mfkiwl/Zynq-SoM/schematic/DDR3L.kicad_sch

## KiCad design schematic/DDR3L.kicad_sch (2025-04-01)

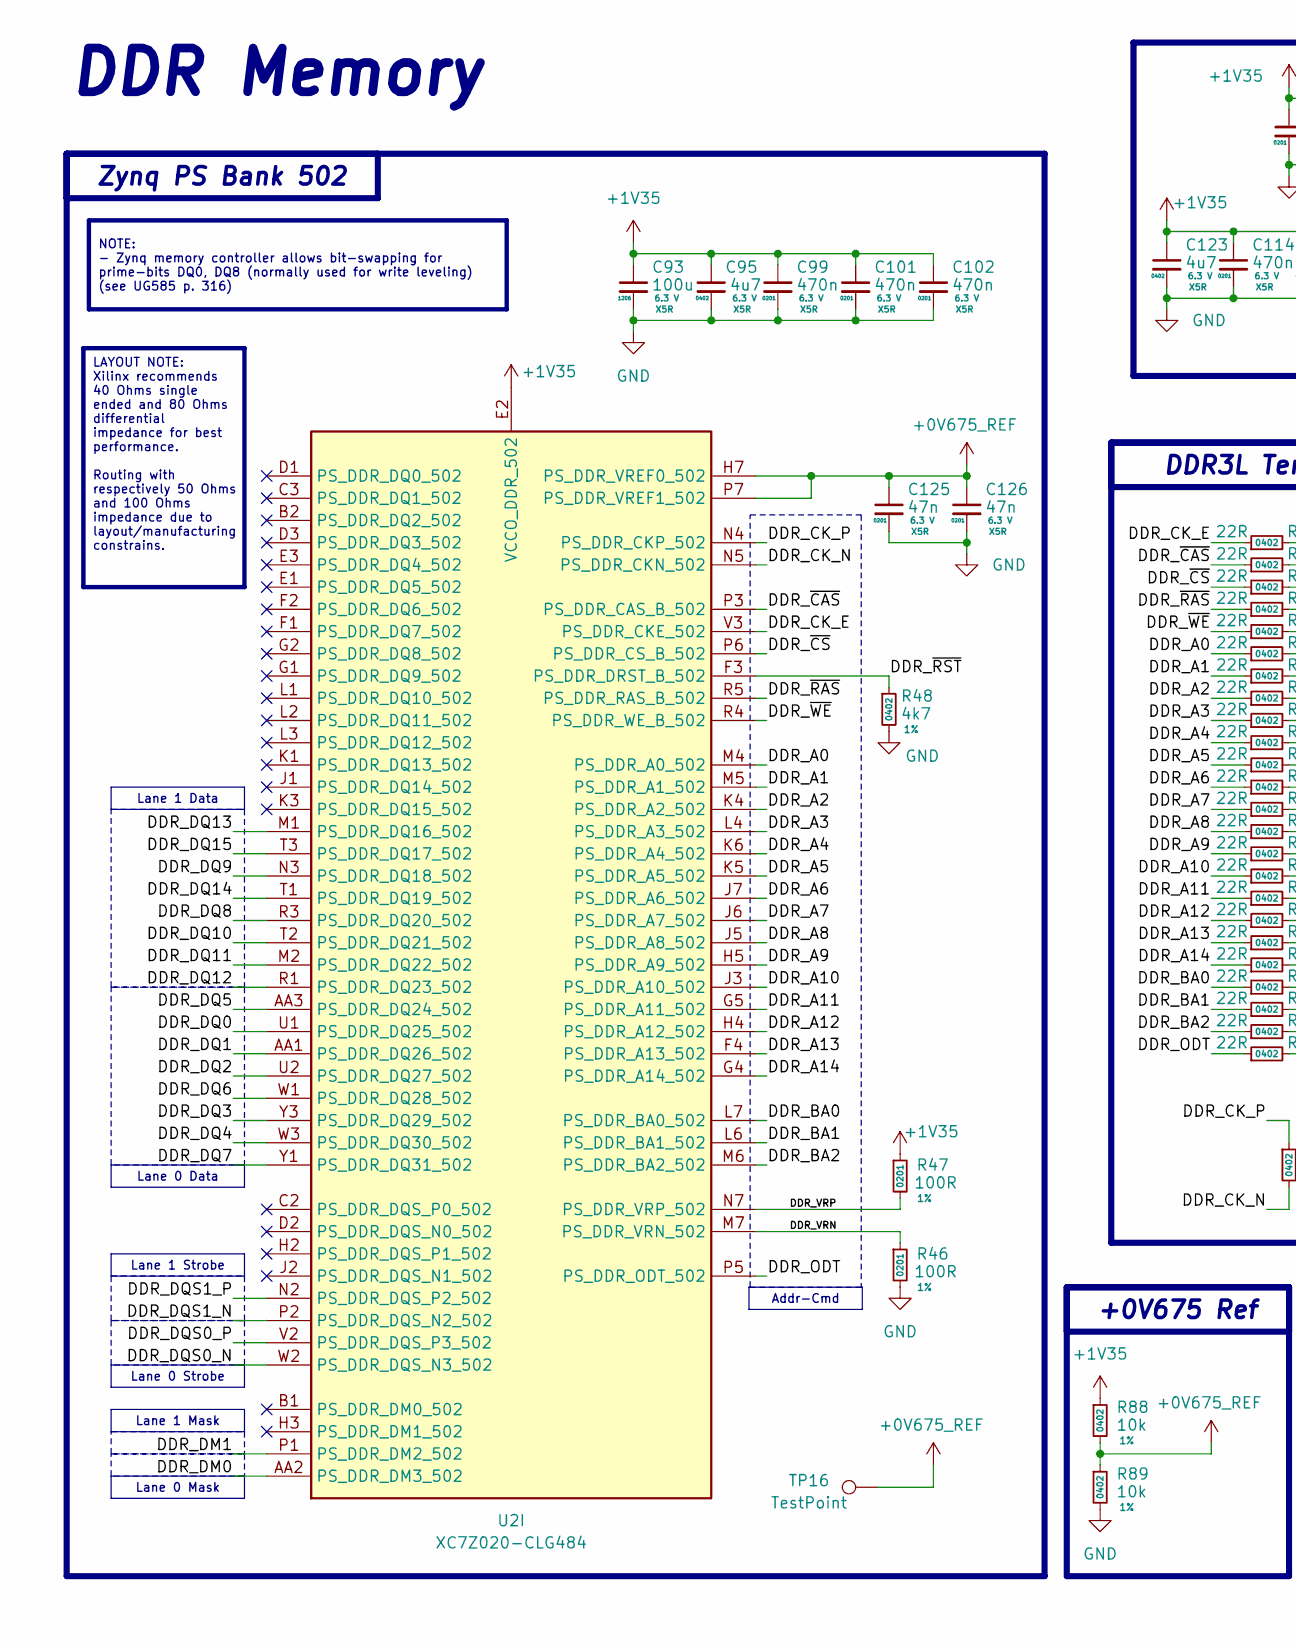
[picture p17: schematic DDR3L.kicad_sch, part in row 1, column 1]

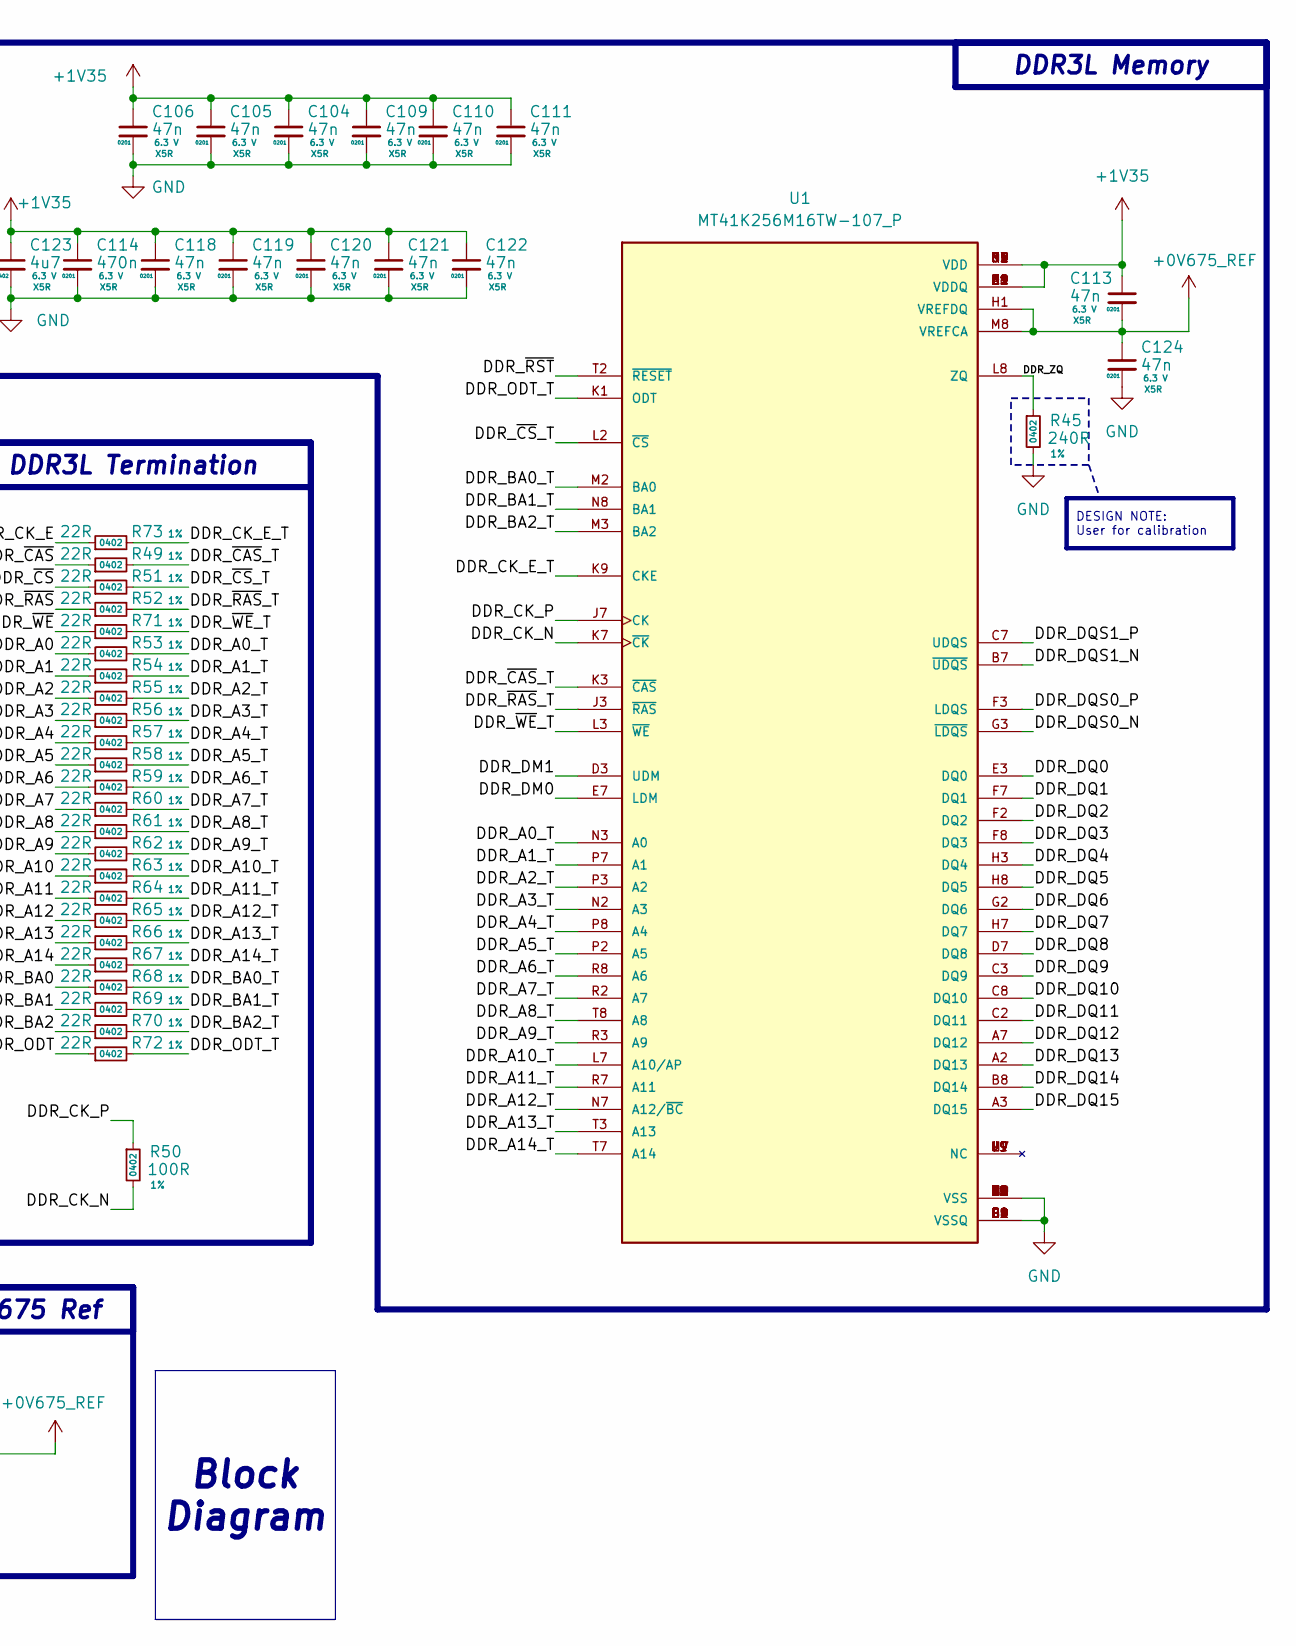
[picture p18: schematic DDR3L.kicad_sch, part in row 1, column 2]

Parts:
C93: 100u; C_1206_3216Metric; Rating 6.3 V; LCSC Part C15008
C95, C123: 4u7; C_0402_1005Metric; Rating 6.3 V; LCSC Part C368809
C99, C101, C102, C114: 470n; C_0201_0603Metric; Rating 6.3 V; LCSC Part C85926
C104, C105, C106, C109, C110, C111, C113, C118, C119, C120, C121, C122, C124, C125, C126: 47n; C_0201_0603Metric; Rating 6.3 V; LCSC Part C85925
R45: 240R; R_0402_1005Metric; Tolerance 1%; LCSC Part C25094
R46, R47: 100R; R_0201_0603Metric; Tolerance 1%; LCSC Part C270336
R48: 4k7; R_0402_1005Metric; Tolerance 1%; LCSC Part C25940
R49, R51, R52, R53, R54, R55, R56, R57, R58, R59, R60, R61, R62, R63, R64, R65, R66, R67, R68, R69, R70, R71, R72, R73: 22R; R_0402_1005Metric; Tolerance 1%; LCSC Part C114765/C25105
R50: 100R; R_0402_1005Metric; Tolerance 1%; LCSC Part C25138
R88, R89: 10k; R_0402_1005Metric; Tolerance 1%; LCSC Part C25744/gia
TP16: TestPoint; TestPoint_Pad_D0.7mm
U1: MT41K256M16TW-107_P; BGA96C80P9X16_1400X800X120; PARTREV P; LCSC Part gia
U2: XC7Z020-CLG484; CLG484_XIL-L_new; LCSC Part gia

Connections:
+0V675_REF: C113.2, C124.1, C125.1, C126.1, R88.2, R89.1, TP16.1, U1.H1 (VREFDQ), U1.M8 (VREFCA), U2.H7 (PS_DDR_VREF0_502), U2.P7 (PS_DDR_VREF1_502)
+1V35: C93.1, C95.1, C99.1, C101.1, C102.1, C104.1, C105.1, C106.1, C109.1, C110.1, C111.1, C113.1, C114.1, C118.1, C119.1, C120.1, C121.1, C122.1, C123.1, R47.1, R88.1, U1.A1 (VDDQ), U1.A8 (VDDQ), U1.B2 (VDD), U1.C1 (VDDQ), U1.C9 (VDDQ), U1.D2 (VDDQ), U1.D9 (VDD), U1.E9 (VDDQ), U1.F1 (VDDQ), U1.G7 (VDD), U1.H2 (VDDQ), U1.H9 (VDDQ), U1.K2 (VDD), U1.K8 (VDD), U1.N1 (VDD), U1.N9 (VDD), U1.R1 (VDD), U1.R9 (VDD), U2.E2 (VCCO_DDR_502), U2.F5 (VCCO_DDR_502), U2.H1 (VCCO_DDR_502), U2.J4 (VCCO_DDR_502), U2.K7 (VCCO_DDR_502), U2.M3 (VCCO_DDR_502), U2.N6 (VCCO_DDR_502), U2.R2 (VCCO_DDR_502), U2.V1 (VCCO_DDR_502)
DDR_A0: R53.1, U2.M4 (PS_DDR_A0_502)
DDR_A0_T: R53.2, U1.N3 (A0)
DDR_A1: R54.1, U2.M5 (PS_DDR_A1_502)
DDR_A1_T: R54.2, U1.P7 (A1)
DDR_A2: R55.1, U2.K4 (PS_DDR_A2_502)
DDR_A2_T: R55.2, U1.P3 (A2)
DDR_A3: R56.1, U2.L4 (PS_DDR_A3_502)
DDR_A3_T: R56.2, U1.N2 (A3)
DDR_A4: R57.1, U2.K6 (PS_DDR_A4_502)
DDR_A4_T: R57.2, U1.P8 (A4)
DDR_A5: R58.1, U2.K5 (PS_DDR_A5_502)
DDR_A5_T: R58.2, U1.P2 (A5)
DDR_A6: R59.1, U2.J7 (PS_DDR_A6_502)
DDR_A6_T: R59.2, U1.R8 (A6)
DDR_A7: R60.1, U2.J6 (PS_DDR_A7_502)
DDR_A7_T: R60.2, U1.R2 (A7)
DDR_A8: R61.1, U2.J5 (PS_DDR_A8_502)
DDR_A8_T: R61.2, U1.T8 (A8)
DDR_A9: R62.1, U2.H5 (PS_DDR_A9_502)
DDR_A9_T: R62.2, U1.R3 (A9)
DDR_A10: R63.1, U2.J3 (PS_DDR_A10_502)
DDR_A10_T: R63.2, U1.L7 (A10/AP)
DDR_A11: R64.1, U2.G5 (PS_DDR_A11_502)
DDR_A11_T: R64.2, U1.R7 (A11)
DDR_A12: R65.1, U2.H4 (PS_DDR_A12_502)
DDR_A12_T: R65.2, U1.N7 (A12/~BC)
DDR_A13: R66.1, U2.F4 (PS_DDR_A13_502)
DDR_A13_T: R66.2, U1.T3 (A13)
DDR_A14: R67.1, U2.G4 (PS_DDR_A14_502)
DDR_A14_T: R67.2, U1.T7 (A14)
DDR_BA0: R68.1, U2.L7 (PS_DDR_BA0_502)
DDR_BA0_T: R68.2, U1.M2 (BA0)
DDR_BA1: R69.1, U2.L6 (PS_DDR_BA1_502)
DDR_BA1_T: R69.2, U1.N8 (BA1)
DDR_BA2: R70.1, U2.M6 (PS_DDR_BA2_502)
DDR_BA2_T: R70.2, U1.M3 (BA2)
DDR_CK_E: R73.1, U2.V3 (PS_DDR_CKE_502)
DDR_CK_E_T: R73.2, U1.K9 (CKE)
DDR_CK_N: R50.2, U1.K7 (~CK), U2.N5 (PS_DDR_CKN_502)
DDR_CK_P: R50.1, U1.J7 (CK), U2.N4 (PS_DDR_CKP_502)
DDR_DM0: U1.E7 (LDM), U2.AA2 (PS_DDR_DM3_502)
DDR_DM1: U1.D3 (UDM), U2.P1 (PS_DDR_DM2_502)
DDR_DQ0: U1.E3 (DQ0), U2.U1 (PS_DDR_DQ25_502)
DDR_DQ1: U1.F7 (DQ1), U2.AA1 (PS_DDR_DQ26_502)
DDR_DQ2: U1.F2 (DQ2), U2.U2 (PS_DDR_DQ27_502)
DDR_DQ3: U1.F8 (DQ3), U2.Y3 (PS_DDR_DQ29_502)
DDR_DQ4: U1.H3 (DQ4), U2.W3 (PS_DDR_DQ30_502)
DDR_DQ5: U1.H8 (DQ5), U2.AA3 (PS_DDR_DQ24_502)
DDR_DQ6: U1.G2 (DQ6), U2.W1 (PS_DDR_DQ28_502)
DDR_DQ7: U1.H7 (DQ7), U2.Y1 (PS_DDR_DQ31_502)
DDR_DQ8: U1.D7 (DQ8), U2.R3 (PS_DDR_DQ20_502)
DDR_DQ9: U1.C3 (DQ9), U2.N3 (PS_DDR_DQ18_502)
DDR_DQ10: U1.C8 (DQ10), U2.T2 (PS_DDR_DQ21_502)
DDR_DQ11: U1.C2 (DQ11), U2.M2 (PS_DDR_DQ22_502)
DDR_DQ12: U1.A7 (DQ12), U2.R1 (PS_DDR_DQ23_502)
DDR_DQ13: U1.A2 (DQ13), U2.M1 (PS_DDR_DQ16_502)
DDR_DQ14: U1.B8 (DQ14), U2.T1 (PS_DDR_DQ19_502)
DDR_DQ15: U1.A3 (DQ15), U2.T3 (PS_DDR_DQ17_502)
DDR_DQS0_N: U1.G3 (~LDQS), U2.W2 (PS_DDR_DQS_N3_502)
DDR_DQS0_P: U1.F3 (LDQS), U2.V2 (PS_DDR_DQS_P3_502)
DDR_DQS1_N: U1.B7 (~UDQS), U2.P2 (PS_DDR_DQS_N2_502)
DDR_DQS1_P: U1.C7 (UDQS), U2.N2 (PS_DDR_DQS_P2_502)
DDR_ODT: R72.1, U2.P5 (PS_DDR_ODT_502)
DDR_ODT_T: R72.2, U1.K1 (ODT)
DDR_VRN: R46.1, U2.M7 (PS_DDR_VRN_502)
DDR_VRP: R47.2, U2.N7 (PS_DDR_VRP_502)
DDR_ZQ: R45.1, U1.L8 (ZQ)
DDR_~CAS: R49.1, U2.P3 (PS_DDR_CAS_B_502)
DDR_~CAS_T: R49.2, U1.K3 (~CAS)
DDR_~CS: R51.1, U2.P6 (PS_DDR_CS_B_502)
DDR_~CS_T: R51.2, U1.L2 (~CS)
DDR_~RAS: R52.1, U2.R5 (PS_DDR_RAS_B_502)
DDR_~RAS_T: R52.2, U1.J3 (~RAS)
DDR_~RST: R48.1, U1.T2 (~RESET), U2.F3 (PS_DDR_DRST_B_502)
DDR_~WE: R71.1, U2.R4 (PS_DDR_WE_B_502)
DDR_~WE_T: R71.2, U1.L3 (~WE)
GND: C93.2, C95.2, C99.2, C101.2, C102.2, C104.2, C105.2, C106.2, C109.2, C110.2, C111.2, C114.2, C118.2, C119.2, C120.2, C121.2, C122.2, C123.2, C124.2, C125.2, C126.2, R45.2, R46.2, R48.2, R89.2, U1.A9 (VSS), U1.B1 (VSSQ), U1.B3 (VSS), U1.B9 (VSSQ), U1.D1 (VSSQ), U1.D8 (VSSQ), U1.E1 (VSS), U1.E2 (VSSQ), U1.E8 (VSSQ), U1.F9 (VSSQ), U1.G1 (VSSQ), U1.G8 (VSS), U1.G9 (VSSQ), U1.J2 (VSS), U1.J8 (VSS), U1.M1 (VSS), U1.M9 (VSS), U1.P1 (VSS), U1.P9 (VSS), U1.T1 (VSS), U1.T9 (VSS)
unnamed: U1.J1 (NC), U1.J9 (NC), U1.L1 (NC), U1.L9 (NC), U1.M7 (NC)

Notes on the sheet:
DDR Memory
Zynq PS Bank 502
Lane 1 Strobe
Lane 1 Data
Lane 0 Mask
DESIGN NOTE: User for calibration
Addr-Cmd
NOTE: - Zynq memory controller allows bit-swapping for prime-bits DQ0, DQ8 (normally used for write leveling) (see UG585 p. 316)
Block Diagram
Lane 0 Data
LAYOUT NOTE: Xilinx recommends 40 Ohms single ended and 80 Ohms differential impedance for best performance. Routing with respectively 50 Ohms and 100 Ohms impedance due to layout/manufacturing constrains.
+0V675 Ref
DDR3L Memory
Lane 1 Mask
Lane 0 Strobe
DDR3L Termination
