mfkiwl/Zynq-SoM/schematic/Ethernet PHY.kicad_sch

## KiCad design schematic/Ethernet PHY.kicad_sch (2025-04-01)

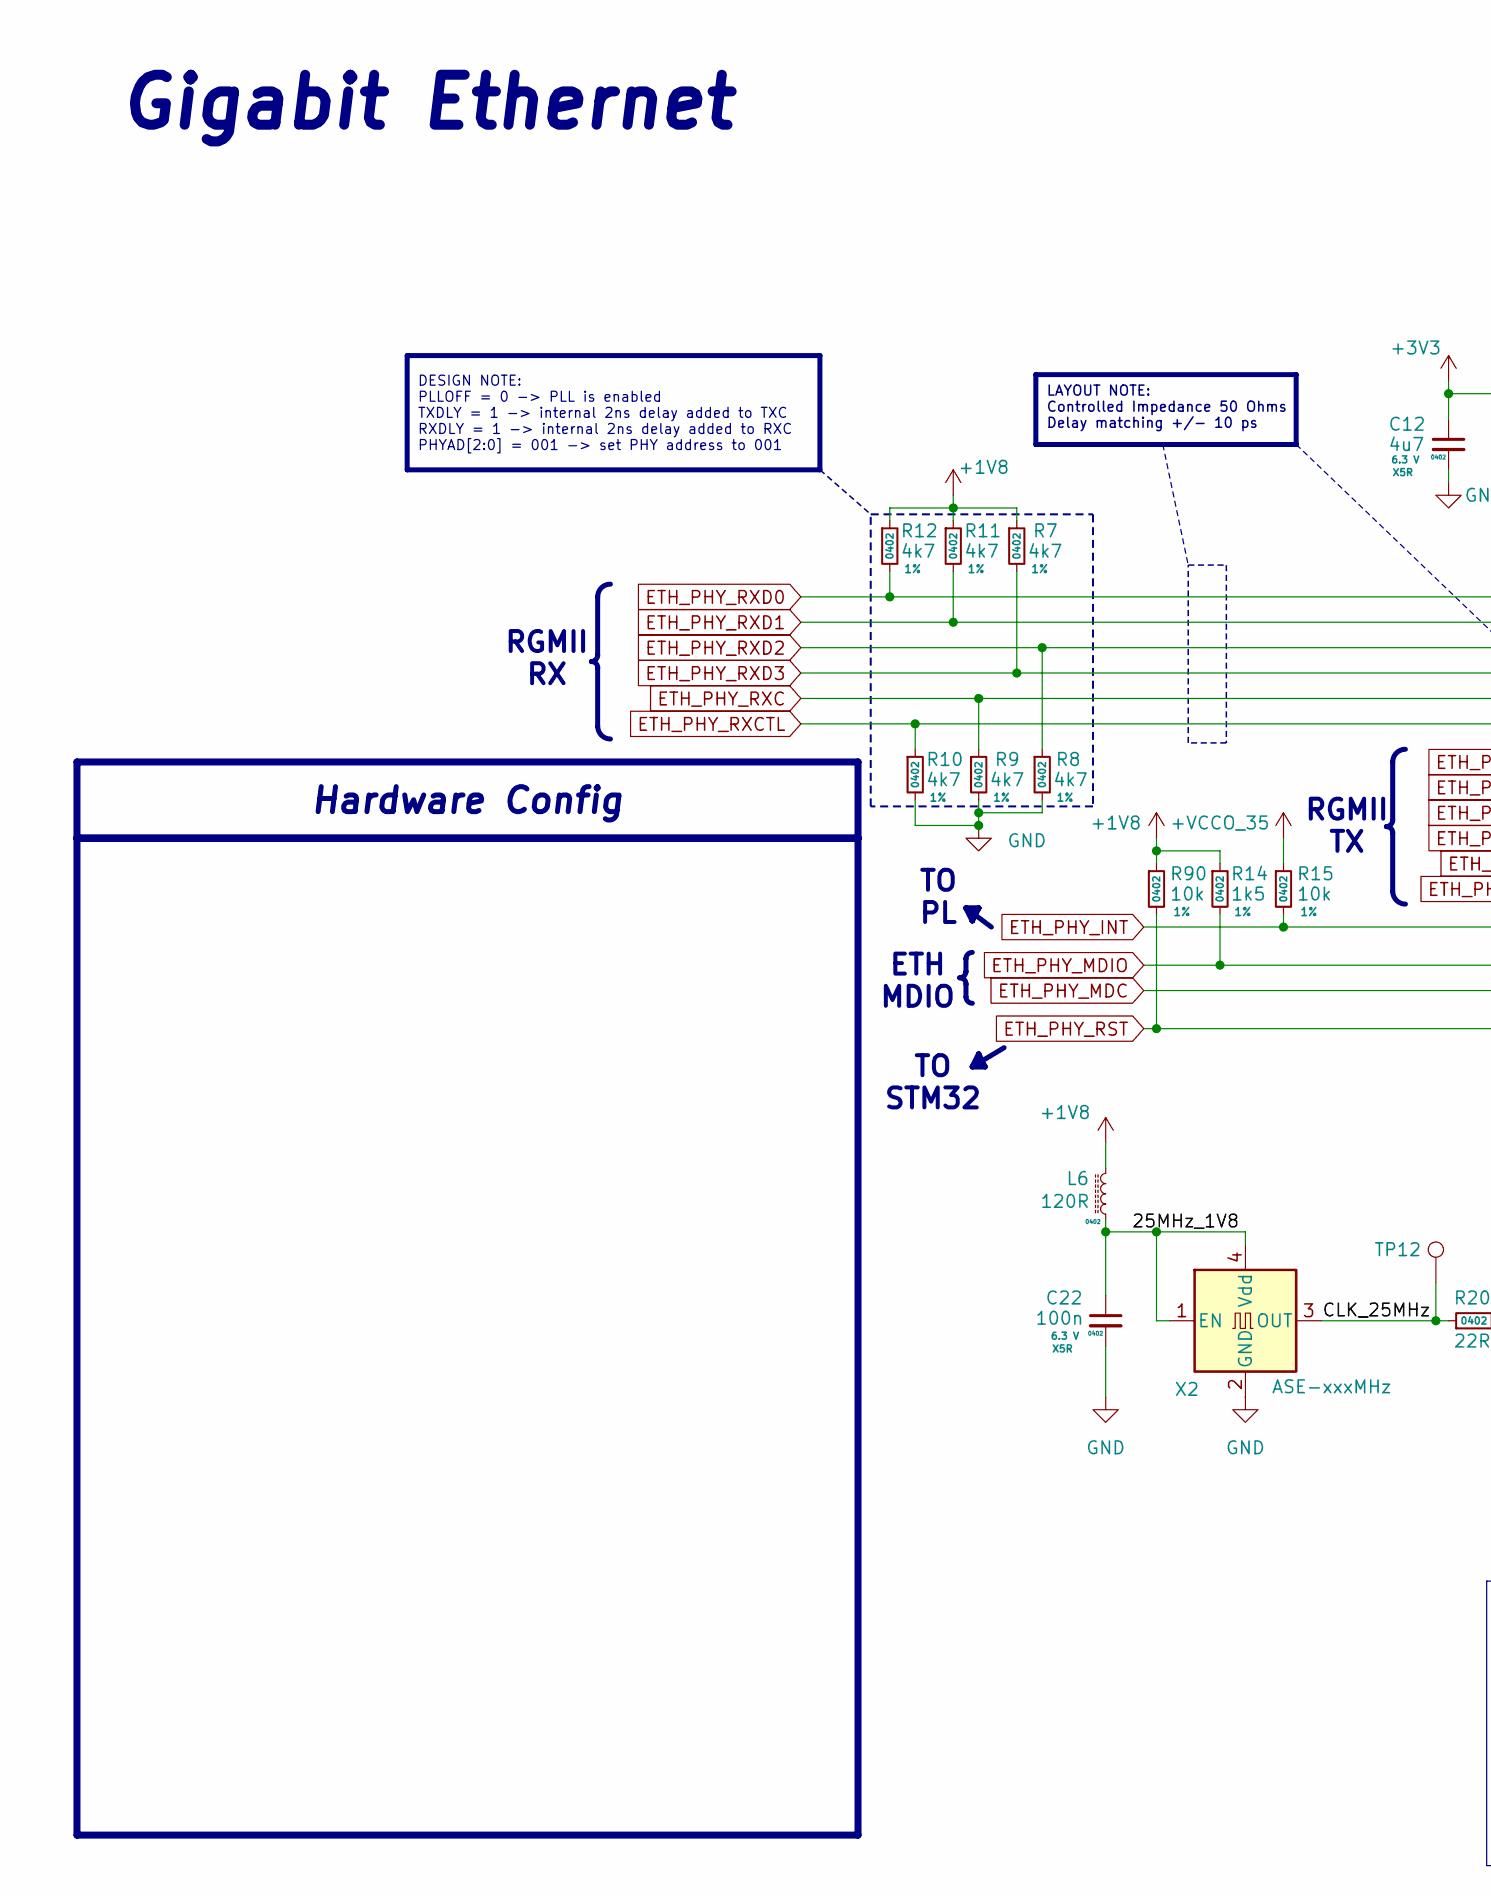
[picture p19: schematic Ethernet PHY.kicad_sch, part in row 1, column 1]

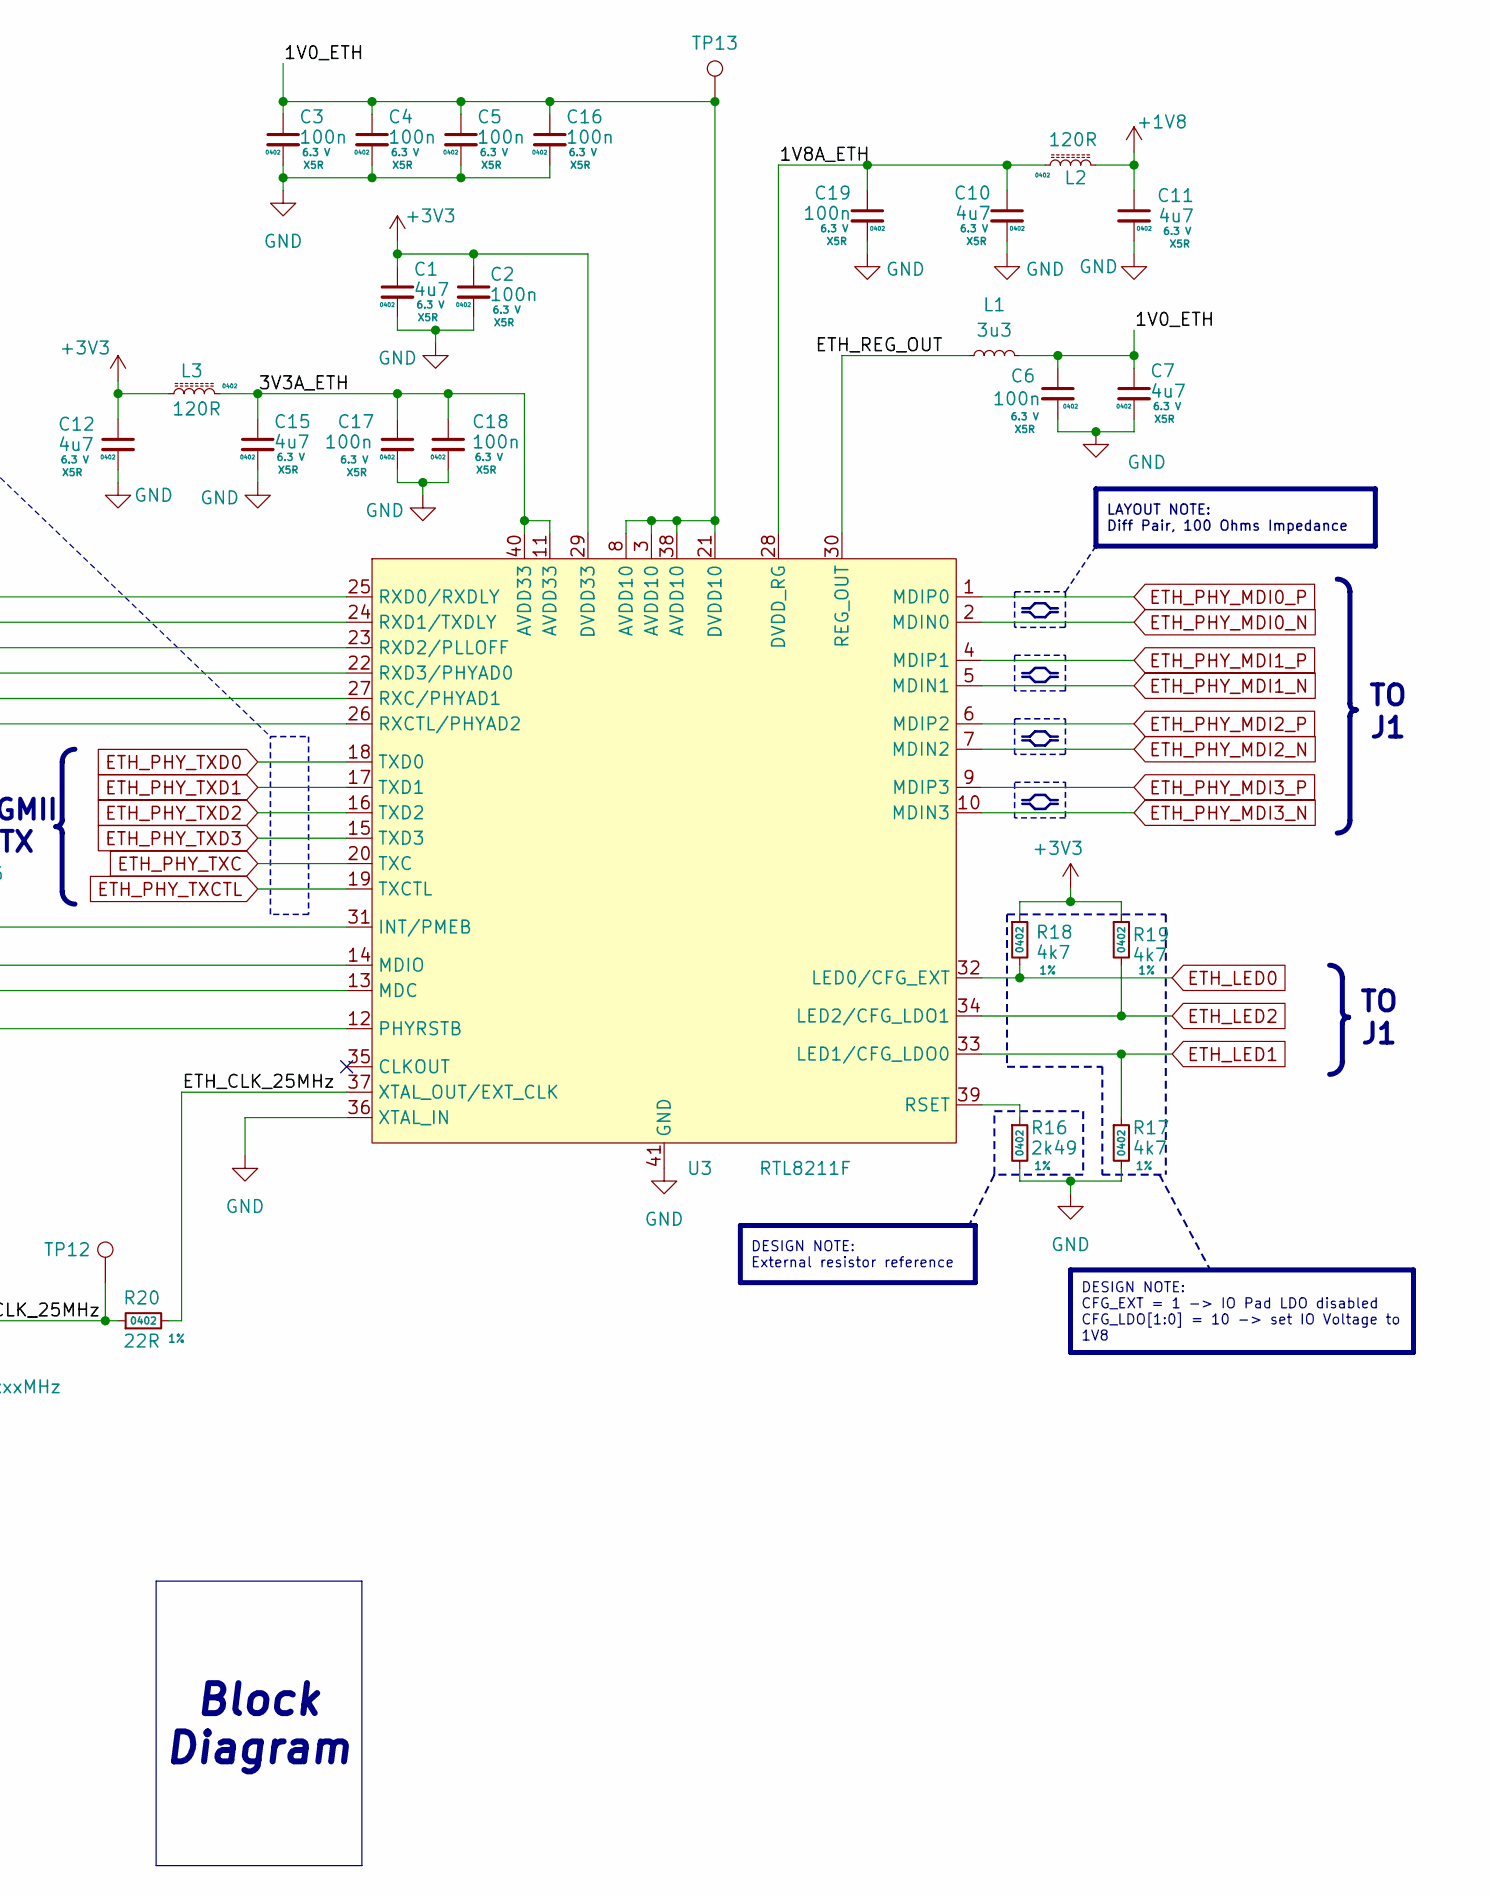
[picture p20: schematic Ethernet PHY.kicad_sch, part in row 1, column 2]

Parts:
C1, C7, C10, C11, C12, C15: 4u7; C_0402_1005Metric; Rating 6.3 V; LCSC Part C368809
C2, C3, C4, C5, C6, C16, C17, C18, C19, C22: 100n; C_0402_1005Metric; Rating 6.3 V; LCSC Part gia
L1: 3u3; L_0806_2.0x1.6mm; LCSC Part C98336
L2, L3, L6: 120R; L_0402_1005Metric; LCSC Part C275478
R7, R8, R9, R10, R11, R12, R17, R18, R19: 4k7; R_0402_1005Metric; Tolerance 1%; LCSC Part C25940
R14: 1k5; R_0402_1005Metric; Tolerance 1%; LCSC Part C25867
R15, R90: 10k; R_0402_1005Metric; Tolerance 1%; LCSC Part C25744/gia
R16: 2k49; R_0402_1005Metric; Tolerance 1%; LCSC Part C25884
R20: 22R; R_0402_1005Metric; Tolerance 1%; LCSC Part C114765/C25105
TP12, TP13: TestPoint; TestPoint_Pad_D0.7mm
U3: RTL8211F; RTL8211F-CG_RTK-L; LCSC Part C187932
X2: ASE-xxxMHz; Oscillator_SMD_Kyocera_4PIN_2.0x1.6mm; Digikey KC2016Z25.0000C1KX00

Connections:
1V0_ETH: C3.1, C4.1, C5.1, C6.1, C7.1, C16.1, L1.2, TP13.1, U3.3 (AVDD10), U3.8 (AVDD10), U3.21 (DVDD10), U3.38 (AVDD10)
1V8A_ETH: C10.1, C19.1, L2.1, U3.28 (DVDD_RG)
3V3A_ETH: C15.1, C17.1, C18.1, L3.2, U3.11 (AVDD33), U3.40 (AVDD33)
25MHz_1V8: C22.1, L6.1, X2.1 (EN), X2.4 (Vdd)
+1V8: C11.1, L2.2, L6.2, R7.1, R11.1, R12.1, R14.1, R90.1
+3V3: C1.1, C2.1, C12.1, L3.1, R18.1, R19.1, U3.29 (DVDD33)
+VCCO_35: R15.1
CLK_25MHz: R20.1, TP12.1, X2.3 (OUT)
ETH_CLK_25MHz: R20.2, U3.37 (XTAL_OUT/EXT_CLK)
ETH_LED0: R18.2, U3.32 (LED0/CFG_EXT)
ETH_LED1: R17.1, U3.33 (LED1/CFG_LDO0)
ETH_LED2: R19.2, U3.34 (LED2/CFG_LDO1)
ETH_PHY_INT: R15.2, U3.31 (INT/PMEB)
ETH_PHY_MDC: U3.13 (MDC)
ETH_PHY_MDI0_N: U3.2 (MDIN0)
ETH_PHY_MDI0_P: U3.1 (MDIP0)
ETH_PHY_MDI1_N: U3.5 (MDIN1)
ETH_PHY_MDI1_P: U3.4 (MDIP1)
ETH_PHY_MDI2_N: U3.7 (MDIN2)
ETH_PHY_MDI2_P: U3.6 (MDIP2)
ETH_PHY_MDI3_N: U3.10 (MDIN3)
ETH_PHY_MDI3_P: U3.9 (MDIP3)
ETH_PHY_MDIO: R14.2, U3.14 (MDIO)
ETH_PHY_RST: R90.2, U3.12 (PHYRSTB)
ETH_PHY_RXC: R9.1, U3.27 (RXC/PHYAD1)
ETH_PHY_RXCTL: R10.1, U3.26 (RXCTL/PHYAD2)
ETH_PHY_RXD0: R12.2, U3.25 (RXD0/RXDLY)
ETH_PHY_RXD1: R11.2, U3.24 (RXD1/TXDLY)
ETH_PHY_RXD2: R8.1, U3.23 (RXD2/PLLOFF)
ETH_PHY_RXD3: R7.2, U3.22 (RXD3/PHYAD0)
ETH_PHY_TXC: U3.20 (TXC)
ETH_PHY_TXCTL: U3.19 (TXCTL)
ETH_PHY_TXD0: U3.18 (TXD0)
ETH_PHY_TXD1: U3.17 (TXD1)
ETH_PHY_TXD2: U3.16 (TXD2)
ETH_PHY_TXD3: U3.15 (TXD3)
ETH_REG_OUT: L1.1, U3.30 (REG_OUT)
GND: C1.2, C2.2, C3.2, C4.2, C5.2, C6.2, C7.2, C10.2, C11.2, C12.2, C15.2, C16.2, C17.2, C18.2, C19.2, C22.2, R8.2, R9.2, R10.2, R16.2, R17.2, U3.36 (XTAL_IN), U3.41 (GND), X2.2 (GND)
unnamed: R16.1, U3.39 (RSET)

Notes on the sheet:
ETH MDIO
TO J1
RGMII TX
TO STM32
RGMII RX
TO PL
Gigabit Ethernet
DESIGN NOTE: CFG_EXT = 1 -> IO Pad LDO disabled CFG_LDO[1:0] = 10 -> set IO Voltage to 1V8
Hardware Config
LAYOUT NOTE: Diff Pair, 100 Ohms Impedance
Block Diagram
DESIGN NOTE: PLLOFF = 0 -> PLL is enabled TXDLY = 1 -> internal 2ns delay added to TXC RXDLY = 1 -> internal 2ns delay added to RXC PHYAD[2:0] = 001 -> set PHY address to 001
LAYOUT NOTE: Controlled Impedance 50 Ohms Delay matching +/- 10 ps
DESIGN NOTE: External resistor reference
