mfkiwl/Zynq-SoM/schematic/Power.kicad_sch

## KiCad design schematic/Power.kicad_sch (2025-04-01)

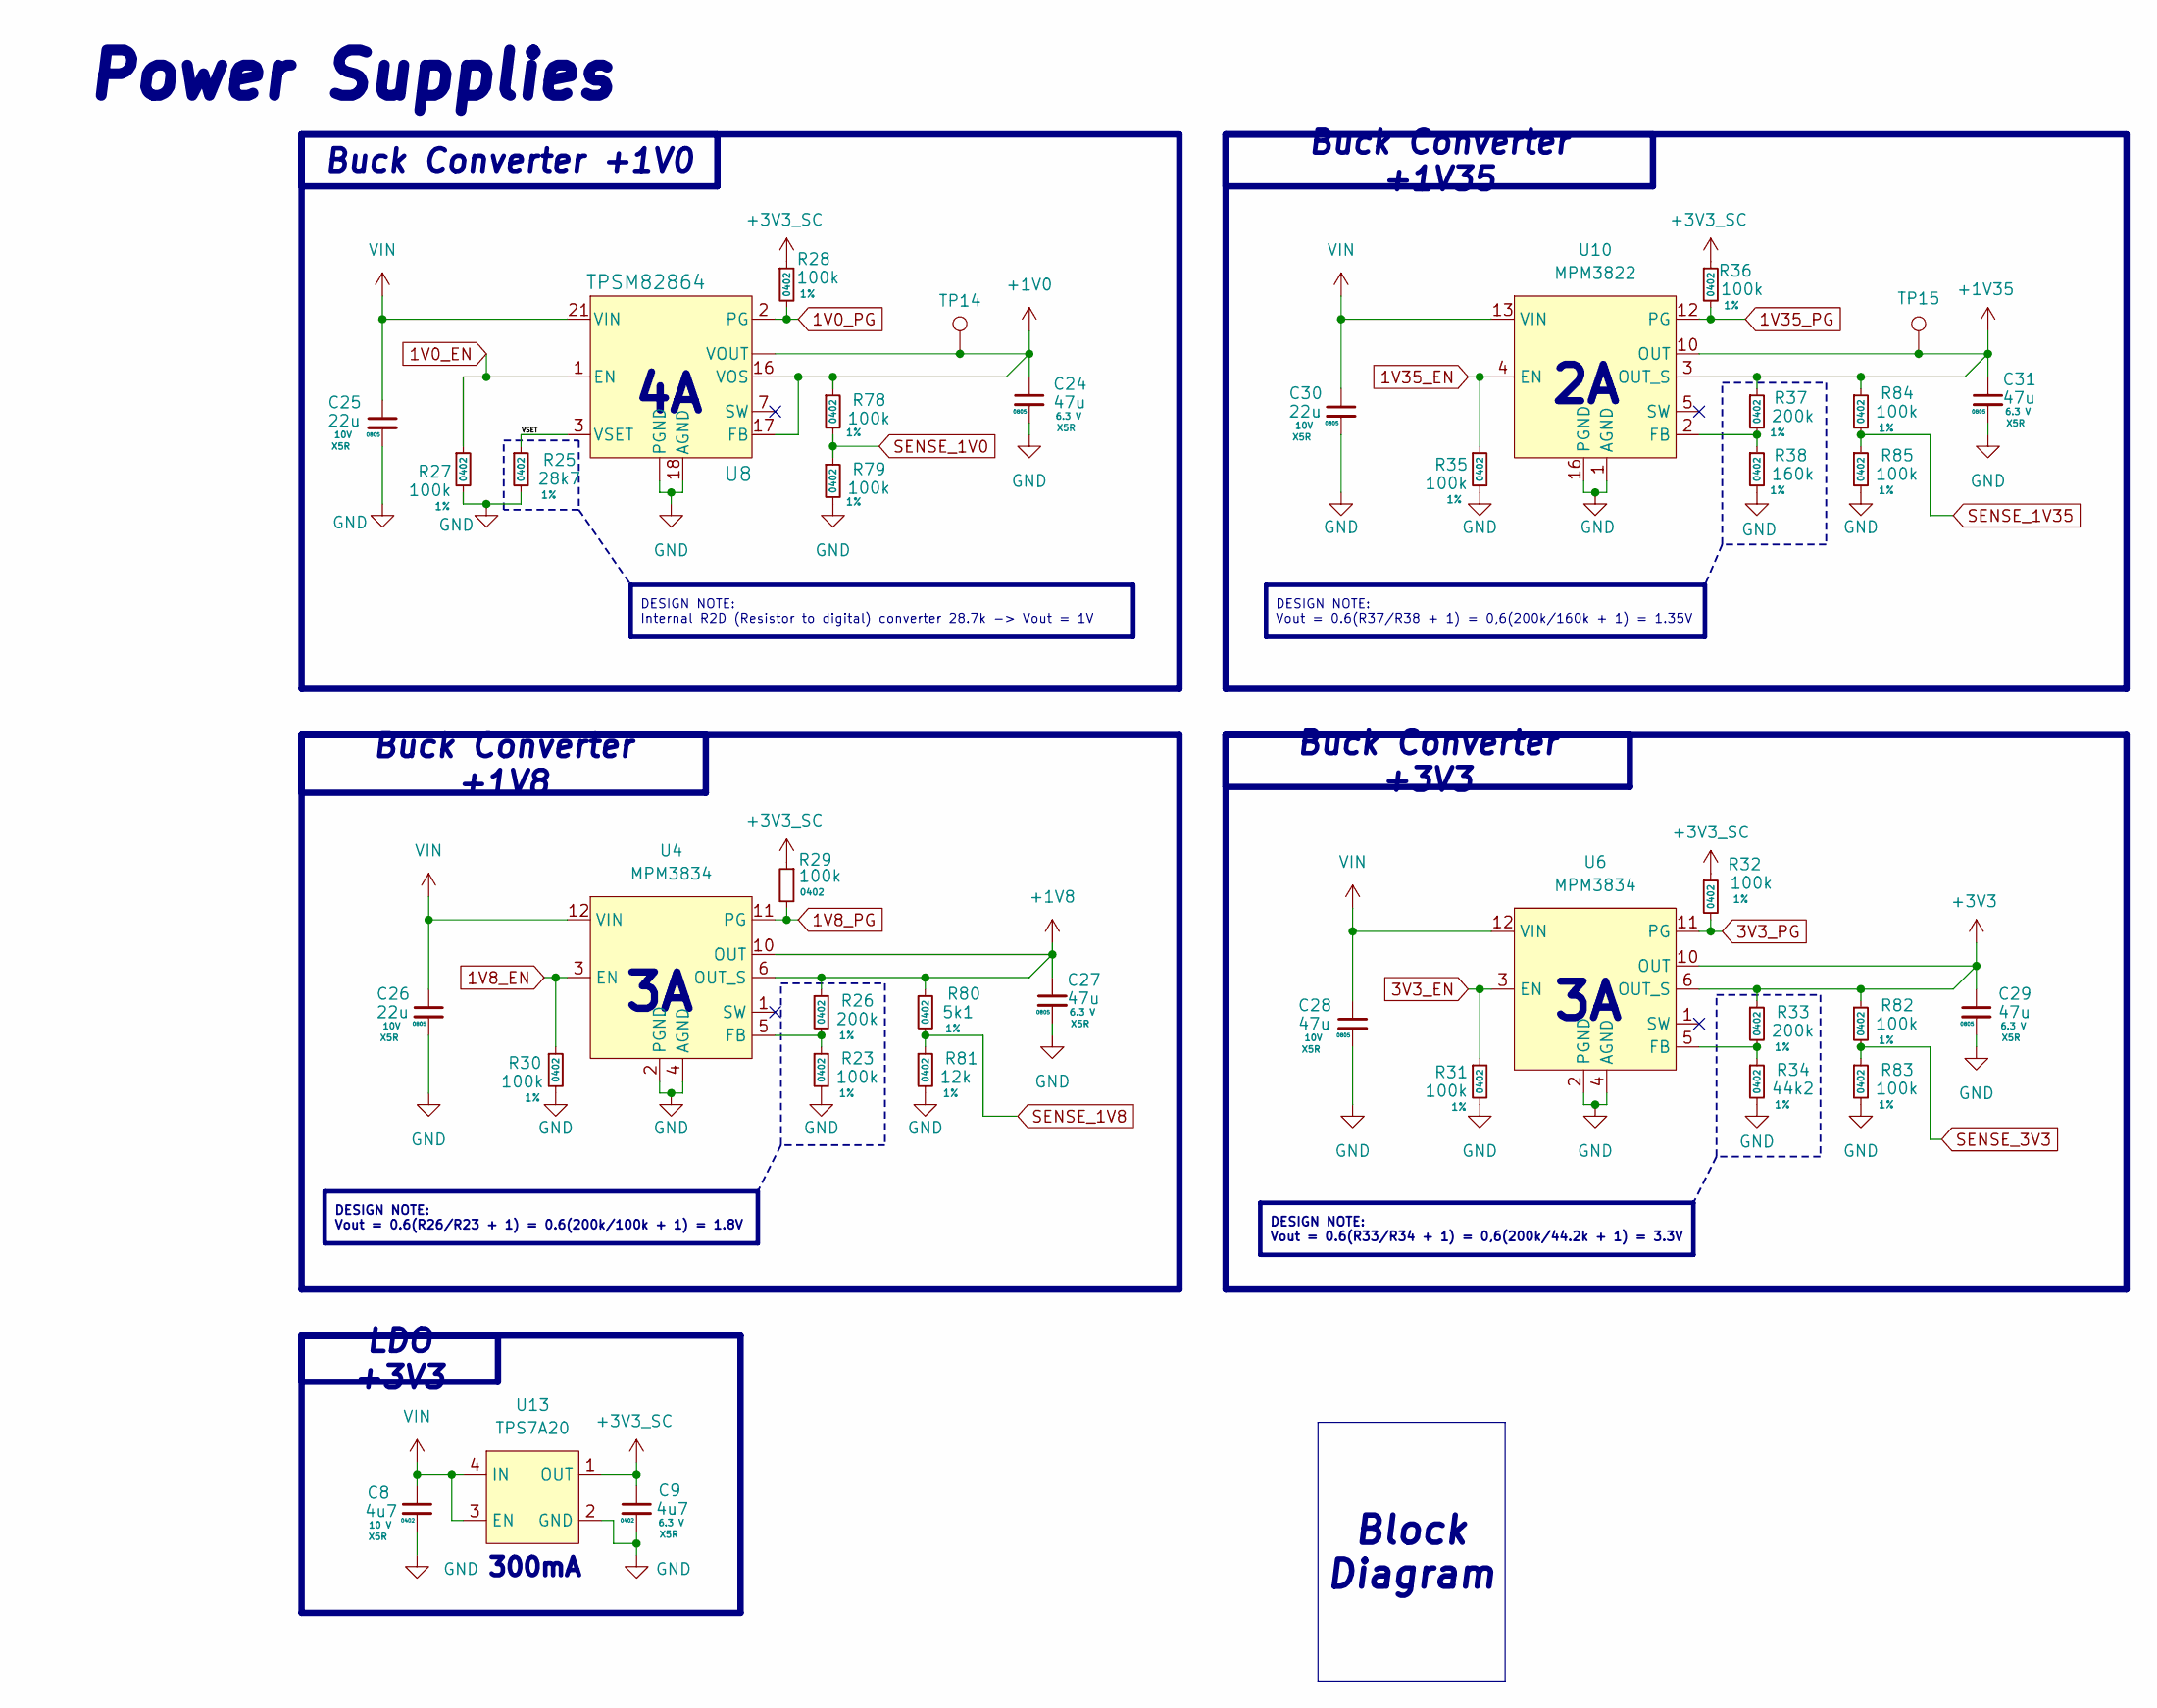
[picture p21: schematic Power.kicad_sch]

Parts:
C8: 4u7; C_0402_1005Metric; Rating 10 V; LCSC Part C368809
C9: 4u7; C_0402_1005Metric; Rating 6.3 V; LCSC Part C368809
C24, C27, C29, C31: 47u; C_0805_2012Metric; Rating 6.3 V; LCSC Part C16780
C25, C26, C30: 22u; C_0805_2012Metric; Rating 10V; LCSC Part C98190
C28: 47u; C_0805_2012Metric; Rating 10V; LCSC Part C16780
R23, R27, R28, R30, R31, R32, R35, R36, R78, R79, R82, R83, R84, R85: 100k; R_0402_1005Metric; Tolerance 1%; LCSC Part C60491
R25: 28k7; R_0402_1005Metric; Tolerance 1%; LCSC Part C26972
R26, R33, R37: 200k; R_0402_1005Metric; Tolerance 1%; LCSC Part C137903
R29: 100k; R_0402_1005Metric; LCSC Part C60491
R34: 44k2; R_0402_1005Metric; Tolerance 1%; LCSC Part C25895
R38: 160k; R_0402_1005Metric; Tolerance 1%; LCSC Part C25757
R80: 5k1; R_0402_1005Metric; Tolerance 1%; LCSC Part gia
R81: 12k; R_0402_1005Metric; Tolerance 1%; LCSC Part gia
TP14, TP15: TestPoint; TestPoint_Pad_D0.7mm
U4, U6: MPM3834; Digikey MPM3834CGPA-Z
U8: TPSM82864; B0QFN_RDJ; LCSC Part C5219321
U10: MPM3822; QFN_2p5x3p5x1p6_MNP; Digikey 1589-2037-1-ND
U13: TPS7A20; TLV707; LCSC Part gia

Connections:
1V0_EN: R27.1, U8.1 (EN)
1V0_PG: R28.2, U8.2 (PG)
1V8_EN: R30.1, U4.3 (EN)
1V8_PG: R29.2, U4.11 (PG)
1V35_EN: R35.1, U10.4 (EN)
1V35_PG: R36.2, U10.12 (PG)
3V3_EN: R31.1, U6.3 (EN)
3V3_PG: R32.2, U6.11 (PG)
+1V0: C24.1, R78.1, TP14.1, U8. (PGND), U8.12 (VOUT), U8.13 (VOUT), U8.14 (VOUT), U8.15 (VOUT), U8.16 (VOS), U8.17 (FB)
+1V8: C27.1, R26.1, R80.1, U4.6 (OUT_S), U4.9 (OUT), U4.10 (OUT)
+1V35: C31.1, R37.1, R84.1, TP15.1, U10.3 (OUT_S), U10.10 (OUT)
+3V3: C29.1, R33.1, R82.1, U6.6 (OUT_S), U6.9 (OUT), U6.10 (OUT)
+3V3_SC: C9.1, R28.1, R29.1, R32.1, R36.1, U13.1 (OUT)
GND: C8.2, C9.2, C24.2, C25.2, C26.2, C27.2, C28.2, C29.2, C30.2, C31.2, R23.2, R25.2, R27.2, R30.2, R31.2, R34.2, R35.2, R38.2, R79.2, R81.2, R83.2, R85.2, U4.2 (PGND), U4.4 (AGND), U4.7 (PGND), U4.8 (PGND), U6.2 (PGND), U6.4 (AGND), U6.7 (PGND), U6.8 (PGND), U8. (PGND), U8.4 (PGND), U8.5 (PGND), U8.6 (PGND), U8.8 (PGND), U8.9 (PGND), U8.10 (PGND), U8.11 (PGND), U8.18 (AGND), U8.19 (PGND), U8.20 (PGND), U8.23 (PGND), U10.1 (AGND), U10.16 (PGND), U13.2 (GND), U13.5 (PAD)
unnamed: R23.1, R26.2, U4.5 (FB)
unnamed: R33.2, R34.1, U6.5 (FB)
unnamed: R37.2, R38.1, U10.2 (FB)
unnamed: U10.5 (SW), U10.15 (SW)
unnamed: U10.17 (DNC), U10.18 (DNC)
SENSE_1V0: R78.2, R79.1
SENSE_1V8: R80.2, R81.1
SENSE_1V35: R84.2, R85.1
SENSE_3V3: R82.2, R83.1
VIN: C8.1, C25.1, C26.1, C28.1, C30.1, U4.12 (VIN), U4.13 (VIN), U4.14 (VIN), U6.12 (VIN), U6.13 (VIN), U6.14 (VIN), U8.21 (VIN), U8.22 (VIN), U10.13 (VIN), U10.14 (VIN), U13.3 (EN), U13.4 (IN)
VSET: R25.1, U8.3 (VSET)

Notes on the sheet:
Power Supplies
300mA
Buck Converter +3V3
DESIGN NOTE: Internal R2D (Resistor to digital) converter 28.7k -> Vout = 1V
Block Diagram
DESIGN NOTE: Vout = 0.6(R33/R34 + 1) = 0,6(200k/44.2k + 1) = 3.3V
LDO +3V3
Buck Converter +1V35
DESIGN NOTE: Vout = 0.6(R37/R38 + 1) = 0,6(200k/160k + 1) = 1.35V
DESIGN NOTE: Vout = 0.6(R26/R23 + 1) = 0.6(200k/100k + 1) = 1.8V
Buck Converter +1V8
Buck Converter +1V0
