mfkiwl/Zynq-SoM/schematic/Sensors.kicad_sch

## KiCad design schematic/Sensors.kicad_sch (2025-04-01)

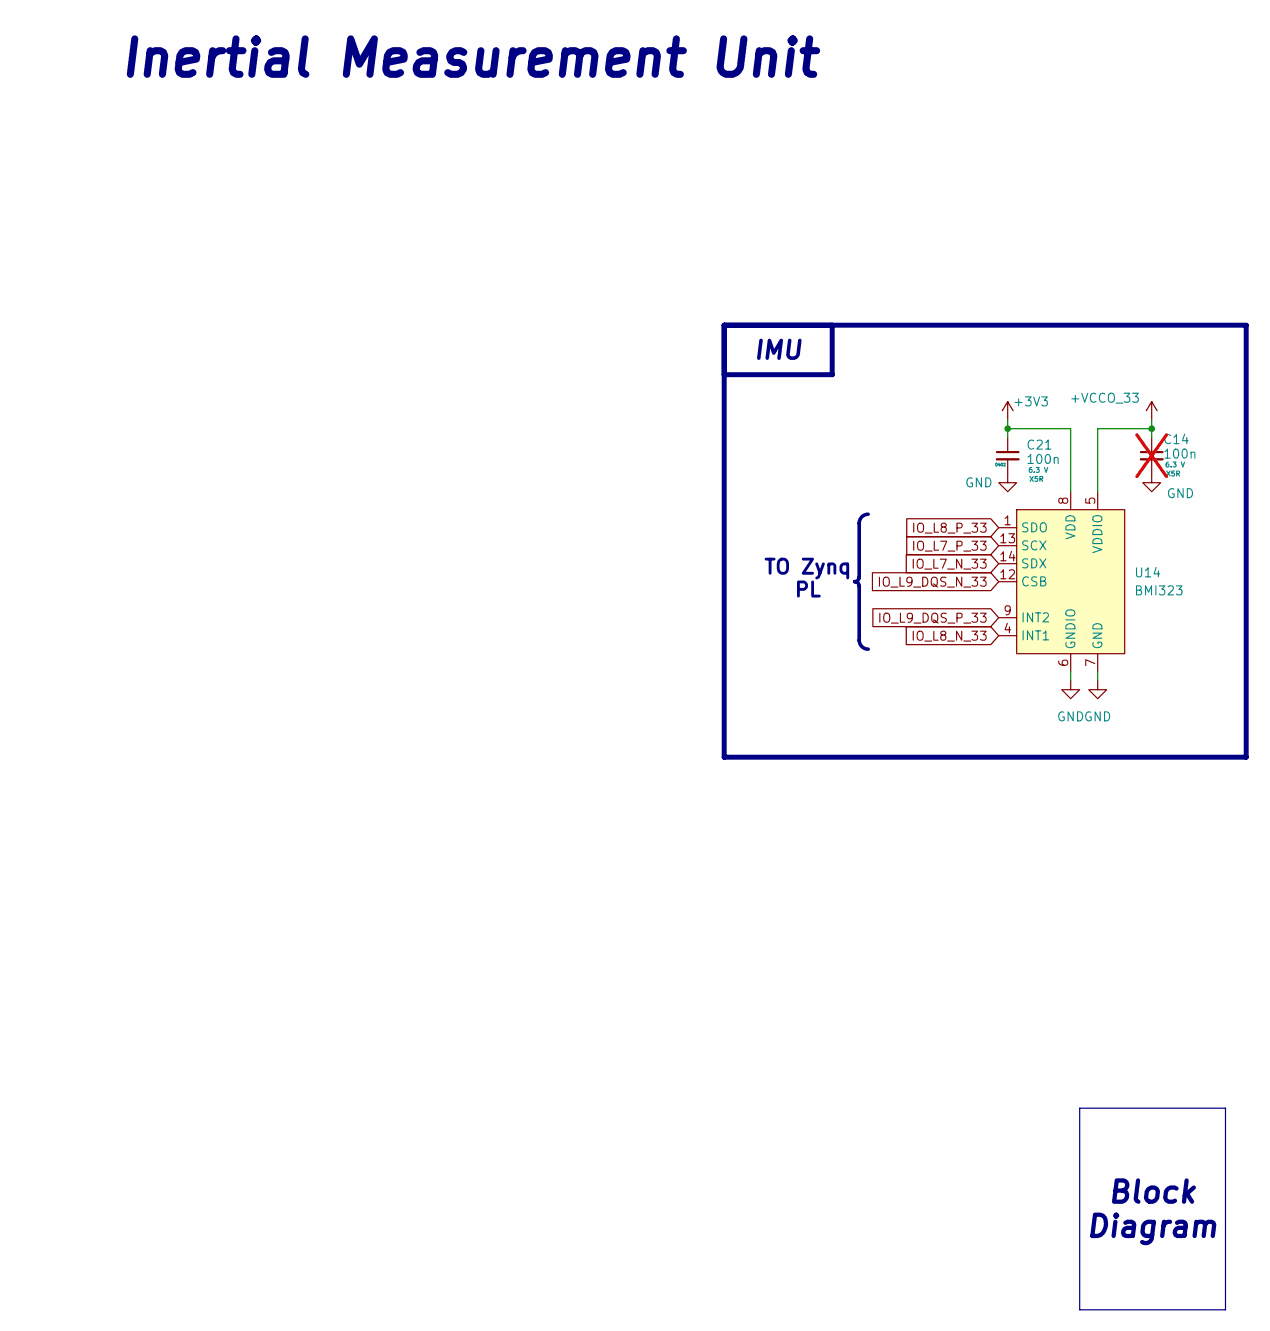
[picture p22: schematic Sensors.kicad_sch]

Parts:
C14: 100n; C_0402_1005Metric; Rating 6.3 V; not fitted
C21: 100n; C_0402_1005Metric; Rating 6.3 V; LCSC Part gia
U14: BMI323; BMI323_BOS; LCSC Part C5368700

Connections:
+3V3: C21.1, U14.8 (VDD)
+VCCO_33: C14.1, U14.5 (VDDIO)
GND: C14.2, C21.2, U14.6 (GNDIO), U14.7 (GND)
IO_L7_N_33: U14.14 (SDX)
IO_L7_P_33: U14.13 (SCX)
IO_L8_N_33: U14.4 (INT1)
IO_L8_P_33: U14.1 (SDO)
IO_L9_DQS_N_33: U14.12 (CSB)
IO_L9_DQS_P_33: U14.9 (INT2)
unnamed: U14.2 (NC), U14.3 (NC), U14.10 (NC), U14.11 (NC)

Notes on the sheet:
Inertial Measurement Unit
TO Zynq PL
Block Diagram
IMU
