mfkiwl/Zynq-SoM/schematic/connectors.kicad_sch

## KiCad design schematic/connectors.kicad_sch (2025-04-01)

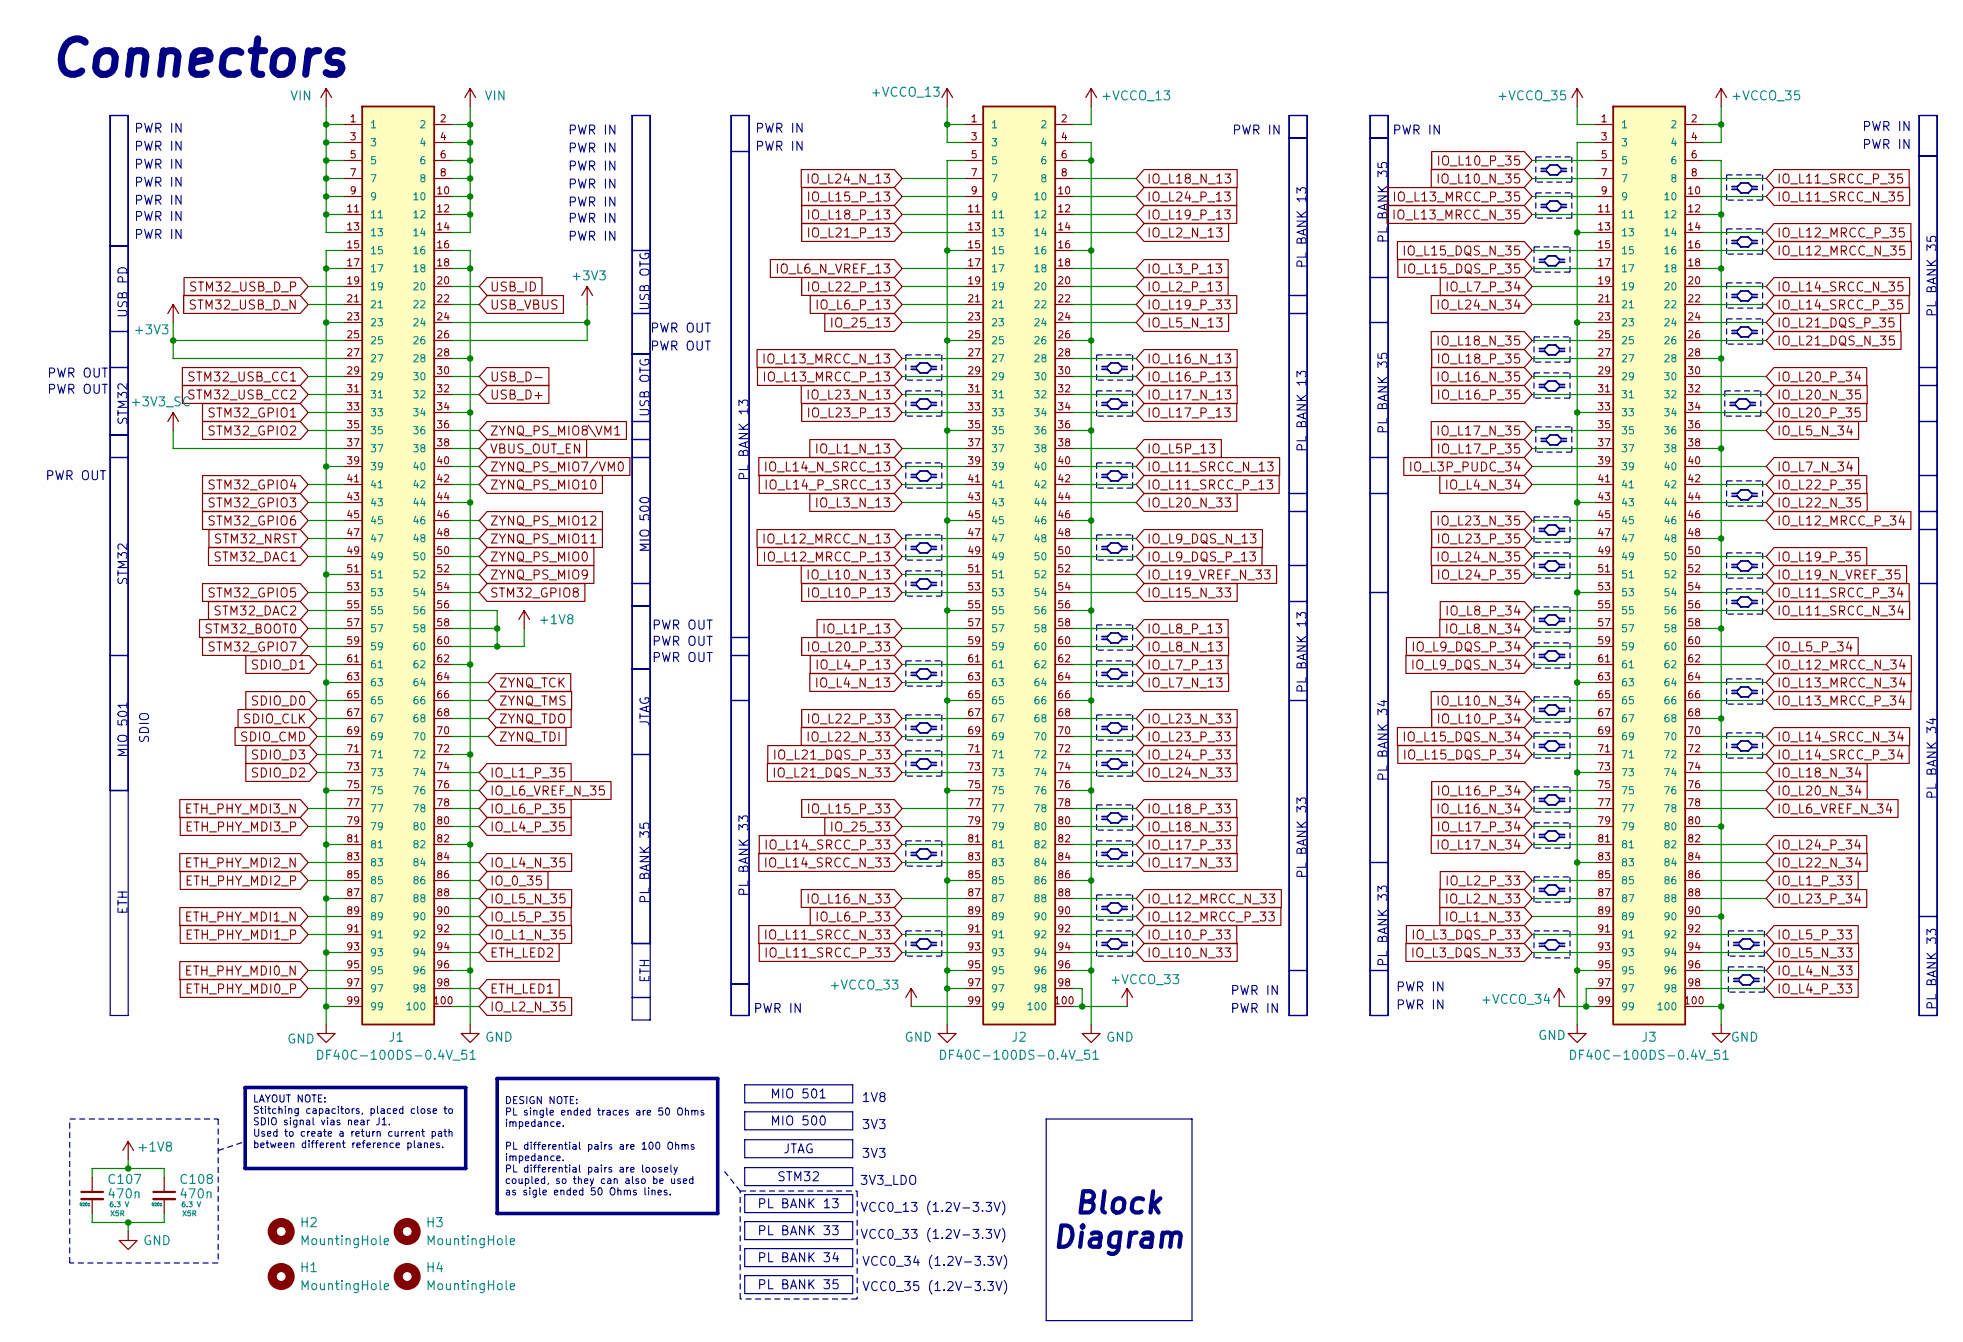
[picture p23: schematic connectors.kicad_sch]

Parts:
C107, C108: 470n; C_0201_0603Metric; Rating 6.3 V; LCSC Part C85926
H1, H2, H3, H4: MountingHole; MountingHole_2.7mm_M2.5_ISO14580_MOD
J1, J2, J3: DF40C-100DS-0.4V_51; HRS_DF40C-100DP-0.4V_51_; PARTREV 02/2020; Digikey DF40HC(3.0)-100DS-0.4V(51)

Connections:
+1V8: C107.1, C108.1, J1.56, J1.58, J1.60
+3V3: J1.24, J1.25, J1.26, J1.27
+3V3_SC: J1.37
+VCCO_13: J2.1, J2.2, J2.3
+VCCO_33: J2.98, J2.99, J2.100
+VCCO_34: J3.97, J3.99
+VCCO_35: J3.1, J3.2, J3.4
ETH_LED1: J1.98
ETH_LED2: J1.94
ETH_PHY_MDI0_N: J1.95
ETH_PHY_MDI0_P: J1.97
ETH_PHY_MDI1_N: J1.89
ETH_PHY_MDI1_P: J1.91
ETH_PHY_MDI2_N: J1.83
ETH_PHY_MDI2_P: J1.85
ETH_PHY_MDI3_N: J1.77
ETH_PHY_MDI3_P: J1.79
GND: C107.2, C108.2, J1.15, J1.16, J1.17, J1.18, J1.23, J1.28, J1.34, J1.39, J1.44, J1.51, J1.62, J1.63, J1.72, J1.75, J1.81, J1.82, J1.87, J1.93, J1.96, J1.99, J2.4, J2.5, J2.6, J2.15, J2.16, J2.25, J2.26, J2.35, J2.36, J2.45, J2.46, J2.55, J2.56, J2.65, J2.66, J2.75, J2.76, J2.85, J2.86, J2.95, J2.96, J2.97, J3.3, J3.6, J3.12, J3.13, J3.18, J3.23, J3.28, J3.33, J3.38, J3.43, J3.48, J3.53, J3.58, J3.63, J3.68, J3.73, J3.80, J3.83, J3.90, J3.95, J3.100
IO_0_35: J1.86
IO_25_13: J2.23
IO_25_33: J2.79
IO_L1P_13: J2.57
IO_L1_N_13: J2.37
IO_L1_N_33: J3.89
IO_L1_N_35: J1.92
IO_L1_P_33: J3.86
IO_L1_P_35: J1.74
IO_L2_N_13: J2.14
IO_L2_N_33: J3.87
IO_L2_N_35: J1.100
IO_L2_P_13: J2.20
IO_L2_P_33: J3.85
IO_L3P_PUDC_34: J3.39
IO_L3_DQS_N_33: J3.93
IO_L3_DQS_P_33: J3.91
IO_L3_N_13: J2.43
IO_L3_P_13: J2.18
IO_L4_N_13: J2.63
IO_L4_N_33: J3.96
IO_L4_N_34: J3.41
IO_L4_N_35: J1.84
IO_L4_P_13: J2.61
IO_L4_P_33: J3.98
IO_L4_P_35: J1.80
IO_L5P_13: J2.38
IO_L5_N_13: J2.24
IO_L5_N_33: J3.94
IO_L5_N_34: J3.36
IO_L5_N_35: J1.88
IO_L5_P_33: J3.92
IO_L5_P_34: J3.60
IO_L5_P_35: J1.90
IO_L6_N_VREF_13: J2.17
IO_L6_P_13: J2.21
IO_L6_P_33: J2.89
IO_L6_P_35: J1.78
IO_L6_VREF_N_34: J3.78
IO_L6_VREF_N_35: J1.76
IO_L7_N_13: J2.64
IO_L7_N_34: J3.40
IO_L7_P_13: J2.62
IO_L7_P_34: J3.19
IO_L8_N_13: J2.60
IO_L8_N_34: J3.57
IO_L8_P_13: J2.58
IO_L8_P_34: J3.55
IO_L9_DQS_N_13: J2.48
IO_L9_DQS_N_34: J3.61
IO_L9_DQS_P_13: J2.50
IO_L9_DQS_P_34: J3.59
IO_L10_N_13: J2.51
IO_L10_N_33: J2.94
IO_L10_N_34: J3.65
IO_L10_N_35: J3.7
IO_L10_P_13: J2.53
IO_L10_P_33: J2.92
IO_L10_P_34: J3.67
IO_L10_P_35: J3.5
IO_L11_SRCC_N_13: J2.40
IO_L11_SRCC_N_33: J2.91
IO_L11_SRCC_N_34: J3.56
IO_L11_SRCC_N_35: J3.10
IO_L11_SRCC_P_13: J2.42
IO_L11_SRCC_P_33: J2.93
IO_L11_SRCC_P_34: J3.54
IO_L11_SRCC_P_35: J3.8
IO_L12_MRCC_N_13: J2.47
IO_L12_MRCC_N_33: J2.88
IO_L12_MRCC_N_34: J3.62
IO_L12_MRCC_N_35: J3.16
IO_L12_MRCC_P_13: J2.49
IO_L12_MRCC_P_33: J2.90
IO_L12_MRCC_P_34: J3.46
IO_L12_MRCC_P_35: J3.14
IO_L13_MRCC_N_13: J2.27
IO_L13_MRCC_N_34: J3.64
IO_L13_MRCC_N_35: J3.11
IO_L13_MRCC_P_13: J2.29
IO_L13_MRCC_P_34: J3.66
IO_L13_MRCC_P_35: J3.9
IO_L14_N_SRCC_13: J2.39
IO_L14_P_SRCC_13: J2.41
IO_L14_SRCC_N_33: J2.83
IO_L14_SRCC_N_34: J3.70
IO_L14_SRCC_N_35: J3.20
IO_L14_SRCC_P_33: J2.81
IO_L14_SRCC_P_34: J3.72
IO_L14_SRCC_P_35: J3.22
IO_L15_DQS_N_34: J3.69
IO_L15_DQS_N_35: J3.15
IO_L15_DQS_P_34: J3.71
IO_L15_DQS_P_35: J3.17
IO_L15_N_33: J2.54
IO_L15_P_13: J2.9
IO_L15_P_33: J2.77
IO_L16_N_13: J2.28
IO_L16_N_33: J2.87
IO_L16_N_34: J3.77
IO_L16_N_35: J3.29
IO_L16_P_13: J2.30
IO_L16_P_34: J3.75
IO_L16_P_35: J3.31
IO_L17_N_13: J2.32
IO_L17_N_33: J2.84
IO_L17_N_34: J3.81
IO_L17_N_35: J3.35
IO_L17_P_13: J2.34
IO_L17_P_33: J2.82
IO_L17_P_34: J3.79
IO_L17_P_35: J3.37
IO_L18_N_13: J2.8
IO_L18_N_33: J2.80
IO_L18_N_34: J3.74
IO_L18_N_35: J3.25
IO_L18_P_13: J2.11
IO_L18_P_33: J2.78
IO_L18_P_35: J3.27
IO_L19_N_VREF_35: J3.52
IO_L19_P_13: J2.12
IO_L19_P_33: J2.22
IO_L19_P_35: J3.50
IO_L19_VREF_N_33: J2.52
IO_L20_N_33: J2.44
IO_L20_N_34: J3.76
IO_L20_N_35: J3.32
IO_L20_P_33: J2.59
IO_L20_P_34: J3.30
IO_L20_P_35: J3.34
IO_L21_DQS_N_33: J2.73
IO_L21_DQS_N_35: J3.26
IO_L21_DQS_P_33: J2.71
IO_L21_DQS_P_35: J3.24
IO_L21_P_13: J2.13
IO_L22_N_33: J2.69
IO_L22_N_34: J3.84
IO_L22_N_35: J3.44
IO_L22_P_13: J2.19
IO_L22_P_33: J2.67
IO_L22_P_35: J3.42
IO_L23_N_13: J2.31
IO_L23_N_33: J2.68
IO_L23_N_35: J3.45
IO_L23_P_13: J2.33
IO_L23_P_33: J2.70
IO_L23_P_34: J3.88
IO_L23_P_35: J3.47
IO_L24_N_13: J2.7
IO_L24_N_33: J2.74
IO_L24_N_34: J3.21
IO_L24_N_35: J3.49
IO_L24_P_13: J2.10
IO_L24_P_33: J2.72
IO_L24_P_34: J3.82
IO_L24_P_35: J3.51
SDIO_CLK: J1.67
SDIO_CMD: J1.69
SDIO_D0: J1.65
SDIO_D1: J1.61
SDIO_D2: J1.73
SDIO_D3: J1.71
STM32_BOOT0: J1.57
STM32_DAC1: J1.49
STM32_DAC2: J1.55
STM32_GPIO1: J1.33
STM32_GPIO2: J1.35
STM32_GPIO3: J1.43
STM32_GPIO4: J1.41
STM32_GPIO5: J1.53
STM32_GPIO6: J1.45
STM32_GPIO7: J1.59
STM32_GPIO8: J1.54
STM32_NRST: J1.47
STM32_USB_CC1: J1.29
STM32_USB_CC2: J1.31
STM32_USB_D_N: J1.21
STM32_USB_D_P: J1.19
USB_D+: J1.32
USB_D-: J1.30
USB_ID: J1.20
USB_VBUS: J1.22
VBUS_OUT_EN: J1.38
VIN: J1.1, J1.2, J1.3, J1.4, J1.5, J1.6, J1.7, J1.8, J1.9, J1.10, J1.11, J1.12, J1.13, J1.14
ZYNQ_PS_MIO0: J1.50
ZYNQ_PS_MIO7/VM0: J1.40
ZYNQ_PS_MIO8\VM1: J1.36
ZYNQ_PS_MIO9: J1.52
ZYNQ_PS_MIO10: J1.42
ZYNQ_PS_MIO11: J1.48
ZYNQ_PS_MIO12: J1.46
ZYNQ_TCK: J1.64
ZYNQ_TDI: J1.70
ZYNQ_TDO: J1.68
ZYNQ_TMS: J1.66

Notes on the sheet:
PWR IN
PL BANK 34
PL BANK 35
VCC0_35 (1.2V-3.3V)
USB OTG
PL BANK 33
PWR OUT
MIO 500
STM32
VCC0_13 (1.2V-3.3V)
3V3
VCC0_33 (1.2V-3.3V)
1V8
MIO 501
PL BANK 13
ETH
Connectors
JTAG
USB PD
VCC0_34 (1.2V-3.3V)
3V3_LDO
SDIO
LAYOUT NOTE: Stitching capacitors, placed close to SDIO signal vias near J1. Used to create a return current path between different reference planes.
Block Diagram
DESIGN NOTE: PL single ended traces are 50 Ohms impedance. PL differential pairs are 100 Ohms impedance. PL differential pairs are loosely coupled, so they can also be used as sigle ended 50 Ohms lines.
