mfkiwl/Zynq-SoM/schematic/emmc.kicad_sch

## KiCad design schematic/emmc.kicad_sch (2025-04-01)

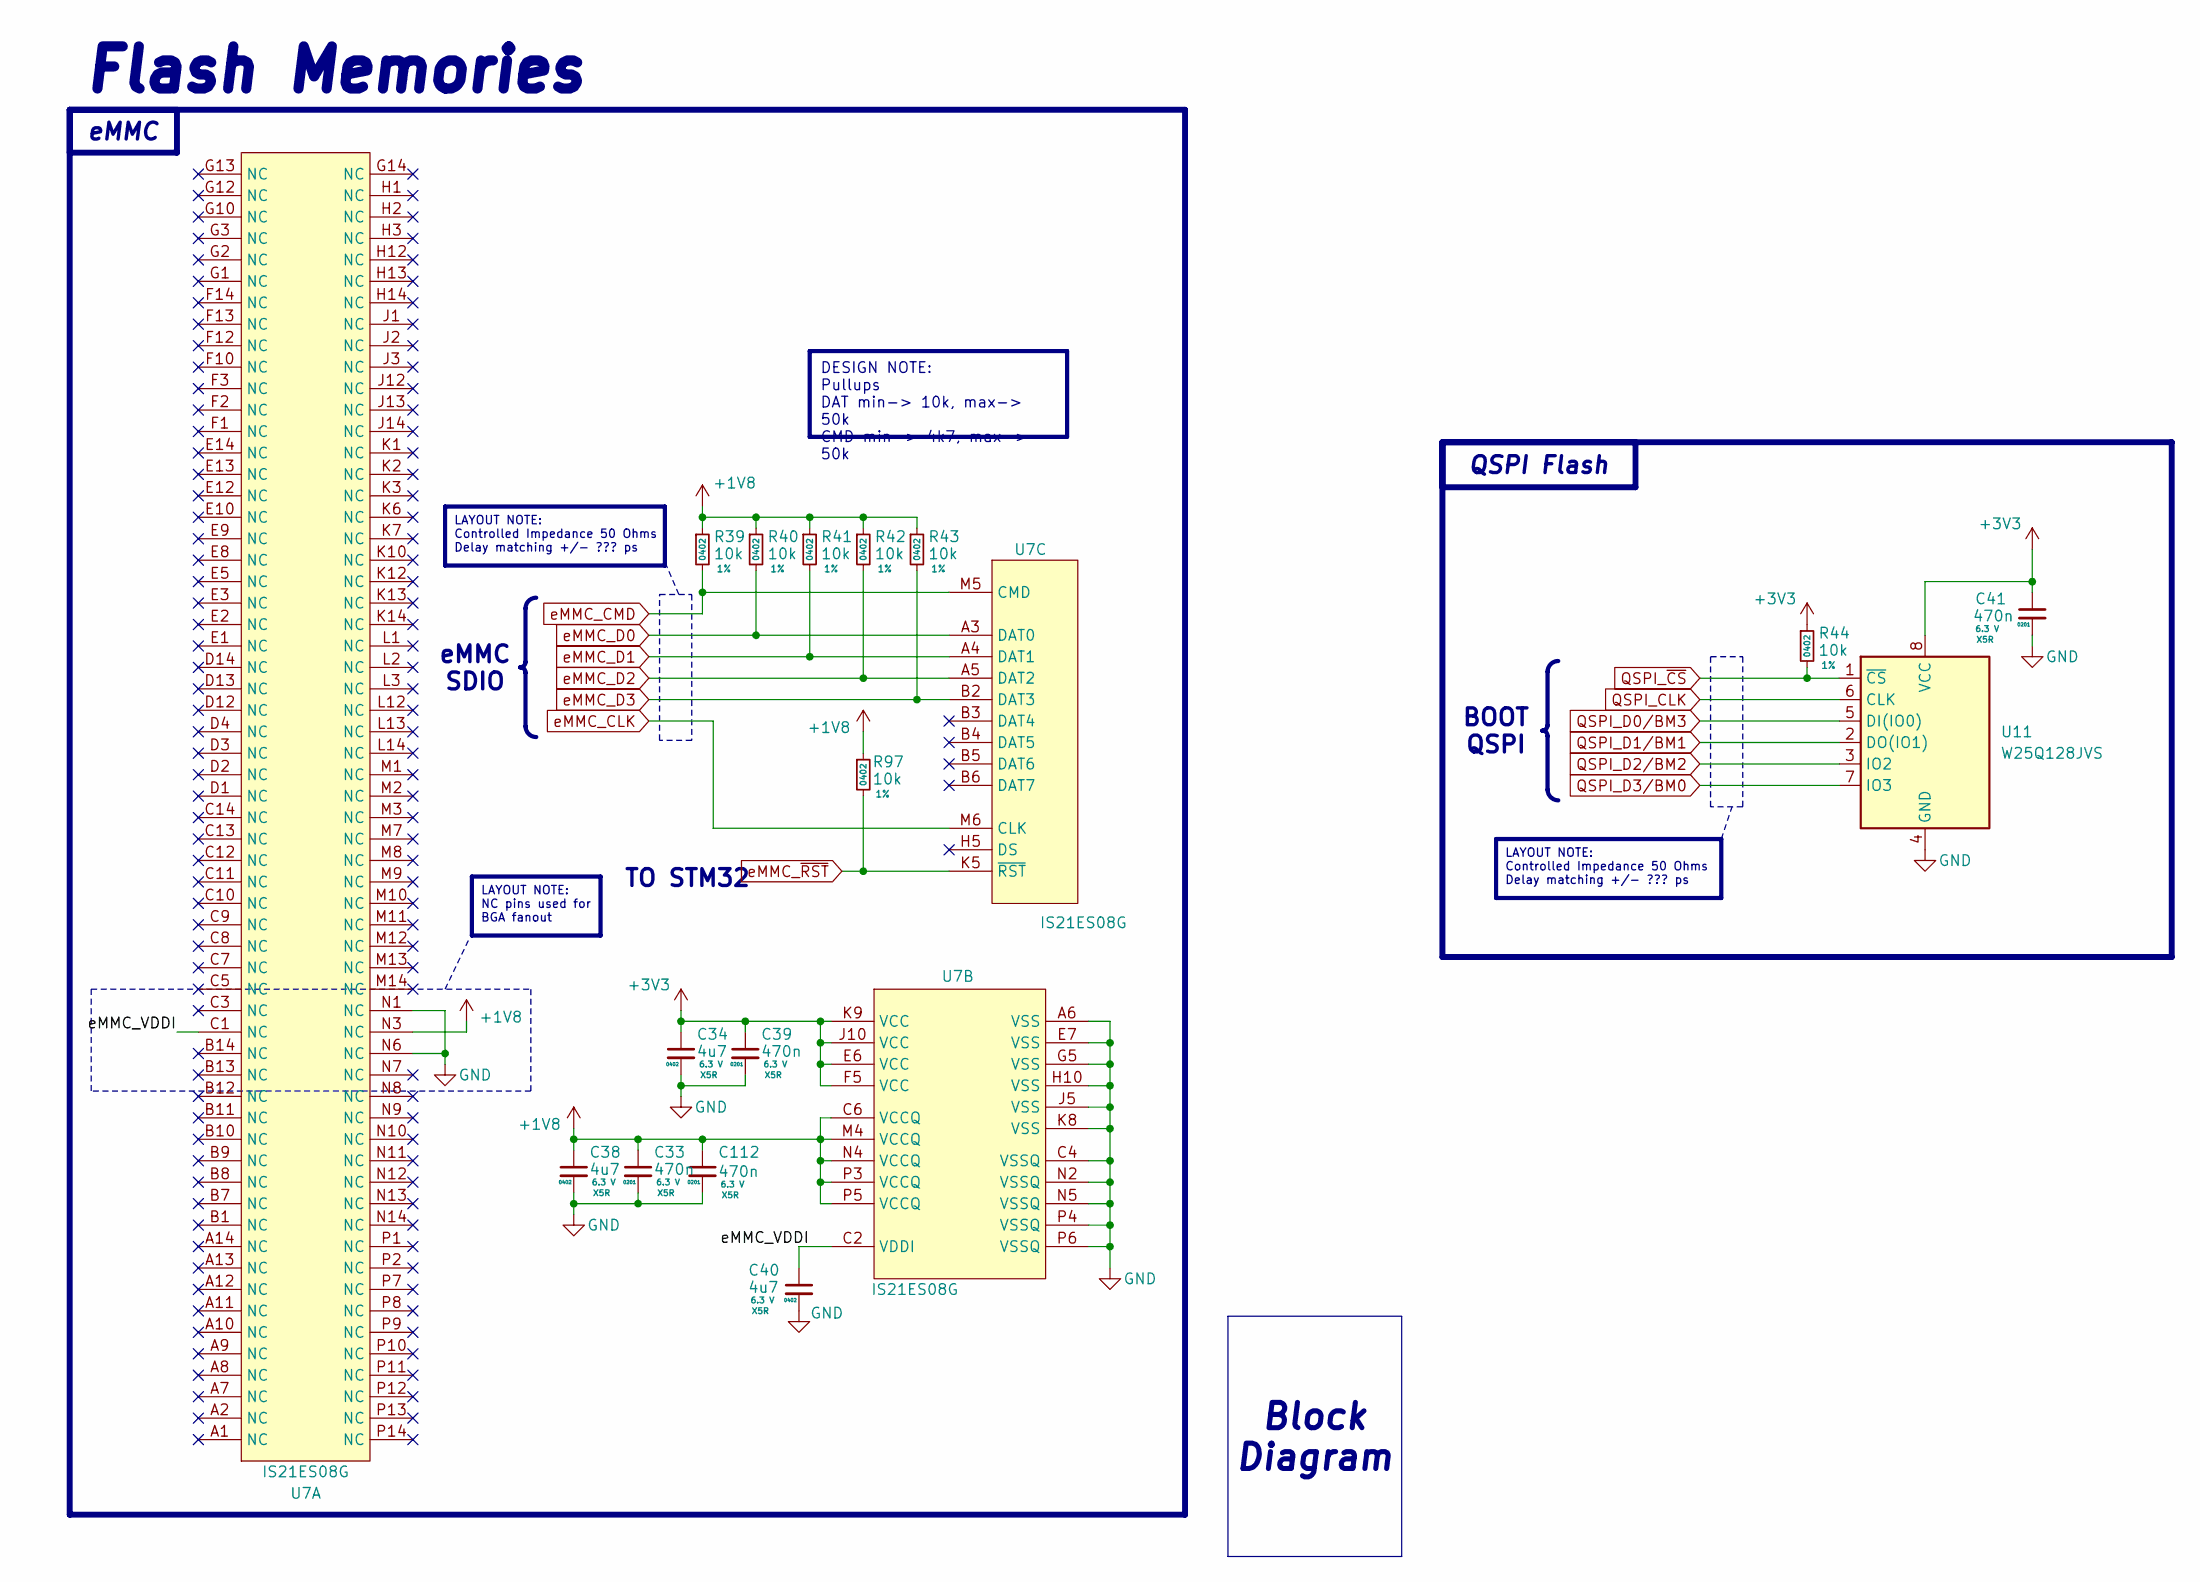
[picture p24: schematic emmc.kicad_sch]

Parts:
C33, C39, C41, C112: 470n; C_0201_0603Metric; Rating 6.3 V; LCSC Part C85926
C34, C38, C40: 4u7; C_0402_1005Metric; Rating 6.3 V; LCSC Part C368809
R39, R40, R41, R42, R43, R44, R97: 10k; R_0402_1005Metric; Tolerance 1%; LCSC Part C25744/gia
U7: IS21ES08G; BGA153N50P14X14_1150X1300X100; LCSC Part C499918
U11: W25Q128JVS; WSON-8-1EP_8x6mm_P1.27mm_EP3.4x4.3mm; LCSC Part C401662

Connections:
+1V8: C33.1, C38.1, C112.1, R39.1, R40.1, R41.1, R42.1, R43.1, R97.1, U7.C6 (VCCQ), U7.M4 (VCCQ), U7.N3 (NC), U7.N4 (VCCQ), U7.P3 (VCCQ), U7.P5 (VCCQ)
+3V3: C34.1, C39.1, C41.1, R44.1, U7.E6 (VCC), U7.F5 (VCC), U7.J10 (VCC), U7.K9 (VCC), U11.8 (VCC)
GND: C33.2, C34.2, C38.2, C39.2, C40.2, C41.2, C112.2, U7.A6 (VSS), U7.C4 (VSSQ), U7.E7 (VSS), U7.G5 (VSS), U7.H10 (VSS), U7.J5 (VSS), U7.K8 (VSS), U7.N1 (NC), U7.N2 (VSSQ), U7.N5 (VSSQ), U7.N6 (NC), U7.P4 (VSSQ), U7.P6 (VSSQ), U11.4 (GND), U11.9 (PAD)
QSPI_CLK: U11.6 (CLK)
QSPI_D0/BM3: U11.5 (DI(IO0))
QSPI_D1/BM1: U11.2 (DO(IO1))
QSPI_D2/BM2: U11.3 (IO2)
QSPI_D3/BM0: U11.7 (IO3)
QSPI_~CS: R44.2, U11.1 (~CS)
eMMC_CLK: U7.M6 (CLK)
eMMC_CMD: R39.2, U7.M5 (CMD)
eMMC_D0: R40.2, U7.A3 (DAT0)
eMMC_D1: R41.2, U7.A4 (DAT1)
eMMC_D2: R42.2, U7.A5 (DAT2)
eMMC_D3: R43.2, U7.B2 (DAT3)
eMMC_VDDI: C40.1, U7.C1 (NC), U7.C2 (VDDI)
eMMC_~RST: R97.2, U7.K5 (~RST)

Notes on the sheet:
TO STM32
Flash Memories
BOOT QSPI
eMMC SDIO
DESIGN NOTE: Pullups DAT min-> 10k, max-> 50k CMD min-> 4k7, max-> 50k
LAYOUT NOTE: NC pins used for BGA fanout
Block Diagram
QSPI Flash
LAYOUT NOTE: Controlled Impedance 50 Ohms Delay matching +/- ??? ps
eMMC
