mfkiwl/Zynq-SoM/schematic/system_controller.kicad_sch

## KiCad design schematic/system_controller.kicad_sch (2025-04-01)

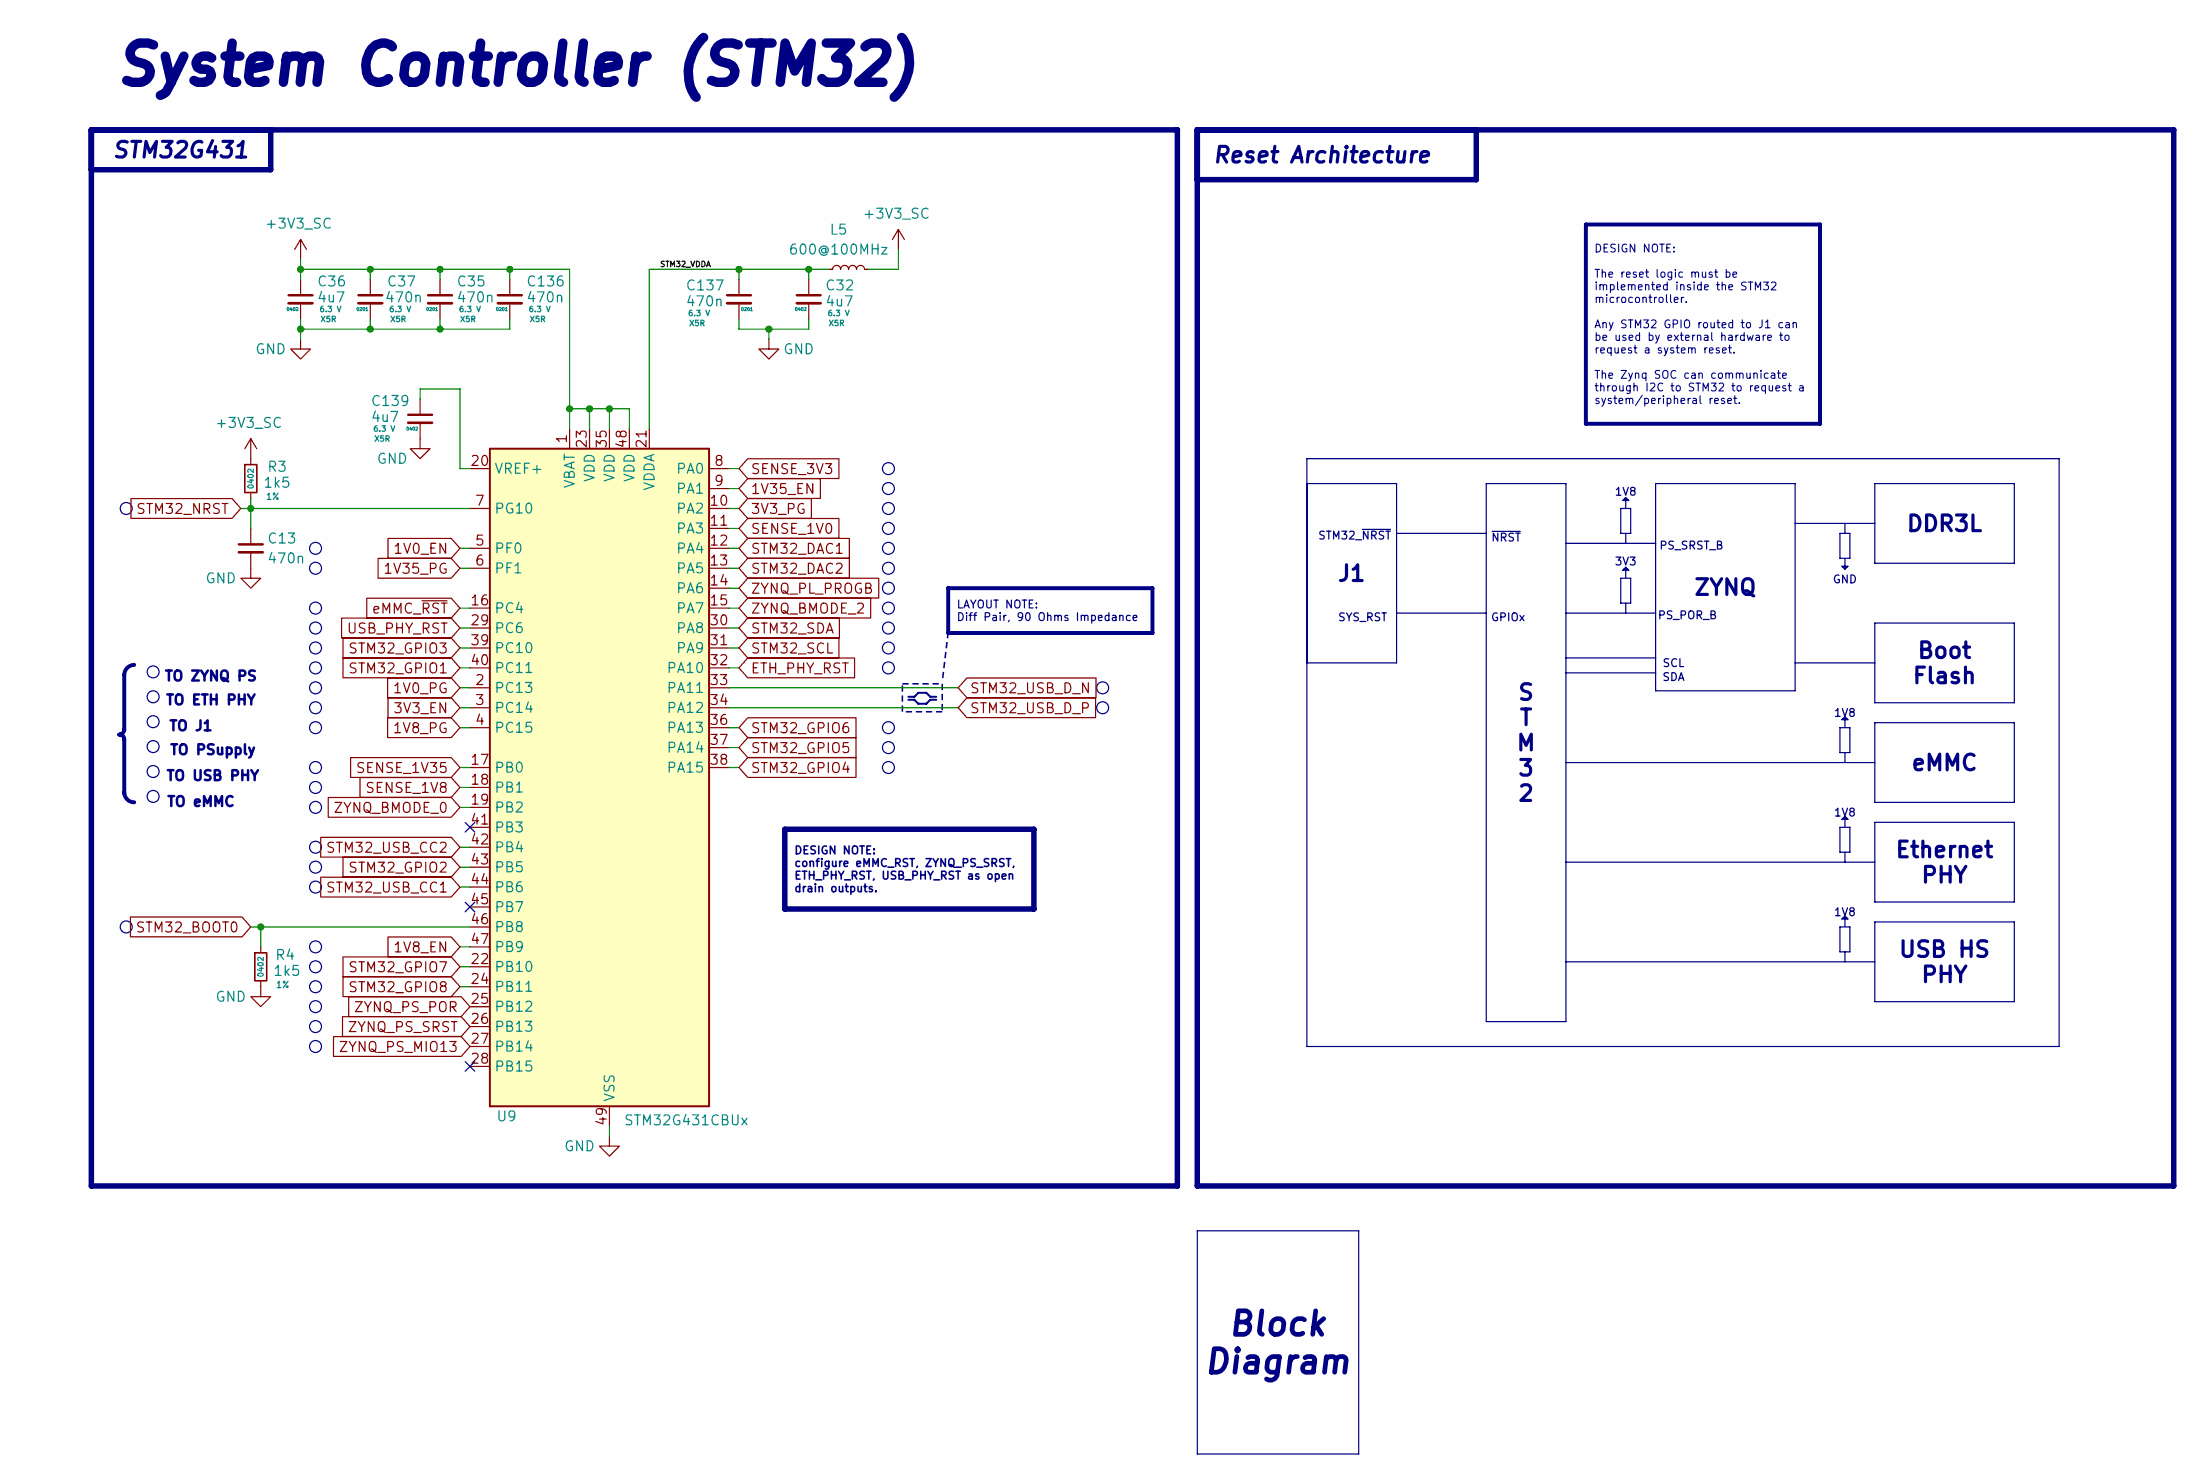
[picture p25: schematic system_controller.kicad_sch]

Parts:
C13: 470n; C_0201_0603Metric; LCSC Part C85926
C32, C36, C139: 4u7; C_0402_1005Metric; Rating 6.3 V; LCSC Part C368809
C35, C37, C136, C137: 470n; C_0201_0603Metric; Rating 6.3 V; LCSC Part C85926
L5: 600@100MHz; L_0402_1005Metric; LCSC Part C337875/gia
R3, R4: 1k5; R_0402_1005Metric; Tolerance 1%; LCSC Part C25867
U9: STM32G431CBUx; STM32G431CBU6; LCSC Part gia

Connections:
1V0_EN: U9.5 (PF0)
1V0_PG: U9.2 (PC13)
1V8_EN: U9.47 (PB9)
1V8_PG: U9.4 (PC15)
1V35_EN: U9.9 (PA1)
1V35_PG: U9.6 (PF1)
3V3_EN: U9.3 (PC14)
3V3_PG: U9.10 (PA2)
+3V3_SC: C35.1, C36.1, C37.1, C136.1, L5.1, R3.1, U9.1 (VBAT), U9.23 (VDD), U9.35 (VDD), U9.48 (VDD)
ETH_PHY_RST: U9.32 (PA10)
GND: C13.2, C32.2, C35.2, C36.2, C37.2, C136.2, C137.2, C139.2, R4.2, U9.49 (VSS)
unnamed: C139.1, U9.20 (VREF+)
SENSE_1V0: U9.11 (PA3)
SENSE_1V8: U9.18 (PB1)
SENSE_1V35: U9.17 (PB0)
SENSE_3V3: U9.8 (PA0)
STM32_BOOT0: R4.1, U9.46 (PB8)
STM32_DAC1: U9.12 (PA4)
STM32_DAC2: U9.13 (PA5)
STM32_GPIO1: U9.40 (PC11)
STM32_GPIO2: U9.43 (PB5)
STM32_GPIO3: U9.39 (PC10)
STM32_GPIO4: U9.38 (PA15)
STM32_GPIO5: U9.37 (PA14)
STM32_GPIO6: U9.36 (PA13)
STM32_GPIO7: U9.22 (PB10)
STM32_GPIO8: U9.24 (PB11)
STM32_NRST: C13.1, R3.2, U9.7 (PG10)
STM32_SCL: U9.31 (PA9)
STM32_SDA: U9.30 (PA8)
STM32_USB_CC1: U9.44 (PB6)
STM32_USB_CC2: U9.42 (PB4)
STM32_USB_D_N: U9.33 (PA11)
STM32_USB_D_P: U9.34 (PA12)
STM32_VDDA: C32.1, C137.1, L5.2, U9.21 (VDDA)
USB_PHY_RST: U9.29 (PC6)
ZYNQ_BMODE_0: U9.19 (PB2)
ZYNQ_BMODE_2: U9.15 (PA7)
ZYNQ_PL_PROGB: U9.14 (PA6)
ZYNQ_PS_MIO13: U9.27 (PB14)
ZYNQ_PS_POR: U9.25 (PB12)
ZYNQ_PS_SRST: U9.26 (PB13)
eMMC_~RST: U9.16 (PC4)

Notes on the sheet:
TO J1
TO USB PHY
TO ZYNQ PS
S T M 3 2
1V8
SDA
System Controller (STM32)
TO ETH PHY
3V3
GPIOx
SCL
PS_SRST_B
TO eMMC
SYS_RST
STM32_~{NRST}
PS_POR_B
GND
TO PSupply
~{NRST}
Boot Flash
LAYOUT NOTE: Diff Pair, 90 Ohms Impedance
Ethernet PHY
DDR3L
Block Diagram
USB HS PHY
eMMC
DESIGN NOTE: configure eMMC_RST, ZYNQ_PS_SRST, ETH_PHY_RST, USB_PHY_RST as open drain outputs.
ZYNQ
DESIGN NOTE: The reset logic must be implemented inside the STM32 microcontroller. Any STM32 GPIO routed to J1 can be used by external hardware to request a system reset. The Zynq SOC can communicate through I2C to STM32 to request a system/peripheral reset.
Reset Architecture
STM32G431
