mfkiwl/Zynq-SoM/schematic/usb_hs_phy.kicad_sch

## KiCad design schematic/usb_hs_phy.kicad_sch (2025-04-01)

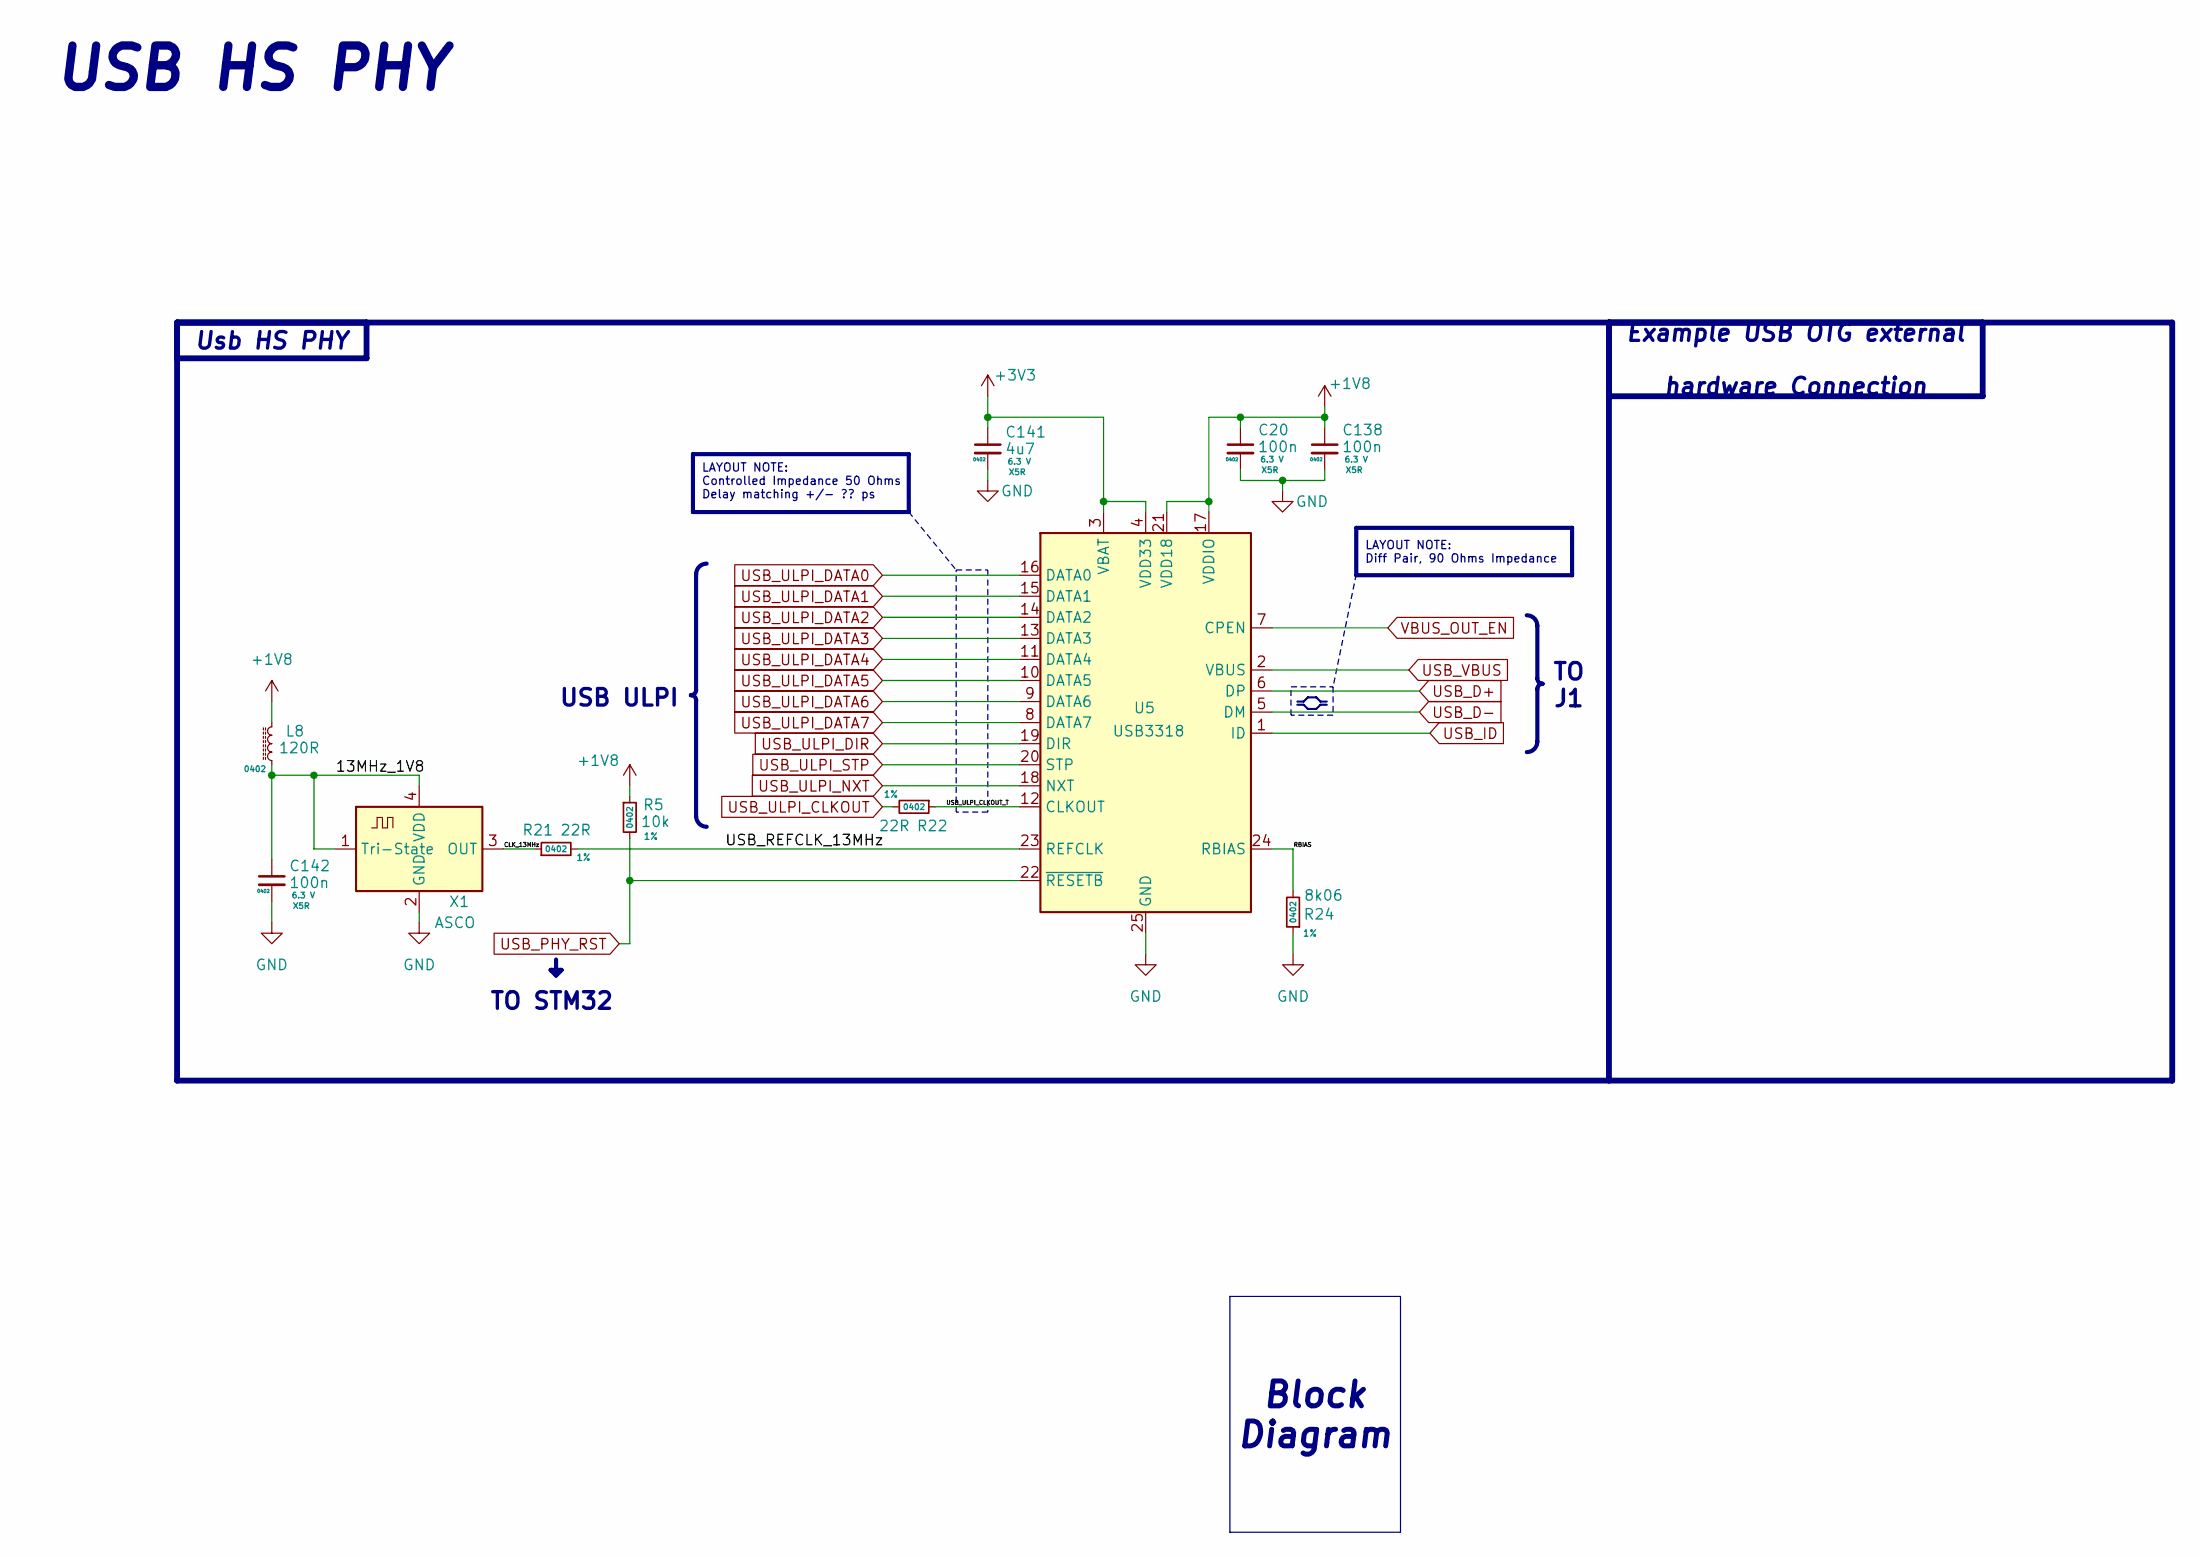
[picture p26: schematic usb_hs_phy.kicad_sch]

Parts:
C20, C138, C142: 100n; C_0402_1005Metric; Rating 6.3 V; LCSC Part gia
C141: 4u7; C_0402_1005Metric; Rating 6.3 V; LCSC Part C368809
L8: 120R; L_0402_1005Metric; LCSC Part C275478
R5: 10k; R_0402_1005Metric; Tolerance 1%; LCSC Part C25744/gia
R21, R22: 22R; R_0402_1005Metric; Tolerance 1%; LCSC Part C114765/C25105
R24: 8k06; R_0402_1005Metric; Tolerance 1%; LCSC Part C25923
U5: USB3318; QFN-24-1EP_4x4mm_P0.5mm_EP2.6x2.6mm; Digikey USB3318C-CP-TR
X1: ASCO; Oscillator_SMD_Kyocera_4PIN_2.0x1.6mm; Digikey KC2016Z13.0000C1KX00

Connections:
13MHz_1V8: C142.1, L8.1, X1.1 (Tri-State), X1.4 (VDD)
+1V8: C20.1, C138.1, L8.2, R5.1, U5.17 (VDDIO), U5.21 (VDD18)
+3V3: C141.1, U5.3 (VBAT), U5.4 (VDD33)
CLK_13MHz: R21.1, X1.3 (OUT)
GND: C20.2, C138.2, C141.2, C142.2, R24.1, U5.25 (GND), X1.2 (GND)
RBIAS: R24.2, U5.24 (RBIAS)
USB_D+: U5.6 (DP)
USB_D-: U5.5 (DM)
USB_ID: U5.1 (ID)
USB_PHY_RST: R5.2, U5.22 (~RESETB)
USB_REFCLK_13MHz: R21.2, U5.23 (REFCLK)
USB_ULPI_CLKOUT: R22.2
USB_ULPI_CLKOUT_T: R22.1, U5.12 (CLKOUT)
USB_ULPI_DATA0: U5.16 (DATA0)
USB_ULPI_DATA1: U5.15 (DATA1)
USB_ULPI_DATA2: U5.14 (DATA2)
USB_ULPI_DATA3: U5.13 (DATA3)
USB_ULPI_DATA4: U5.11 (DATA4)
USB_ULPI_DATA5: U5.10 (DATA5)
USB_ULPI_DATA6: U5.9 (DATA6)
USB_ULPI_DATA7: U5.8 (DATA7)
USB_ULPI_DIR: U5.19 (DIR)
USB_ULPI_NXT: U5.18 (NXT)
USB_ULPI_STP: U5.20 (STP)
USB_VBUS: U5.2 (VBUS)
VBUS_OUT_EN: U5.7 (CPEN)

Notes on the sheet:
TO STM32
USB HS PHY
TO J1
USB ULPI
Usb HS PHY
LAYOUT NOTE: Diff Pair, 90 Ohms Impedance
Example USB OTG external hardware Connection
LAYOUT NOTE: Controlled Impedance 50 Ohms Delay matching +/- ?? ps
Block Diagram
