mfkiwl/Zynq-SoM/schematic/zynq_PL_b13.kicad_sch

## KiCad design schematic/zynq_PL_b13.kicad_sch (2025-04-01)

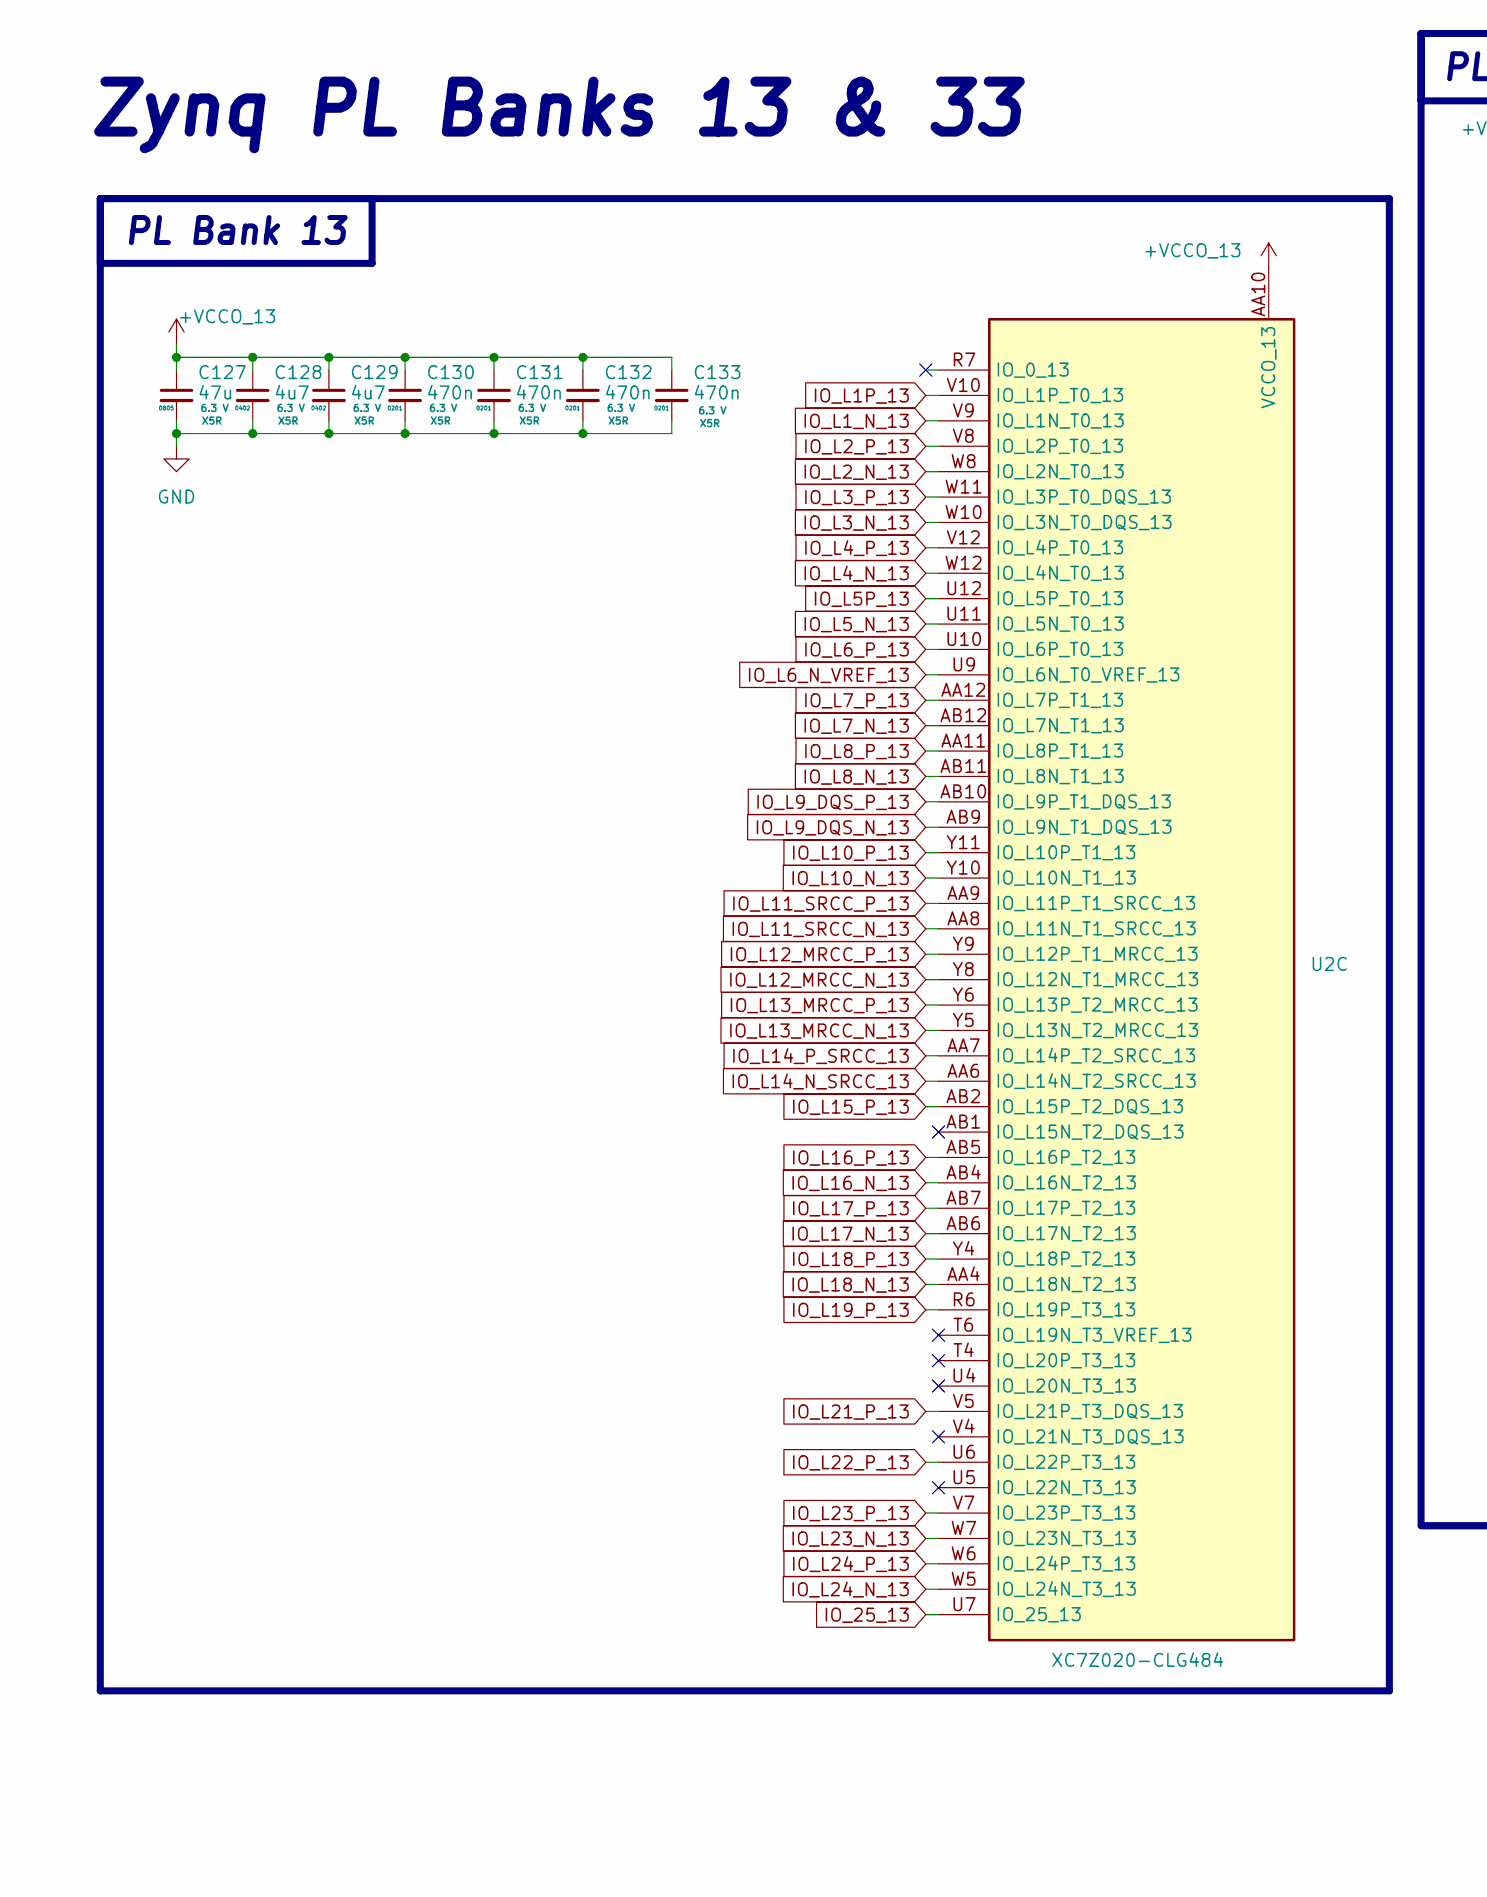
[picture p27: schematic zynq_PL_b13.kicad_sch, part in row 1, column 1]

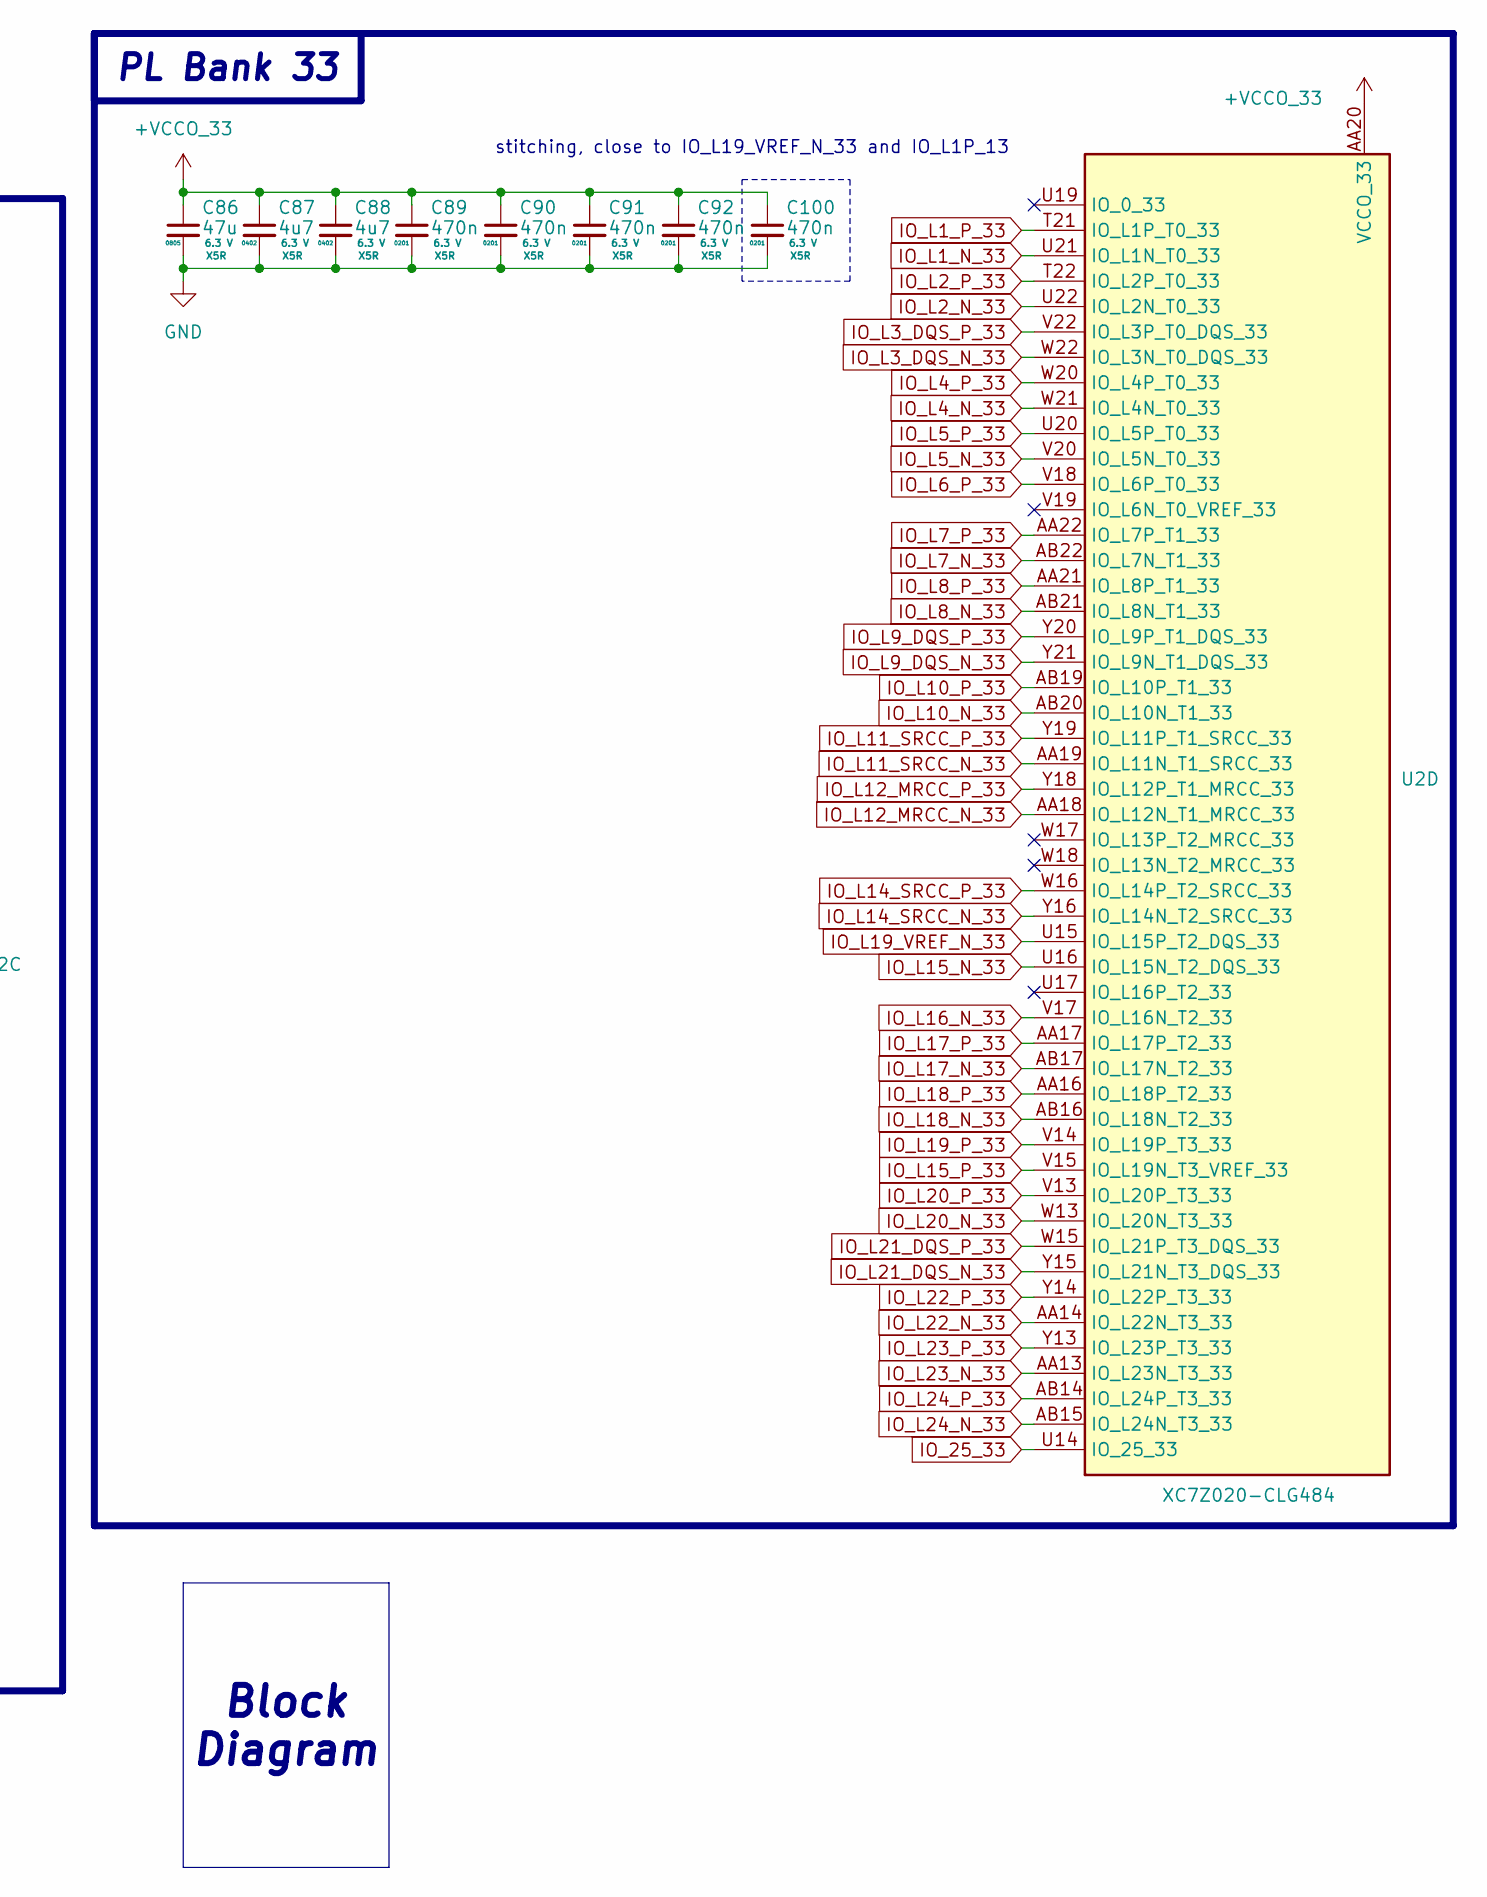
[picture p28: schematic zynq_PL_b13.kicad_sch, part in row 1, column 2]

Parts:
C86, C127: 47u; C_0805_2012Metric; Rating 6.3 V; LCSC Part C16780
C87, C88, C128, C129: 4u7; C_0402_1005Metric; Rating 6.3 V; LCSC Part C368809
C89, C90, C91, C92, C100, C130, C131, C132, C133: 470n; C_0201_0603Metric; Rating 6.3 V; LCSC Part C85926
U2: XC7Z020-CLG484; CLG484_XIL-L_new; LCSC Part gia

Connections:
+VCCO_13: C127.1, C128.1, C129.1, C130.1, C131.1, C132.1, C133.1, U2.AA10 (VCCO_13), U2.AB3 (VCCO_13), U2.T5 (VCCO_13), U2.U8 (VCCO_13), U2.V11 (VCCO_13), U2.W4 (VCCO_13), U2.Y7 (VCCO_13)
+VCCO_33: C86.1, C87.1, C88.1, C89.1, C90.1, C91.1, C92.1, C100.1, U2.AA20 (VCCO_33), U2.AB13 (VCCO_33), U2.U18 (VCCO_33), U2.V21 (VCCO_33), U2.W14 (VCCO_33), U2.Y17 (VCCO_33)
GND: C86.2, C87.2, C88.2, C89.2, C90.2, C91.2, C92.2, C100.2, C127.2, C128.2, C129.2, C130.2, C131.2, C132.2, C133.2
IO_25_13: U2.U7 (IO_25_13)
IO_25_33: U2.U14 (IO_25_33)
IO_L1P_13: U2.V10 (IO_L1P_T0_13)
IO_L1_N_13: U2.V9 (IO_L1N_T0_13)
IO_L1_N_33: U2.U21 (IO_L1N_T0_33)
IO_L1_P_33: U2.T21 (IO_L1P_T0_33)
IO_L2_N_13: U2.W8 (IO_L2N_T0_13)
IO_L2_N_33: U2.U22 (IO_L2N_T0_33)
IO_L2_P_13: U2.V8 (IO_L2P_T0_13)
IO_L2_P_33: U2.T22 (IO_L2P_T0_33)
IO_L3_DQS_N_33: U2.W22 (IO_L3N_T0_DQS_33)
IO_L3_DQS_P_33: U2.V22 (IO_L3P_T0_DQS_33)
IO_L3_N_13: U2.W10 (IO_L3N_T0_DQS_13)
IO_L3_P_13: U2.W11 (IO_L3P_T0_DQS_13)
IO_L4_N_13: U2.W12 (IO_L4N_T0_13)
IO_L4_N_33: U2.W21 (IO_L4N_T0_33)
IO_L4_P_13: U2.V12 (IO_L4P_T0_13)
IO_L4_P_33: U2.W20 (IO_L4P_T0_33)
IO_L5P_13: U2.U12 (IO_L5P_T0_13)
IO_L5_N_13: U2.U11 (IO_L5N_T0_13)
IO_L5_N_33: U2.V20 (IO_L5N_T0_33)
IO_L5_P_33: U2.U20 (IO_L5P_T0_33)
IO_L6_N_VREF_13: U2.U9 (IO_L6N_T0_VREF_13)
IO_L6_P_13: U2.U10 (IO_L6P_T0_13)
IO_L6_P_33: U2.V18 (IO_L6P_T0_33)
IO_L7_N_13: U2.AB12 (IO_L7N_T1_13)
IO_L7_N_33: U2.AB22 (IO_L7N_T1_33)
IO_L7_P_13: U2.AA12 (IO_L7P_T1_13)
IO_L7_P_33: U2.AA22 (IO_L7P_T1_33)
IO_L8_N_13: U2.AB11 (IO_L8N_T1_13)
IO_L8_N_33: U2.AB21 (IO_L8N_T1_33)
IO_L8_P_13: U2.AA11 (IO_L8P_T1_13)
IO_L8_P_33: U2.AA21 (IO_L8P_T1_33)
IO_L9_DQS_N_13: U2.AB9 (IO_L9N_T1_DQS_13)
IO_L9_DQS_N_33: U2.Y21 (IO_L9N_T1_DQS_33)
IO_L9_DQS_P_13: U2.AB10 (IO_L9P_T1_DQS_13)
IO_L9_DQS_P_33: U2.Y20 (IO_L9P_T1_DQS_33)
IO_L10_N_13: U2.Y10 (IO_L10N_T1_13)
IO_L10_N_33: U2.AB20 (IO_L10N_T1_33)
IO_L10_P_13: U2.Y11 (IO_L10P_T1_13)
IO_L10_P_33: U2.AB19 (IO_L10P_T1_33)
IO_L11_SRCC_N_13: U2.AA8 (IO_L11N_T1_SRCC_13)
IO_L11_SRCC_N_33: U2.AA19 (IO_L11N_T1_SRCC_33)
IO_L11_SRCC_P_13: U2.AA9 (IO_L11P_T1_SRCC_13)
IO_L11_SRCC_P_33: U2.Y19 (IO_L11P_T1_SRCC_33)
IO_L12_MRCC_N_13: U2.Y8 (IO_L12N_T1_MRCC_13)
IO_L12_MRCC_N_33: U2.AA18 (IO_L12N_T1_MRCC_33)
IO_L12_MRCC_P_13: U2.Y9 (IO_L12P_T1_MRCC_13)
IO_L12_MRCC_P_33: U2.Y18 (IO_L12P_T1_MRCC_33)
IO_L13_MRCC_N_13: U2.Y5 (IO_L13N_T2_MRCC_13)
IO_L13_MRCC_P_13: U2.Y6 (IO_L13P_T2_MRCC_13)
IO_L14_N_SRCC_13: U2.AA6 (IO_L14N_T2_SRCC_13)
IO_L14_P_SRCC_13: U2.AA7 (IO_L14P_T2_SRCC_13)
IO_L14_SRCC_N_33: U2.Y16 (IO_L14N_T2_SRCC_33)
IO_L14_SRCC_P_33: U2.W16 (IO_L14P_T2_SRCC_33)
IO_L15_N_33: U2.U16 (IO_L15N_T2_DQS_33)
IO_L15_P_13: U2.AB2 (IO_L15P_T2_DQS_13)
IO_L15_P_33: U2.V15 (IO_L19N_T3_VREF_33)
IO_L16_N_13: U2.AB4 (IO_L16N_T2_13)
IO_L16_N_33: U2.V17 (IO_L16N_T2_33)
IO_L16_P_13: U2.AB5 (IO_L16P_T2_13)
IO_L17_N_13: U2.AB6 (IO_L17N_T2_13)
IO_L17_N_33: U2.AB17 (IO_L17N_T2_33)
IO_L17_P_13: U2.AB7 (IO_L17P_T2_13)
IO_L17_P_33: U2.AA17 (IO_L17P_T2_33)
IO_L18_N_13: U2.AA4 (IO_L18N_T2_13)
IO_L18_N_33: U2.AB16 (IO_L18N_T2_33)
IO_L18_P_13: U2.Y4 (IO_L18P_T2_13)
IO_L18_P_33: U2.AA16 (IO_L18P_T2_33)
IO_L19_P_13: U2.R6 (IO_L19P_T3_13)
IO_L19_P_33: U2.V14 (IO_L19P_T3_33)
IO_L19_VREF_N_33: U2.U15 (IO_L15P_T2_DQS_33)
IO_L20_N_33: U2.W13 (IO_L20N_T3_33)
IO_L20_P_33: U2.V13 (IO_L20P_T3_33)
IO_L21_DQS_N_33: U2.Y15 (IO_L21N_T3_DQS_33)
IO_L21_DQS_P_33: U2.W15 (IO_L21P_T3_DQS_33)
IO_L21_P_13: U2.V5 (IO_L21P_T3_DQS_13)
IO_L22_N_33: U2.AA14 (IO_L22N_T3_33)
IO_L22_P_13: U2.U6 (IO_L22P_T3_13)
IO_L22_P_33: U2.Y14 (IO_L22P_T3_33)
IO_L23_N_13: U2.W7 (IO_L23N_T3_13)
IO_L23_N_33: U2.AA13 (IO_L23N_T3_33)
IO_L23_P_13: U2.V7 (IO_L23P_T3_13)
IO_L23_P_33: U2.Y13 (IO_L23P_T3_33)
IO_L24_N_13: U2.W5 (IO_L24N_T3_13)
IO_L24_N_33: U2.AB15 (IO_L24N_T3_33)
IO_L24_P_13: U2.W6 (IO_L24P_T3_13)
IO_L24_P_33: U2.AB14 (IO_L24P_T3_33)

Notes on the sheet:
Zynq PL Banks 13 & 33
stitching, close to IO_L19_VREF_N_33 and IO_L1P_13
PL Bank 33
Block Diagram
PL Bank 13
