mfkiwl/Zynq-SoM/schematic/zynq_PS_b500_b501.kicad_sch

## KiCad design schematic/zynq_PS_b500_b501.kicad_sch (2025-04-01)

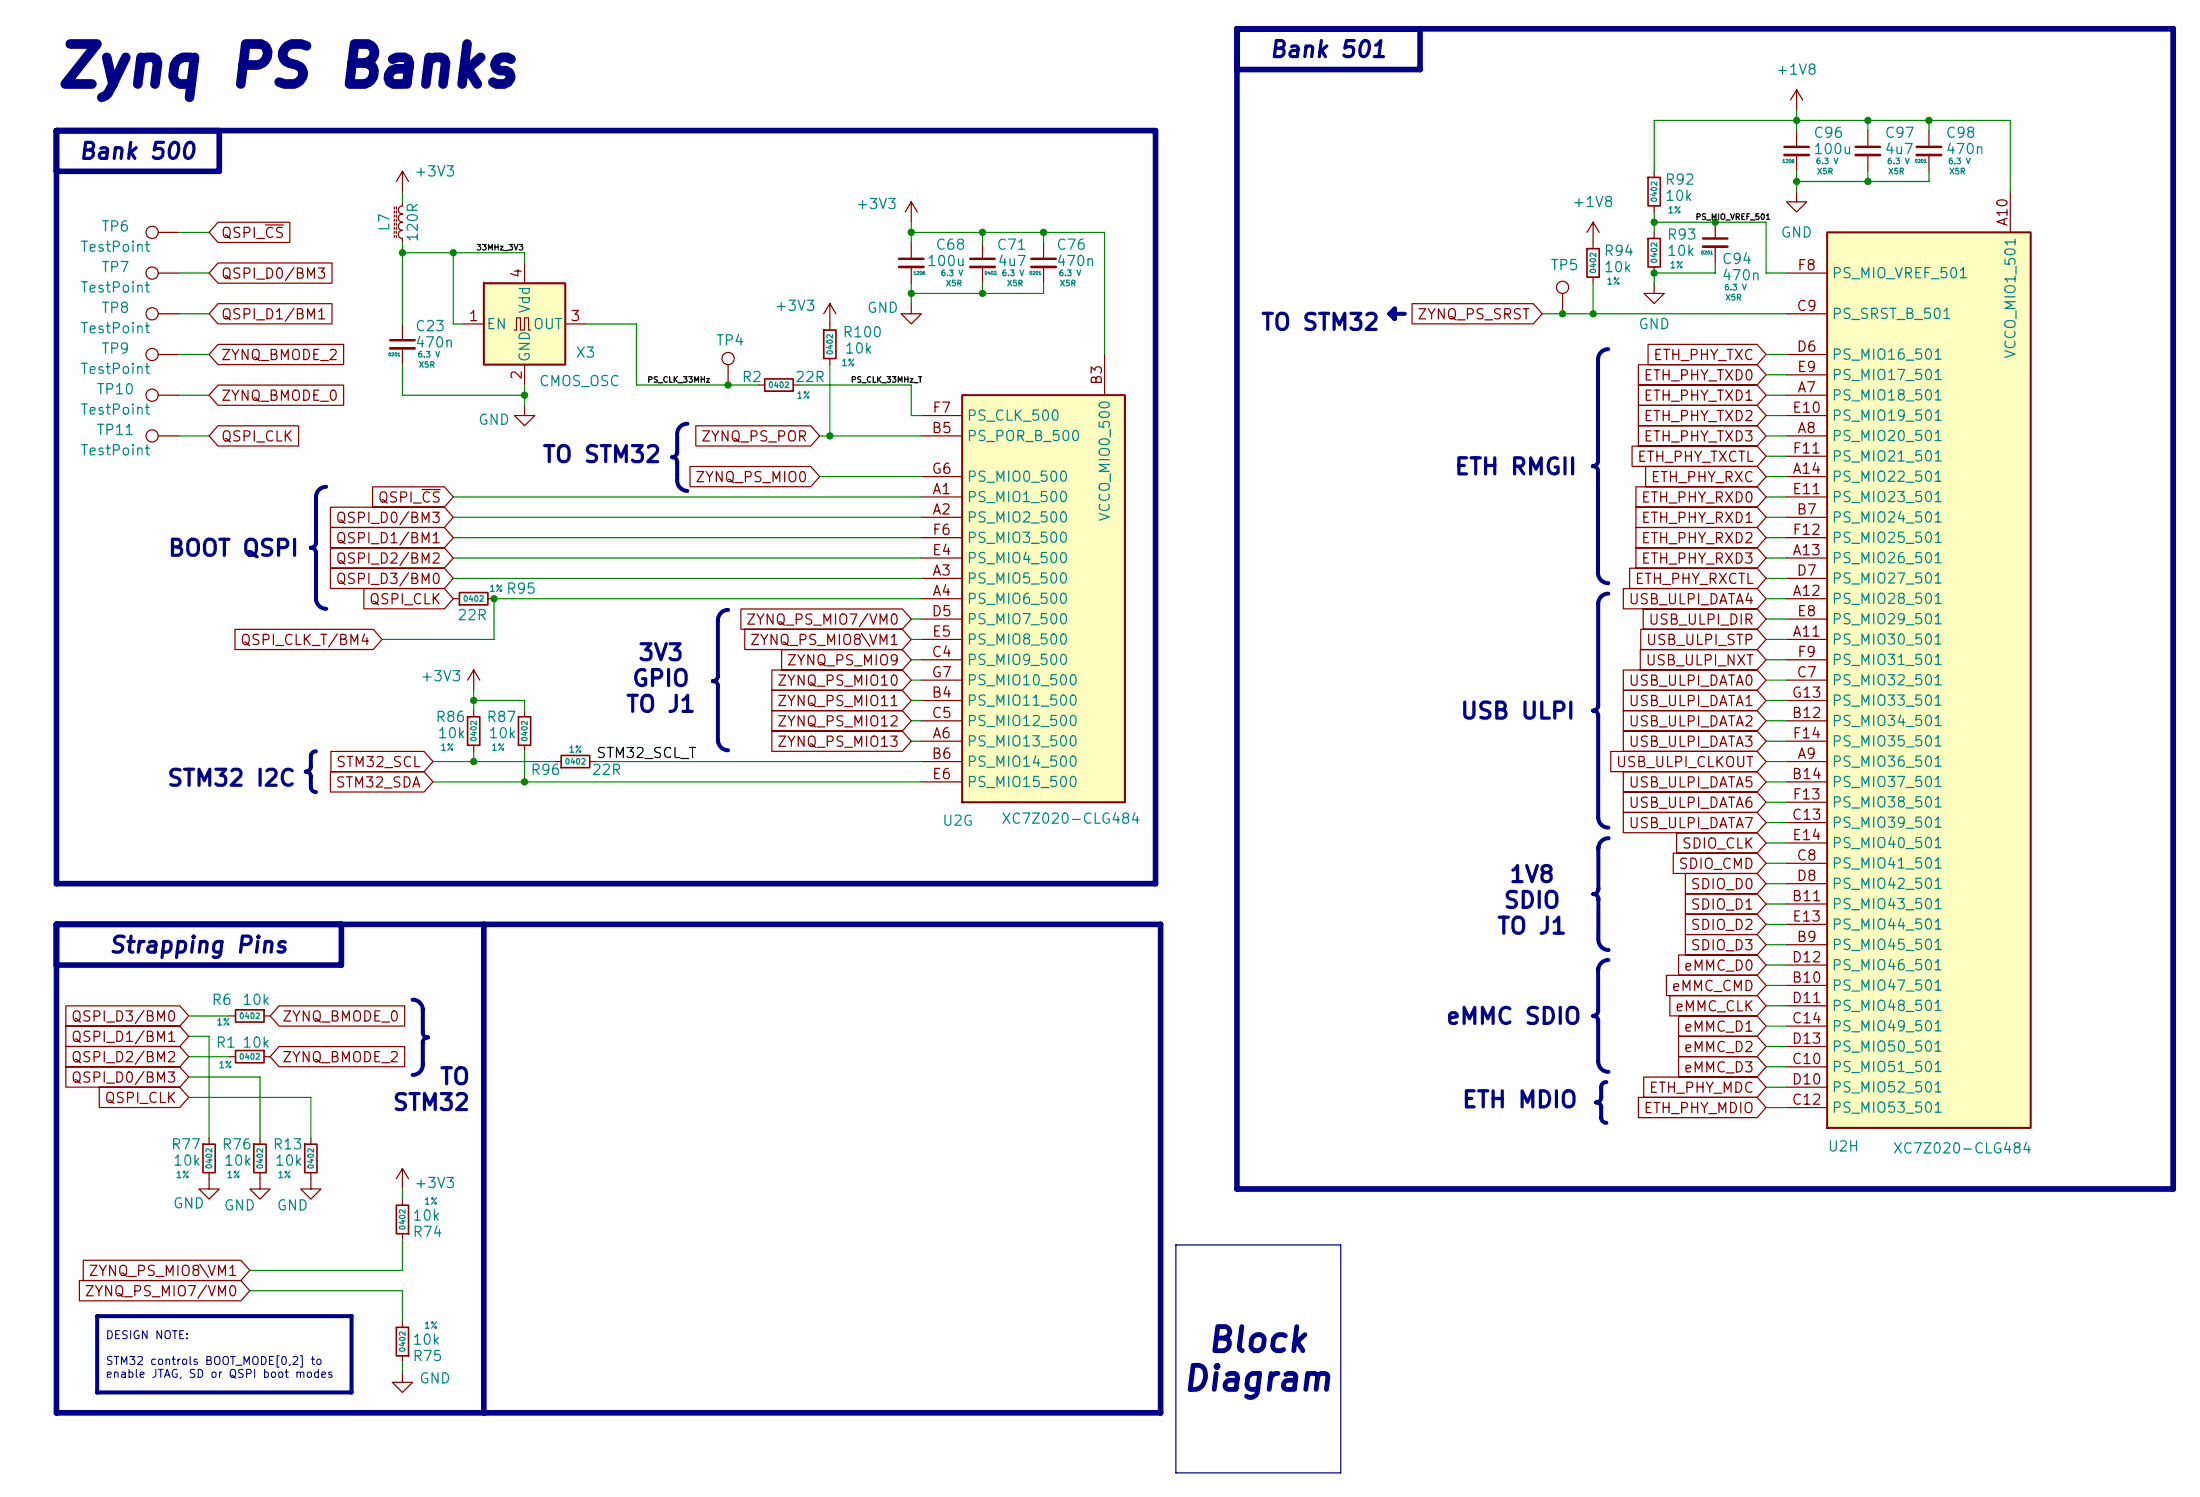
[picture p29: schematic zynq_PS_b500_b501.kicad_sch]

Parts:
C23, C76, C94, C98: 470n; C_0201_0603Metric; Rating 6.3 V; LCSC Part C85926
C68, C96: 100u; C_1206_3216Metric; Rating 6.3 V; LCSC Part C15008
C71, C97: 4u7; C_0402_1005Metric; Rating 6.3 V; LCSC Part C368809
L7: 120R; L_0402_1005Metric; LCSC Part C275478
R1, R6, R13, R74, R75, R76, R77, R86, R87, R92, R93, R94, R100: 10k; R_0402_1005Metric; Tolerance 1%; LCSC Part C25744/gia
R2, R95, R96: 22R; R_0402_1005Metric; Tolerance 1%; LCSC Part C114765/C25105
TP4, TP5, TP6, TP7, TP8, TP9, TP10, TP11: TestPoint; TestPoint_Pad_D0.7mm
U2: XC7Z020-CLG484; CLG484_XIL-L_new; LCSC Part gia
X3: CMOS_OSC; Oscillator_SMD_Kyocera_4PIN_2.0x1.6mm; Digikey KC2016Z33.0000C1KX00

Connections:
33MHz_3V3: C23.1, L7.1, X3.1 (EN), X3.4 (Vdd)
+1V8: C96.1, C97.1, C98.1, R92.1, R94.1, U2.A10 (VCCO_MIO1_501), U2.B13 (VCCO_MIO1_501), U2.D9 (VCCO_MIO1_501), U2.E12 (VCCO_MIO1_501)
+3V3: C68.1, C71.1, C76.1, L7.2, R74.2, R86.1, R87.1, R100.1, U2.B3 (VCCO_MIO0_500), U2.C6 (VCCO_MIO0_500)
ETH_PHY_MDC: U2.D10 (PS_MIO52_501)
ETH_PHY_MDIO: U2.C12 (PS_MIO53_501)
ETH_PHY_RXC: U2.A14 (PS_MIO22_501)
ETH_PHY_RXCTL: U2.D7 (PS_MIO27_501)
ETH_PHY_RXD0: U2.E11 (PS_MIO23_501)
ETH_PHY_RXD1: U2.B7 (PS_MIO24_501)
ETH_PHY_RXD2: U2.F12 (PS_MIO25_501)
ETH_PHY_RXD3: U2.A13 (PS_MIO26_501)
ETH_PHY_TXC: U2.D6 (PS_MIO16_501)
ETH_PHY_TXCTL: U2.F11 (PS_MIO21_501)
ETH_PHY_TXD0: U2.E9 (PS_MIO17_501)
ETH_PHY_TXD1: U2.A7 (PS_MIO18_501)
ETH_PHY_TXD2: U2.E10 (PS_MIO19_501)
ETH_PHY_TXD3: U2.A8 (PS_MIO20_501)
GND: C23.2, C68.2, C71.2, C76.2, C94.2, C96.2, C97.2, C98.2, R13.2, R75.1, R76.2, R77.2, R93.2, X3.2 (GND)
PS_CLK_33MHz: R2.1, TP4.1, X3.3 (OUT)
PS_CLK_33MHz_T: R2.2, U2.F7 (PS_CLK_500)
PS_MIO_VREF_501: C94.1, R92.2, R93.1, U2.F8 (PS_MIO_VREF_501)
QSPI_CLK: R13.1, R95.1, TP11.1
QSPI_CLK_T/BM4: R95.2, U2.A4 (PS_MIO6_500)
QSPI_D0/BM3: R76.1, TP7.1, U2.A2 (PS_MIO2_500)
QSPI_D1/BM1: R77.1, TP8.1, U2.F6 (PS_MIO3_500)
QSPI_D2/BM2: R1.2, U2.E4 (PS_MIO4_500)
QSPI_D3/BM0: R6.2, U2.A3 (PS_MIO5_500)
QSPI_~CS: TP6.1, U2.A1 (PS_MIO1_500)
SDIO_CLK: U2.E14 (PS_MIO40_501)
SDIO_CMD: U2.C8 (PS_MIO41_501)
SDIO_D0: U2.D8 (PS_MIO42_501)
SDIO_D1: U2.B11 (PS_MIO43_501)
SDIO_D2: U2.E13 (PS_MIO44_501)
SDIO_D3: U2.B9 (PS_MIO45_501)
STM32_SCL: R86.2, R96.1
STM32_SCL_T: R96.2, U2.B6 (PS_MIO14_500)
STM32_SDA: R87.2, U2.E6 (PS_MIO15_500)
USB_ULPI_CLKOUT: U2.A9 (PS_MIO36_501)
USB_ULPI_DATA0: U2.C7 (PS_MIO32_501)
USB_ULPI_DATA1: U2.G13 (PS_MIO33_501)
USB_ULPI_DATA2: U2.B12 (PS_MIO34_501)
USB_ULPI_DATA3: U2.F14 (PS_MIO35_501)
USB_ULPI_DATA4: U2.A12 (PS_MIO28_501)
USB_ULPI_DATA5: U2.B14 (PS_MIO37_501)
USB_ULPI_DATA6: U2.F13 (PS_MIO38_501)
USB_ULPI_DATA7: U2.C13 (PS_MIO39_501)
USB_ULPI_DIR: U2.E8 (PS_MIO29_501)
USB_ULPI_NXT: U2.F9 (PS_MIO31_501)
USB_ULPI_STP: U2.A11 (PS_MIO30_501)
ZYNQ_BMODE_0: R6.1, TP10.1
ZYNQ_BMODE_2: R1.1, TP9.1
ZYNQ_PS_MIO0: U2.G6 (PS_MIO0_500)
ZYNQ_PS_MIO7/VM0: R75.2, U2.D5 (PS_MIO7_500)
ZYNQ_PS_MIO8\VM1: R74.1, U2.E5 (PS_MIO8_500)
ZYNQ_PS_MIO9: U2.C4 (PS_MIO9_500)
ZYNQ_PS_MIO10: U2.G7 (PS_MIO10_500)
ZYNQ_PS_MIO11: U2.B4 (PS_MIO11_500)
ZYNQ_PS_MIO12: U2.C5 (PS_MIO12_500)
ZYNQ_PS_MIO13: U2.A6 (PS_MIO13_500)
ZYNQ_PS_POR: R100.2, U2.B5 (PS_POR_B_500)
ZYNQ_PS_SRST: R94.2, TP5.1, U2.C9 (PS_SRST_B_501)
eMMC_CLK: U2.D11 (PS_MIO48_501)
eMMC_CMD: U2.B10 (PS_MIO47_501)
eMMC_D0: U2.D12 (PS_MIO46_501)
eMMC_D1: U2.C14 (PS_MIO49_501)
eMMC_D2: U2.D13 (PS_MIO50_501)
eMMC_D3: U2.C10 (PS_MIO51_501)

Notes on the sheet:
BOOT QSPI
ETH RMGII
eMMC SDIO
3V3 GPIO TO J1
Zynq PS Banks
TO STM32
1V8 SDIO TO J1
STM32 I2C
TO STM32
ETH MDIO
USB ULPI
DESIGN NOTE: STM32 controls BOOT_MODE[0,2] to enable JTAG, SD or QSPI boot modes
Bank 500
Strapping Pins
Bank 501
Block Diagram
