mfkiwl/Zynq-SoM/schematic/zynq_b33_b34_b35.kicad_sch

## KiCad design schematic/zynq_b33_b34_b35.kicad_sch (2025-04-01)

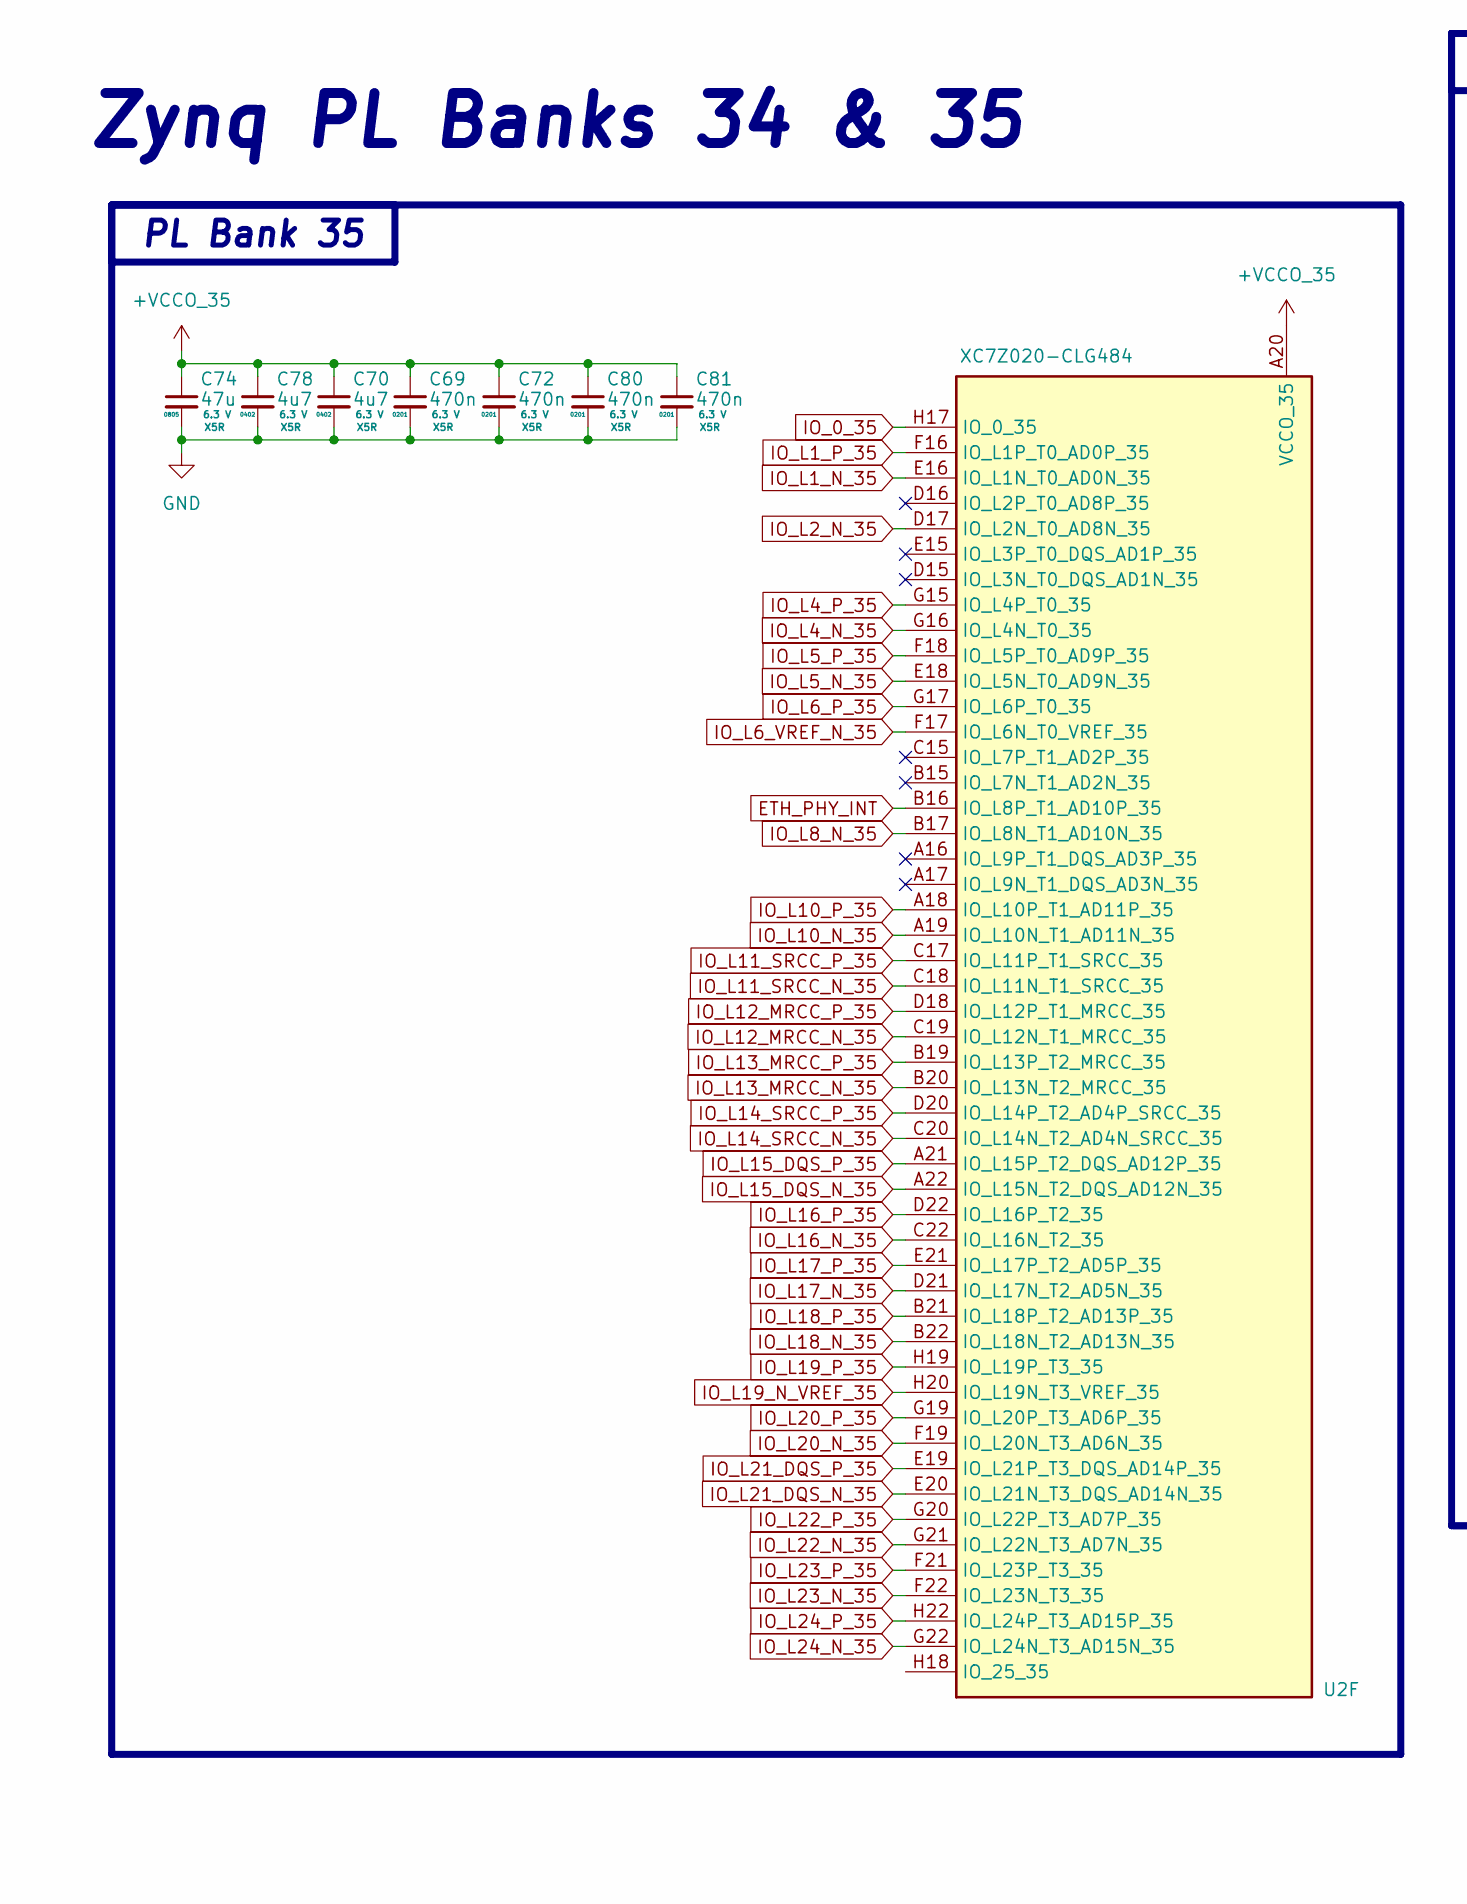
[picture p30: schematic zynq_b33_b34_b35.kicad_sch, part in row 1, column 1]

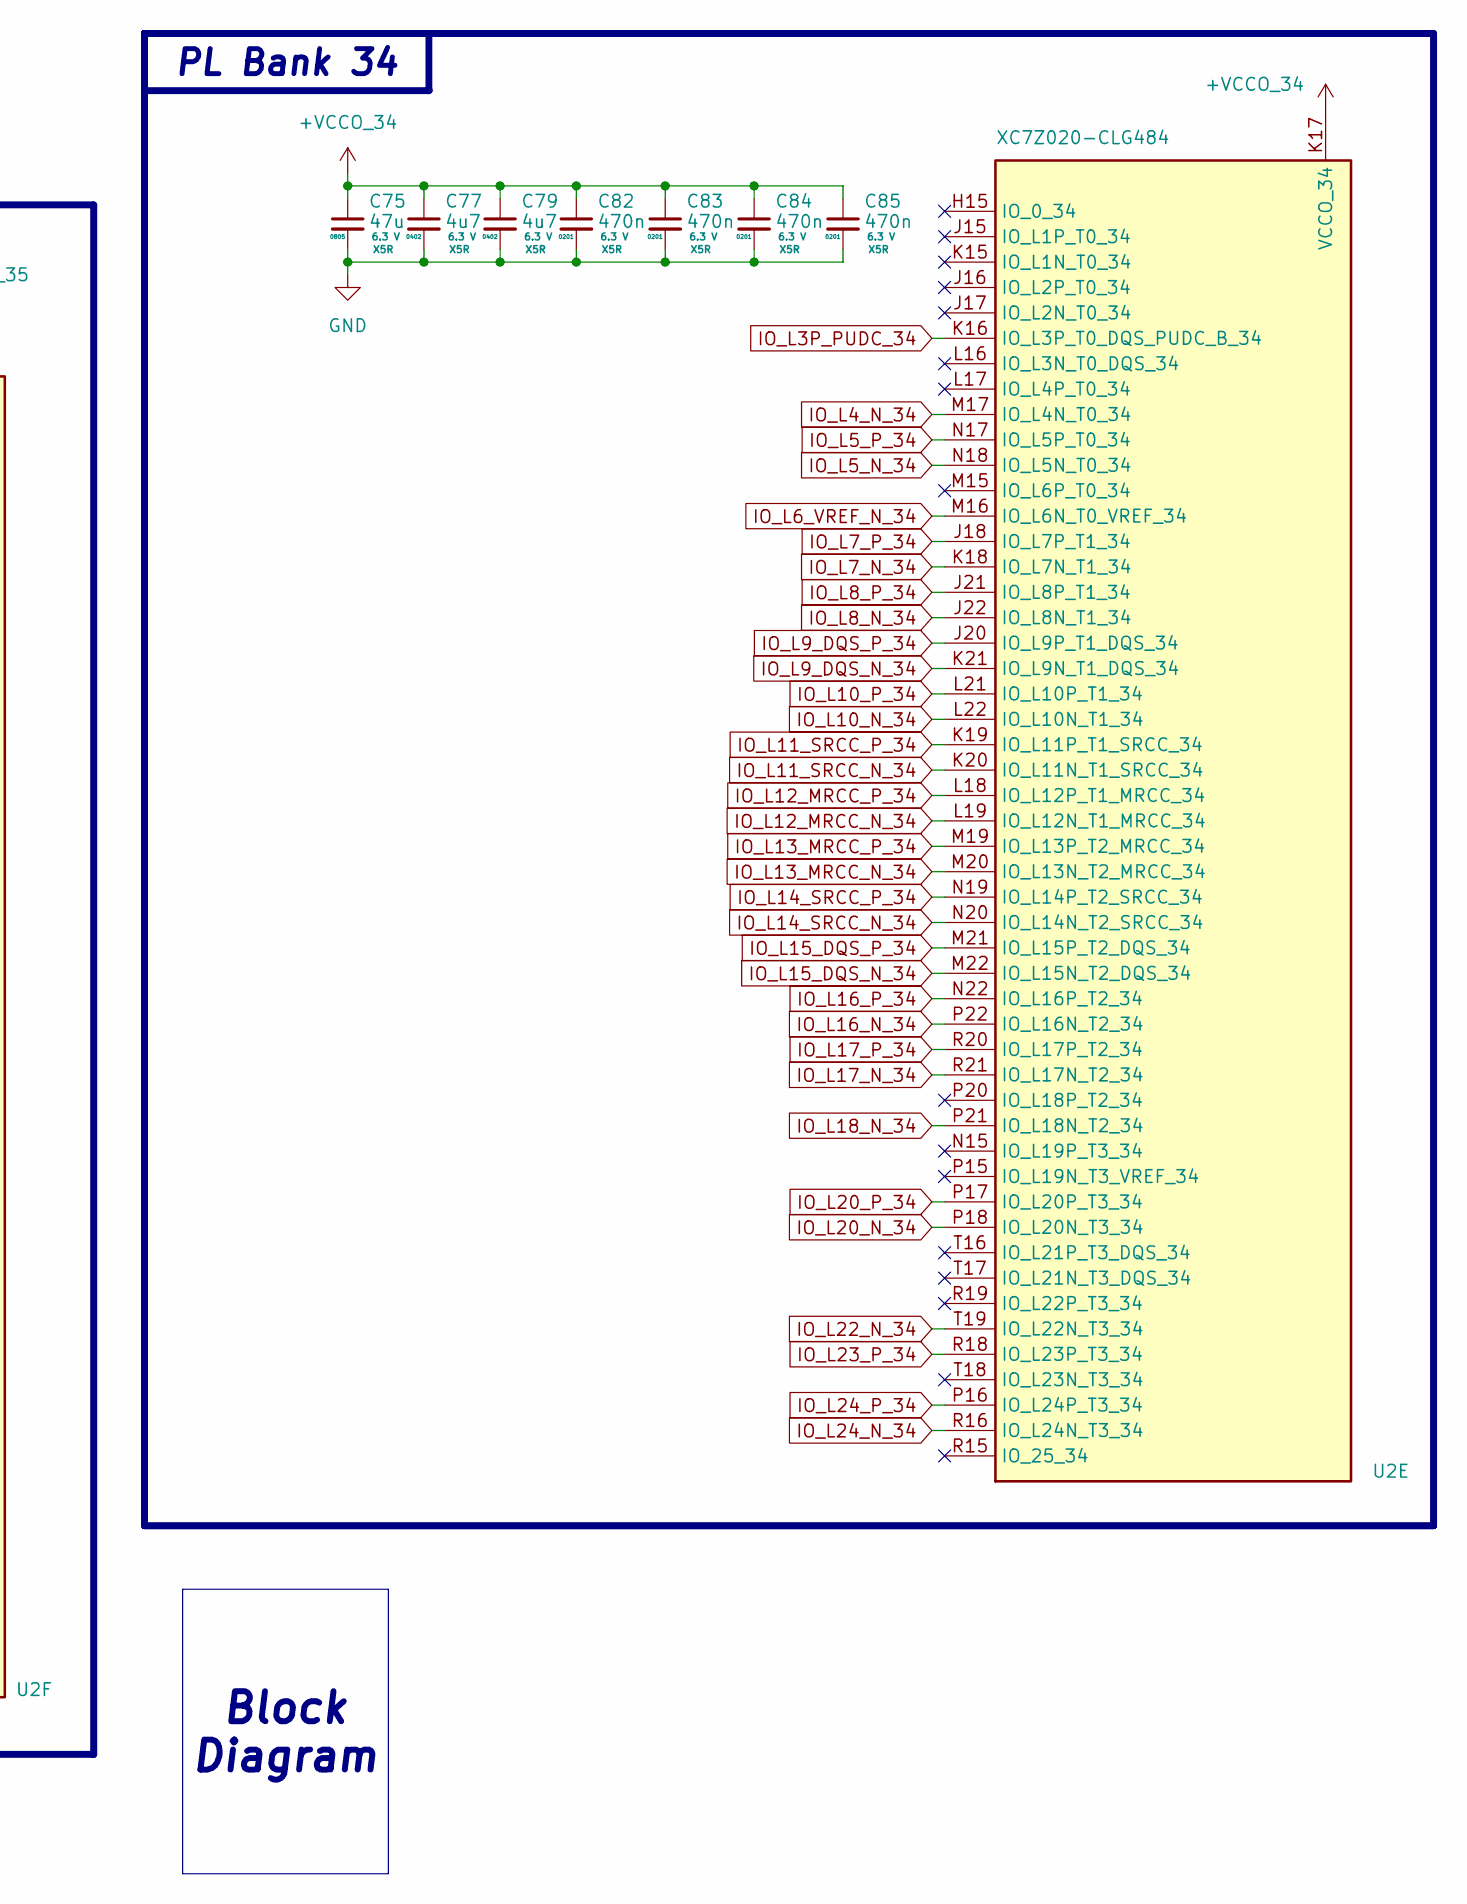
[picture p31: schematic zynq_b33_b34_b35.kicad_sch, part in row 1, column 2]

Parts:
C69, C72, C80, C81, C82, C83, C84, C85: 470n; C_0201_0603Metric; Rating 6.3 V; LCSC Part C85926
C70, C77, C78, C79: 4u7; C_0402_1005Metric; Rating 6.3 V; LCSC Part C368809
C74, C75: 47u; C_0805_2012Metric; Rating 6.3 V; LCSC Part C16780
U2: XC7Z020-CLG484; CLG484_XIL-L_new; LCSC Part gia

Connections:
+VCCO_34: C75.1, C77.1, C79.1, C82.1, C83.1, C84.1, C85.1, U2.K17 (VCCO_34), U2.L20 (VCCO_34), U2.N16 (VCCO_34), U2.P19 (VCCO_34), U2.R22 (VCCO_34), U2.T15 (VCCO_34)
+VCCO_35: C69.1, C70.1, C72.1, C74.1, C78.1, C80.1, C81.1, U2.A20 (VCCO_35), U2.C16 (VCCO_35), U2.D19 (VCCO_35), U2.E22 (VCCO_35), U2.F15 (VCCO_35), U2.G18 (VCCO_35), U2.H21 (VCCO_35)
ETH_PHY_INT: U2.B16 (IO_L8P_T1_AD10P_35)
GND: C69.2, C70.2, C72.2, C74.2, C75.2, C77.2, C78.2, C79.2, C80.2, C81.2, C82.2, C83.2, C84.2, C85.2
IO_0_35: U2.H17 (IO_0_35)
IO_L1_N_35: U2.E16 (IO_L1N_T0_AD0N_35)
IO_L1_P_35: U2.F16 (IO_L1P_T0_AD0P_35)
IO_L2_N_35: U2.D17 (IO_L2N_T0_AD8N_35)
IO_L3P_PUDC_34: U2.K16 (IO_L3P_T0_DQS_PUDC_B_34)
IO_L4_N_34: U2.M17 (IO_L4N_T0_34)
IO_L4_N_35: U2.G16 (IO_L4N_T0_35)
IO_L4_P_35: U2.G15 (IO_L4P_T0_35)
IO_L5_N_34: U2.N18 (IO_L5N_T0_34)
IO_L5_N_35: U2.E18 (IO_L5N_T0_AD9N_35)
IO_L5_P_34: U2.N17 (IO_L5P_T0_34)
IO_L5_P_35: U2.F18 (IO_L5P_T0_AD9P_35)
IO_L6_P_35: U2.G17 (IO_L6P_T0_35)
IO_L6_VREF_N_34: U2.M16 (IO_L6N_T0_VREF_34)
IO_L6_VREF_N_35: U2.F17 (IO_L6N_T0_VREF_35)
IO_L7_N_34: U2.K18 (IO_L7N_T1_34)
IO_L7_P_34: U2.J18 (IO_L7P_T1_34)
IO_L8_N_34: U2.J22 (IO_L8N_T1_34)
IO_L8_N_35: U2.B17 (IO_L8N_T1_AD10N_35)
IO_L8_P_34: U2.J21 (IO_L8P_T1_34)
IO_L9_DQS_N_34: U2.K21 (IO_L9N_T1_DQS_34)
IO_L9_DQS_P_34: U2.J20 (IO_L9P_T1_DQS_34)
IO_L10_N_34: U2.L22 (IO_L10N_T1_34)
IO_L10_N_35: U2.A19 (IO_L10N_T1_AD11N_35)
IO_L10_P_34: U2.L21 (IO_L10P_T1_34)
IO_L10_P_35: U2.A18 (IO_L10P_T1_AD11P_35)
IO_L11_SRCC_N_34: U2.K20 (IO_L11N_T1_SRCC_34)
IO_L11_SRCC_N_35: U2.C18 (IO_L11N_T1_SRCC_35)
IO_L11_SRCC_P_34: U2.K19 (IO_L11P_T1_SRCC_34)
IO_L11_SRCC_P_35: U2.C17 (IO_L11P_T1_SRCC_35)
IO_L12_MRCC_N_34: U2.L19 (IO_L12N_T1_MRCC_34)
IO_L12_MRCC_N_35: U2.C19 (IO_L12N_T1_MRCC_35)
IO_L12_MRCC_P_34: U2.L18 (IO_L12P_T1_MRCC_34)
IO_L12_MRCC_P_35: U2.D18 (IO_L12P_T1_MRCC_35)
IO_L13_MRCC_N_34: U2.M20 (IO_L13N_T2_MRCC_34)
IO_L13_MRCC_N_35: U2.B20 (IO_L13N_T2_MRCC_35)
IO_L13_MRCC_P_34: U2.M19 (IO_L13P_T2_MRCC_34)
IO_L13_MRCC_P_35: U2.B19 (IO_L13P_T2_MRCC_35)
IO_L14_SRCC_N_34: U2.N20 (IO_L14N_T2_SRCC_34)
IO_L14_SRCC_N_35: U2.C20 (IO_L14N_T2_AD4N_SRCC_35)
IO_L14_SRCC_P_34: U2.N19 (IO_L14P_T2_SRCC_34)
IO_L14_SRCC_P_35: U2.D20 (IO_L14P_T2_AD4P_SRCC_35)
IO_L15_DQS_N_34: U2.M22 (IO_L15N_T2_DQS_34)
IO_L15_DQS_N_35: U2.A22 (IO_L15N_T2_DQS_AD12N_35)
IO_L15_DQS_P_34: U2.M21 (IO_L15P_T2_DQS_34)
IO_L15_DQS_P_35: U2.A21 (IO_L15P_T2_DQS_AD12P_35)
IO_L16_N_34: U2.P22 (IO_L16N_T2_34)
IO_L16_N_35: U2.C22 (IO_L16N_T2_35)
IO_L16_P_34: U2.N22 (IO_L16P_T2_34)
IO_L16_P_35: U2.D22 (IO_L16P_T2_35)
IO_L17_N_34: U2.R21 (IO_L17N_T2_34)
IO_L17_N_35: U2.D21 (IO_L17N_T2_AD5N_35)
IO_L17_P_34: U2.R20 (IO_L17P_T2_34)
IO_L17_P_35: U2.E21 (IO_L17P_T2_AD5P_35)
IO_L18_N_34: U2.P21 (IO_L18N_T2_34)
IO_L18_N_35: U2.B22 (IO_L18N_T2_AD13N_35)
IO_L18_P_35: U2.B21 (IO_L18P_T2_AD13P_35)
IO_L19_N_VREF_35: U2.H20 (IO_L19N_T3_VREF_35)
IO_L19_P_35: U2.H19 (IO_L19P_T3_35)
IO_L20_N_34: U2.P18 (IO_L20N_T3_34)
IO_L20_N_35: U2.F19 (IO_L20N_T3_AD6N_35)
IO_L20_P_34: U2.P17 (IO_L20P_T3_34)
IO_L20_P_35: U2.G19 (IO_L20P_T3_AD6P_35)
IO_L21_DQS_N_35: U2.E20 (IO_L21N_T3_DQS_AD14N_35)
IO_L21_DQS_P_35: U2.E19 (IO_L21P_T3_DQS_AD14P_35)
IO_L22_N_34: U2.T19 (IO_L22N_T3_34)
IO_L22_N_35: U2.G21 (IO_L22N_T3_AD7N_35)
IO_L22_P_35: U2.G20 (IO_L22P_T3_AD7P_35)
IO_L23_N_35: U2.F22 (IO_L23N_T3_35)
IO_L23_P_34: U2.R18 (IO_L23P_T3_34)
IO_L23_P_35: U2.F21 (IO_L23P_T3_35)
IO_L24_N_34: U2.R16 (IO_L24N_T3_34)
IO_L24_N_35: U2.G22 (IO_L24N_T3_AD15N_35)
IO_L24_P_34: U2.P16 (IO_L24P_T3_34)
IO_L24_P_35: U2.H22 (IO_L24P_T3_AD15P_35)

Notes on the sheet:
Zynq PL Banks 34 & 35
PL Bank 35
PL Bank 34
Block Diagram
