mfkiwl/Zynq-SoM/schematic/zynq_config.kicad_sch

## KiCad design schematic/zynq_config.kicad_sch (2025-04-01)

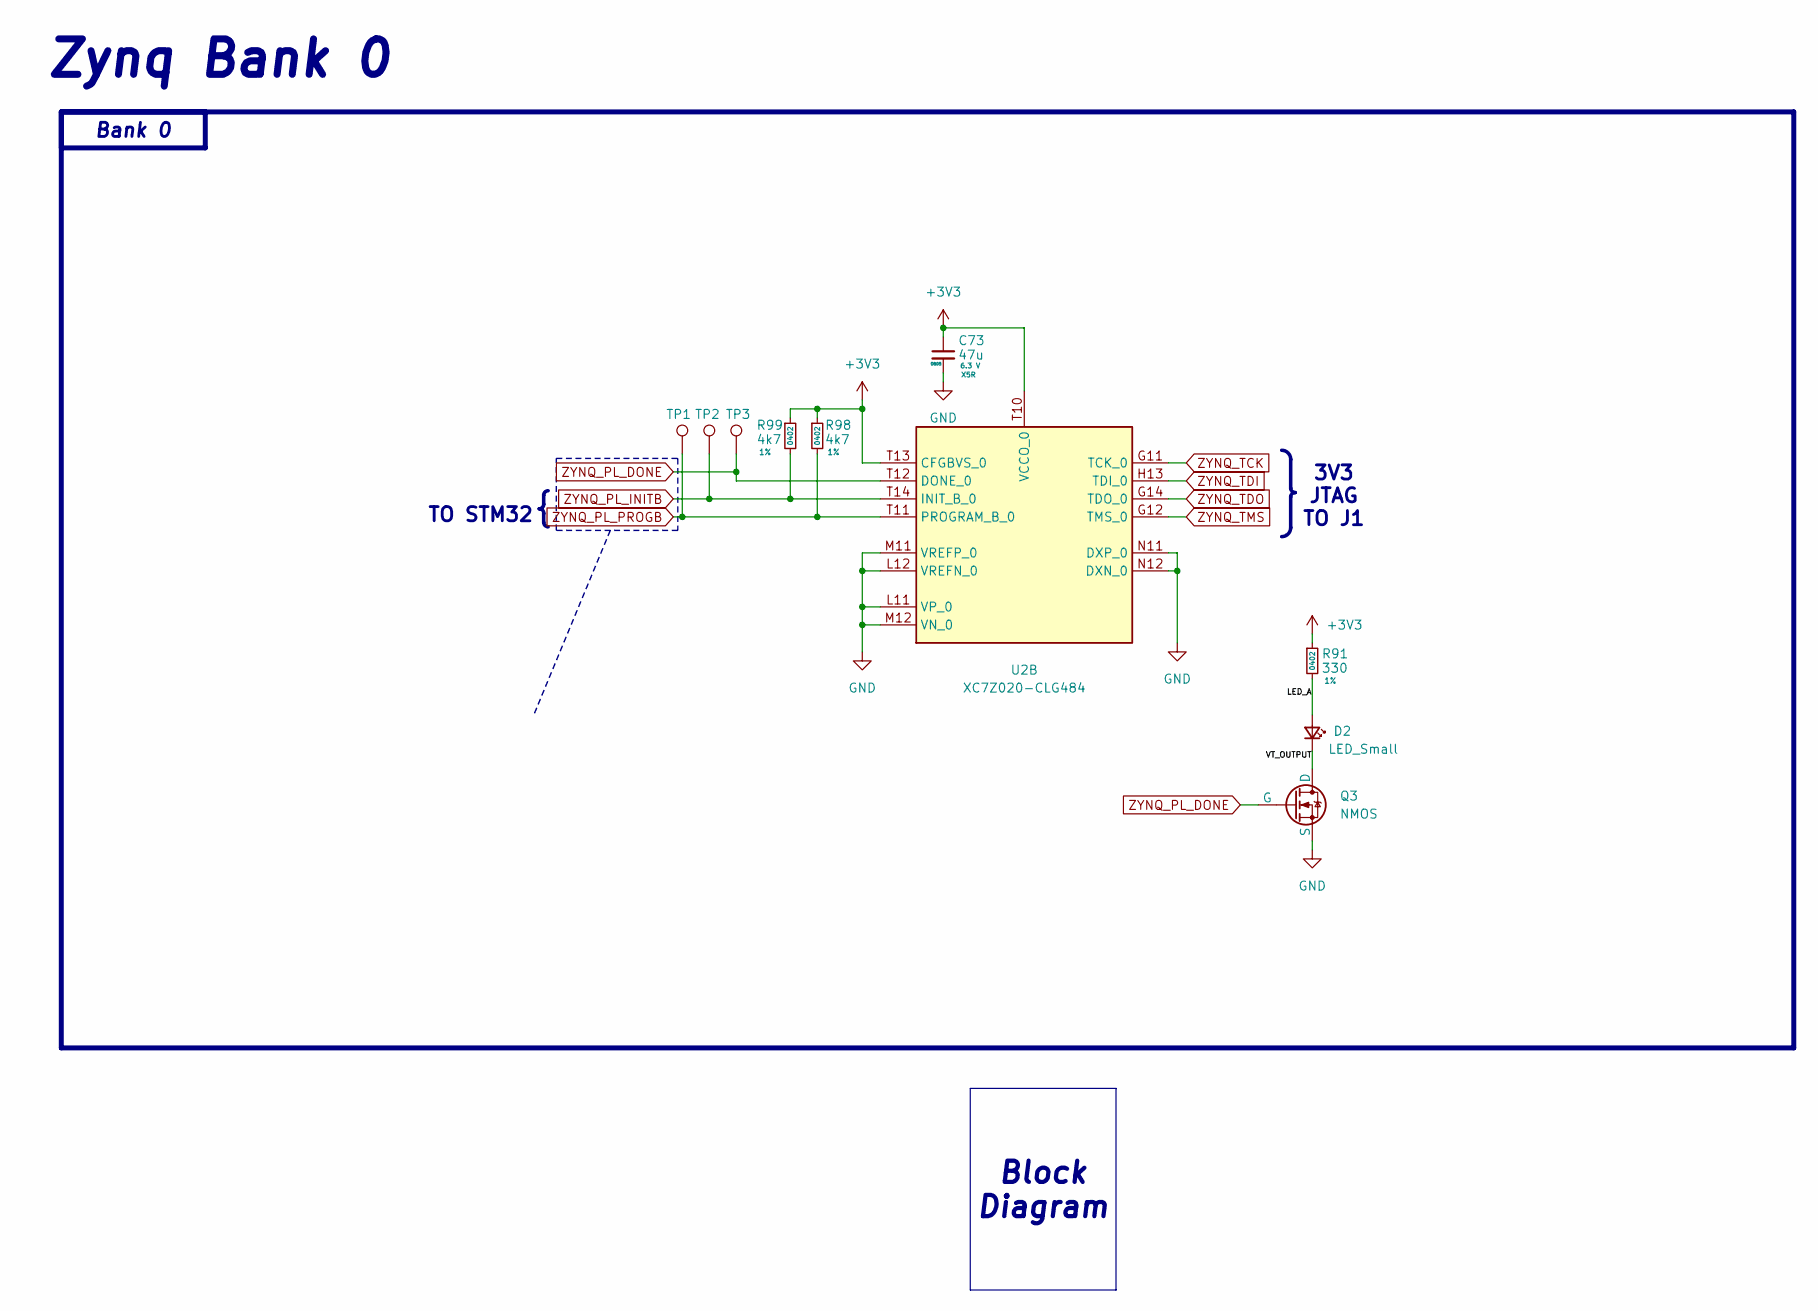
[picture p32: schematic zynq_config.kicad_sch]

Parts:
C73: 47u; C_0805_2012Metric; Rating 6.3 V; LCSC Part C16780
D2: LED_Small; LED_0603_1608Metric
Q3: NMOS; SOT-23
R91: 330; R_0402_1005Metric; Tolerance 1%
R98, R99: 4k7; R_0402_1005Metric; Tolerance 1%; LCSC Part C25940
TP1, TP2, TP3: TestPoint; TestPoint_Pad_D0.7mm
U2: XC7Z020-CLG484; CLG484_XIL-L_new; LCSC Part gia

Connections:
+3V3: C73.1, R91.1, R98.1, R99.1, U2.R12 (VCCO_0), U2.T7 (VCCO_0), U2.T8 (VCCO_0), U2.T10 (VCCO_0), U2.T13 (CFGBVS_0)
GND: C73.2, Q3.3 (S), U2.L11 (VP_0), U2.L12 (VREFN_0), U2.M11 (VREFP_0), U2.M12 (VN_0), U2.N11 (DXP_0), U2.N12 (DXN_0)
LED_A: D2.2 (A), R91.2
VT_OUTPUT: D2.1 (K), Q3.1 (D)
ZYNQ_PL_DONE: Q3.2 (G), TP3.1, U2.T12 (DONE_0)
ZYNQ_PL_INITB: R99.2, TP2.1, U2.T14 (INIT_B_0)
ZYNQ_PL_PROGB: R98.2, TP1.1, U2.T11 (PROGRAM_B_0)
ZYNQ_TCK: U2.G11 (TCK_0)
ZYNQ_TDI: U2.H13 (TDI_0)
ZYNQ_TDO: U2.G14 (TDO_0)
ZYNQ_TMS: U2.G12 (TMS_0)

Notes on the sheet:
Zynq Bank 0
TO STM32
3V3 JTAG TO J1
Block Diagram
Bank 0
