mfkiwl/Zynq-SoM/schematic/zynq_power.kicad_sch

## KiCad design schematic/zynq_power.kicad_sch (2025-04-01)

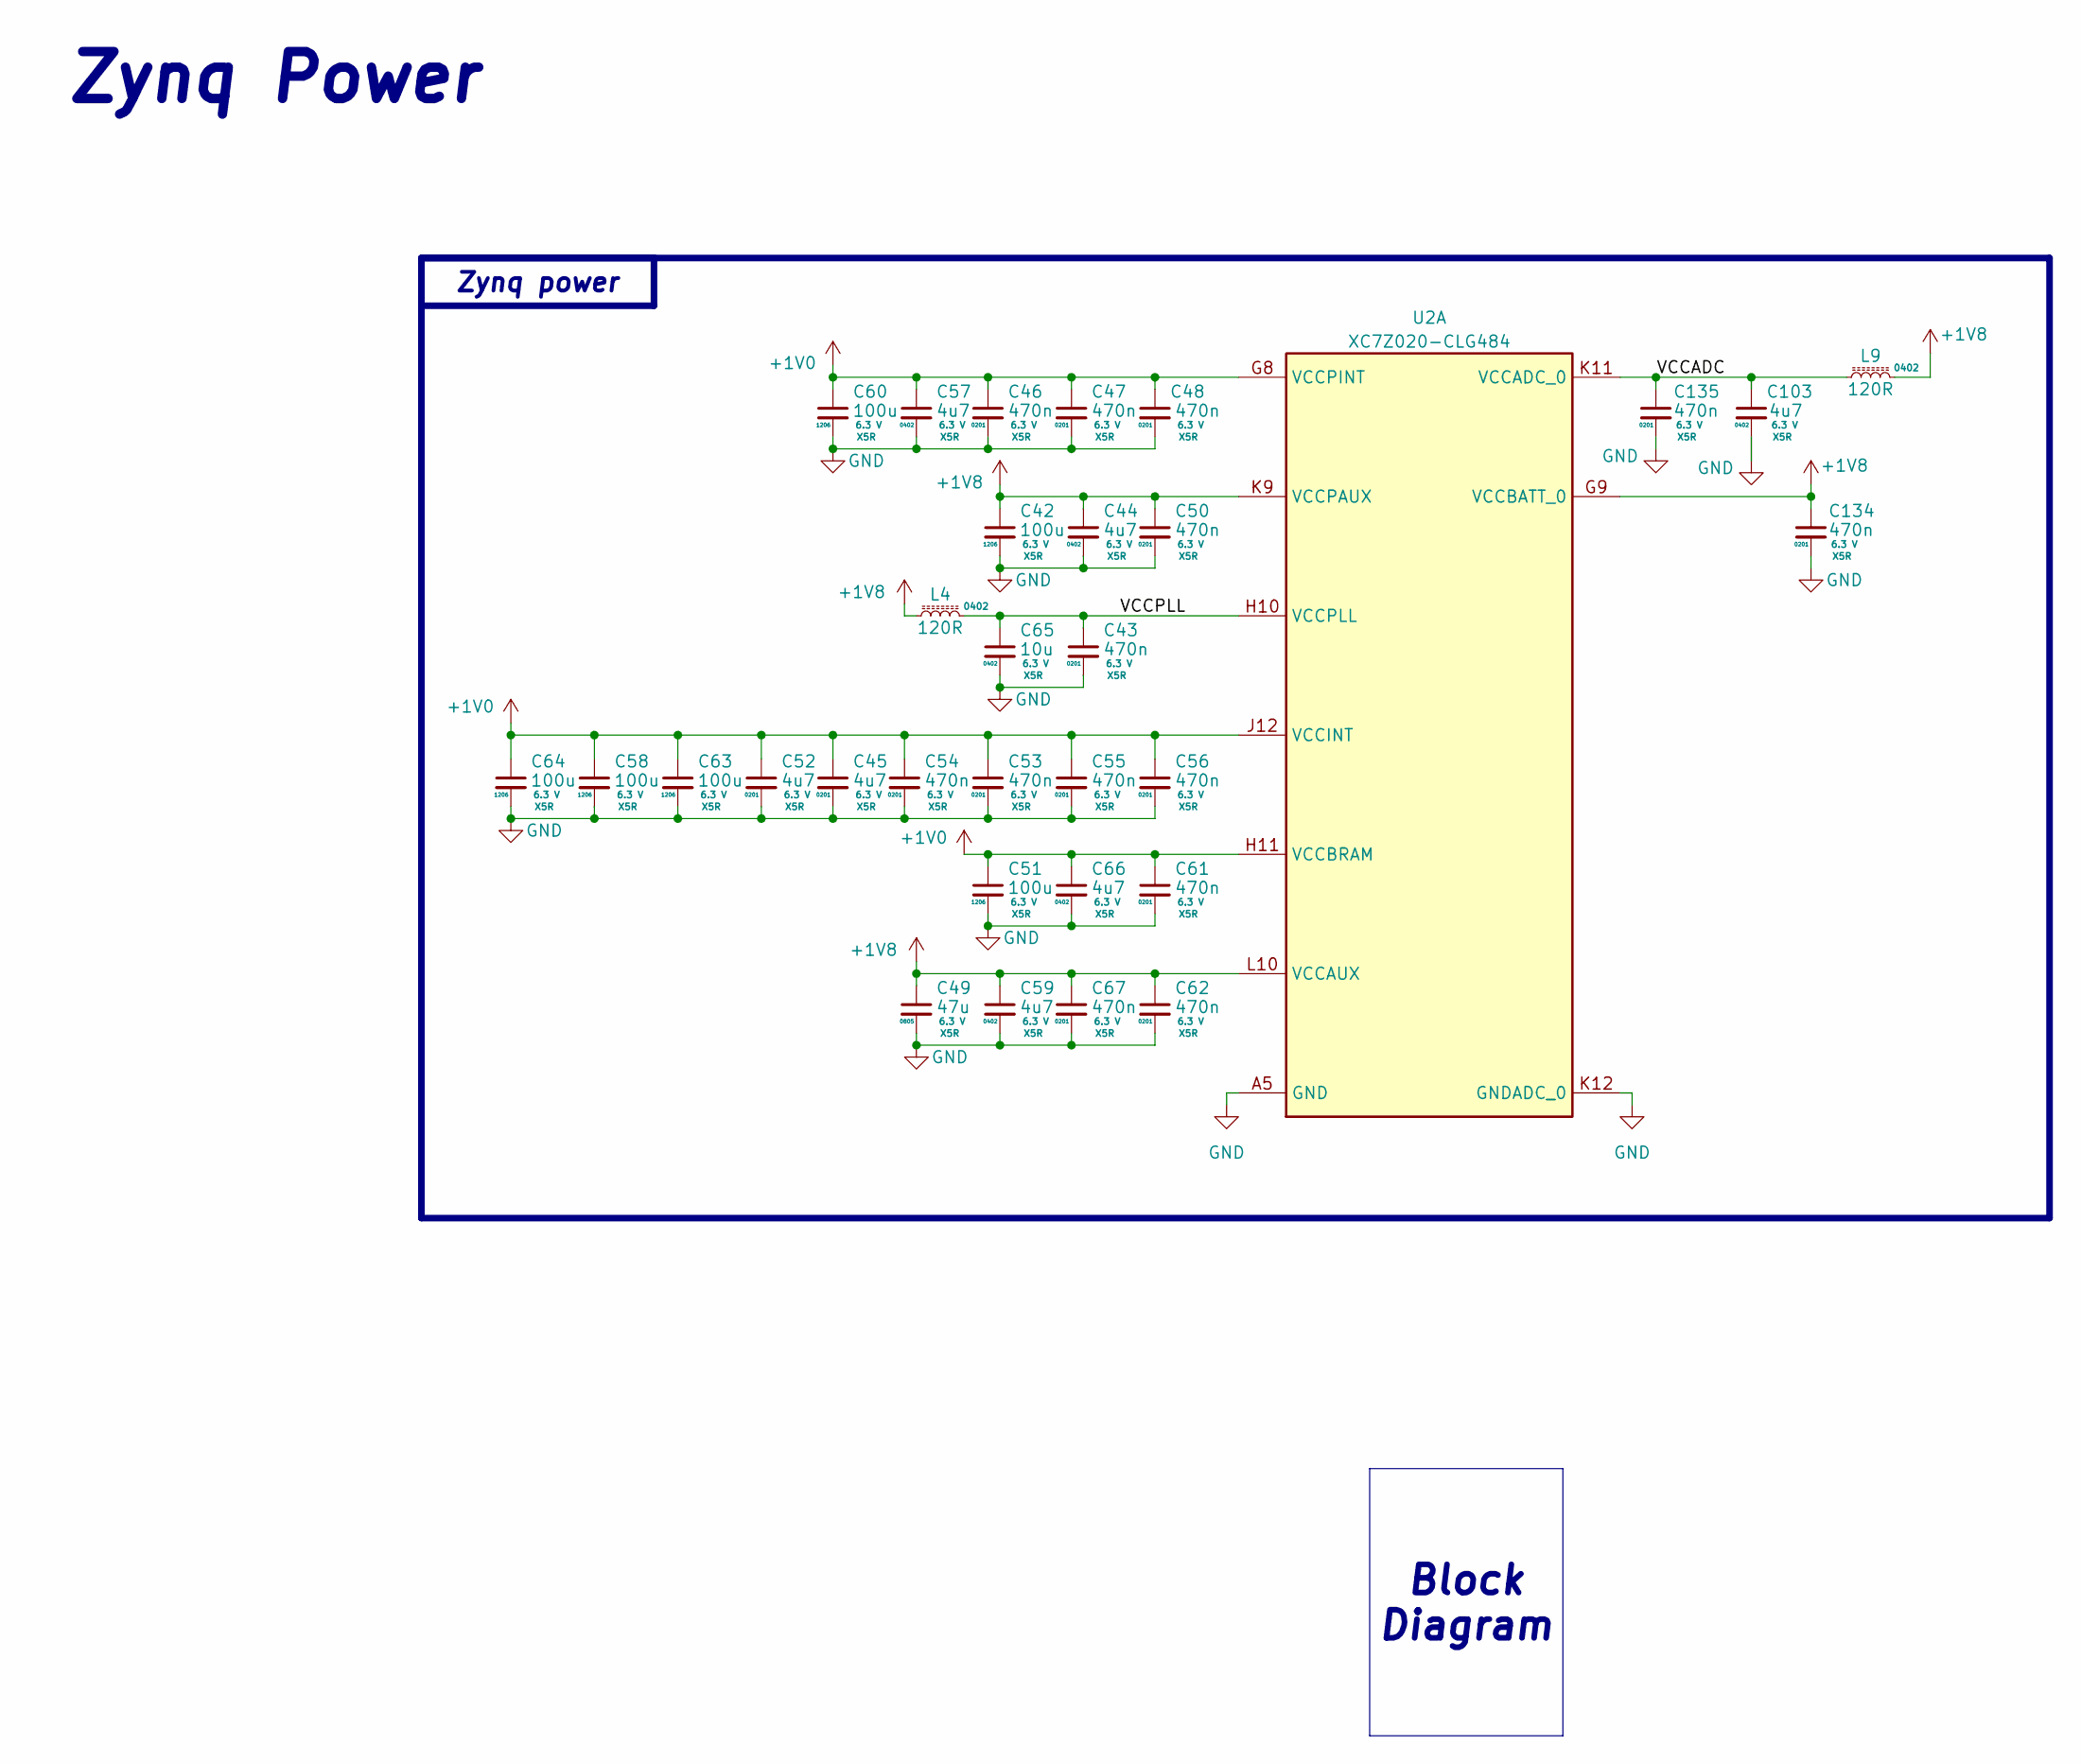
[picture p33: schematic zynq_power.kicad_sch]

Parts:
C42, C51, C58, C60, C63, C64: 100u; C_1206_3216Metric; Rating 6.3 V; LCSC Part C15008
C43, C46, C47, C48, C50, C53, C54, C55, C56, C61, C62, C67, C134, C135: 470n; C_0201_0603Metric; Rating 6.3 V; LCSC Part C85926
C44, C45, C52, C57, C59, C66, C103: 4u7; C_0402_1005Metric; Rating 6.3 V; LCSC Part C368809
C49: 47u; C_0805_2012Metric; Rating 6.3 V; LCSC Part C16780
C65: 10u; C_0402_1005Metric; Rating 6.3 V; LCSC Part C15525////
L4, L9: 120R; L_0402_1005Metric; LCSC Part C275478
U2: XC7Z020-CLG484; CLG484_XIL-L_new; LCSC Part gia

Connections:
+1V0: C45.1, C46.1, C47.1, C48.1, C51.1, C52.1, C53.1, C54.1, C55.1, C56.1, C57.1, C58.1, C60.1, C61.1, C63.1, C64.1, C66.1, U2.G8 (VCCPINT), U2.H9 (VCCPINT), U2.H11 (VCCBRAM), U2.J8 (VCCPINT), U2.J10 (VCCBRAM), U2.J12 (VCCINT), U2.J14 (VCCINT), U2.K13 (VCCINT), U2.L8 (VCCPINT), U2.L14 (VCCINT), U2.M13 (VCCINT), U2.N8 (VCCPINT), U2.N14 (VCCINT), U2.P13 (VCCINT), U2.R8 (VCCPINT), U2.R14 (VCCINT)
+1V8: C42.1, C44.1, C49.1, C50.1, C59.1, C62.1, C67.1, C134.1, L4.1, L9.2, U2.G9 (VCCBATT_0), U2.K9 (VCCPAUX), U2.L10 (VCCAUX), U2.M9 (VCCPAUX), U2.N10 (VCCAUX), U2.P9 (VCCPAUX), U2.P11 (VCCAUX), U2.R10 (VCCAUX), U2.T9 (VCCPAUX)
GND: C42.2, C43.2, C44.2, C45.2, C46.2, C47.2, C48.2, C49.2, C50.2, C51.2, C52.2, C53.2, C54.2, C55.2, C56.2, C57.2, C58.2, C59.2, C60.2, C61.2, C62.2, C63.2, C64.2, C65.2, C66.2, C67.2, C103.2, C134.2, C135.2, U2.A5 (GND), U2.A15 (GND), U2.AA5 (GND), U2.AA15 (GND), U2.AB8 (GND), U2.AB18 (GND), U2.B8 (GND), U2.B18 (GND), U2.C1 (GND), U2.C11 (GND), U2.C21 (GND), U2.D4 (GND), U2.D14 (GND), U2.E7 (GND), U2.E17 (GND), U2.F10 (GND), U2.F20 (GND), U2.G3 (GND), U2.H6 (GND), U2.H8 (GND), U2.H12 (GND), U2.H14 (GND), U2.H16 (GND), U2.J9 (GND), U2.J11 (GND), U2.J13 (GND), U2.J19 (GND), U2.K2 (GND), U2.K8 (GND), U2.K10 (GND), U2.K12 (GNDADC_0), U2.K14 (GND), U2.K22 (GND), U2.L5 (GND), U2.L9 (GND), U2.L13 (GND), U2.L15 (GND), U2.M8 (GND), U2.M10 (GND), U2.M14 (GND), U2.M18 (GND), U2.N1 (GND), U2.N9 (GND), U2.N13 (GND), U2.N21 (GND), U2.P4 (GND), U2.P8 (GND), U2.P10 (GND), U2.P12 (GND), U2.P14 (GND), U2.R9 (GND), U2.R11 (GND), U2.R13 (GND), U2.R17 (GND), U2.T20 (GND), U2.U3 (GND), U2.U13 (GND), U2.V6 (GND), U2.V16 (GND), U2.W9 (GND), U2.W19 (GND), U2.Y2 (GND), U2.Y12 (GND), U2.Y22 (GND)
VCCADC: C103.1, C135.1, L9.1, U2.K11 (VCCADC_0)
VCCPLL: C43.1, C65.1, L4.2, U2.H10 (VCCPLL)

Notes on the sheet:
Zynq Power
Zynq power
Block Diagram
